omega9380/Retro-Schematics/Commodore/Amiga/Amiga 1000/Documents/A1000 Daughter Board.jpg

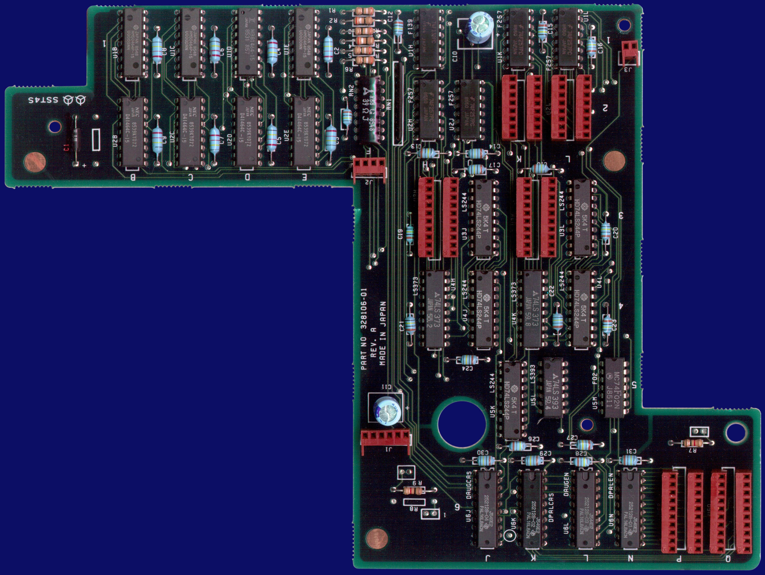
Commodore/Amiga/Amiga 1000/Documents/A1000 Daughter Board.jpg
