omega9380/Retro-Schematics/Commodore/Amiga/Amiga 1000/Documents/A1000_MB.jpg

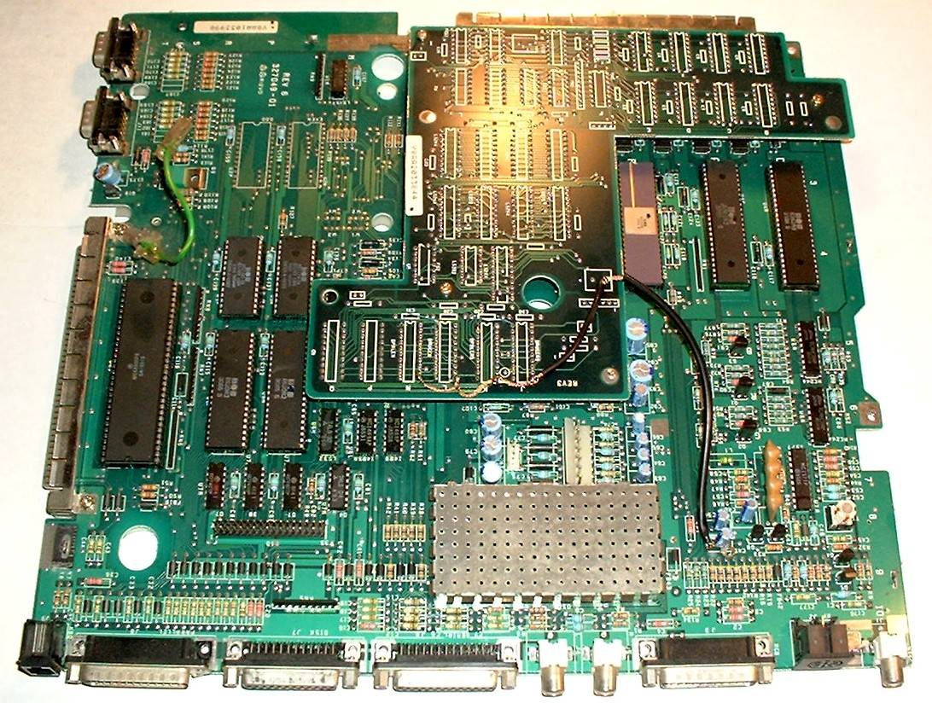
Commodore/Amiga/Amiga 1000/Documents/A1000_MB.jpg
