omega9380/Retro-Schematics/Commodore/Amiga/Amiga 1000/Documents/A1000 Zorro Expansion bus [August, 1985 - PN-328015 Commodore - Rev C].pdf

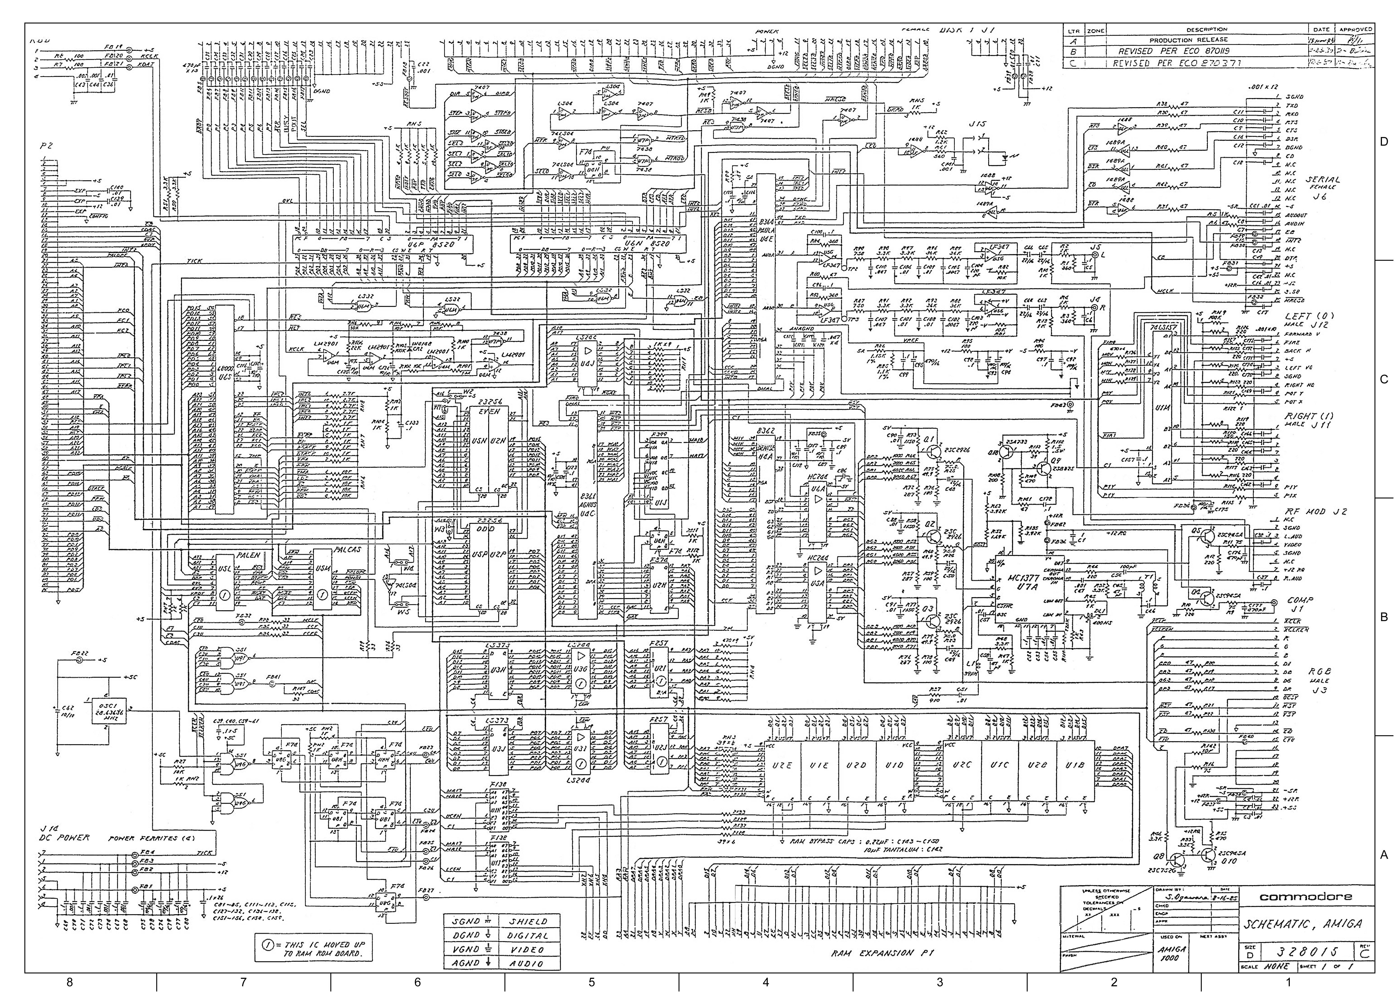
[picture p3: page 1]
