omega9380/Retro-Schematics/Commodore/Amiga/Amiga 1000/Documents/amiga_1000_schematic_1.png

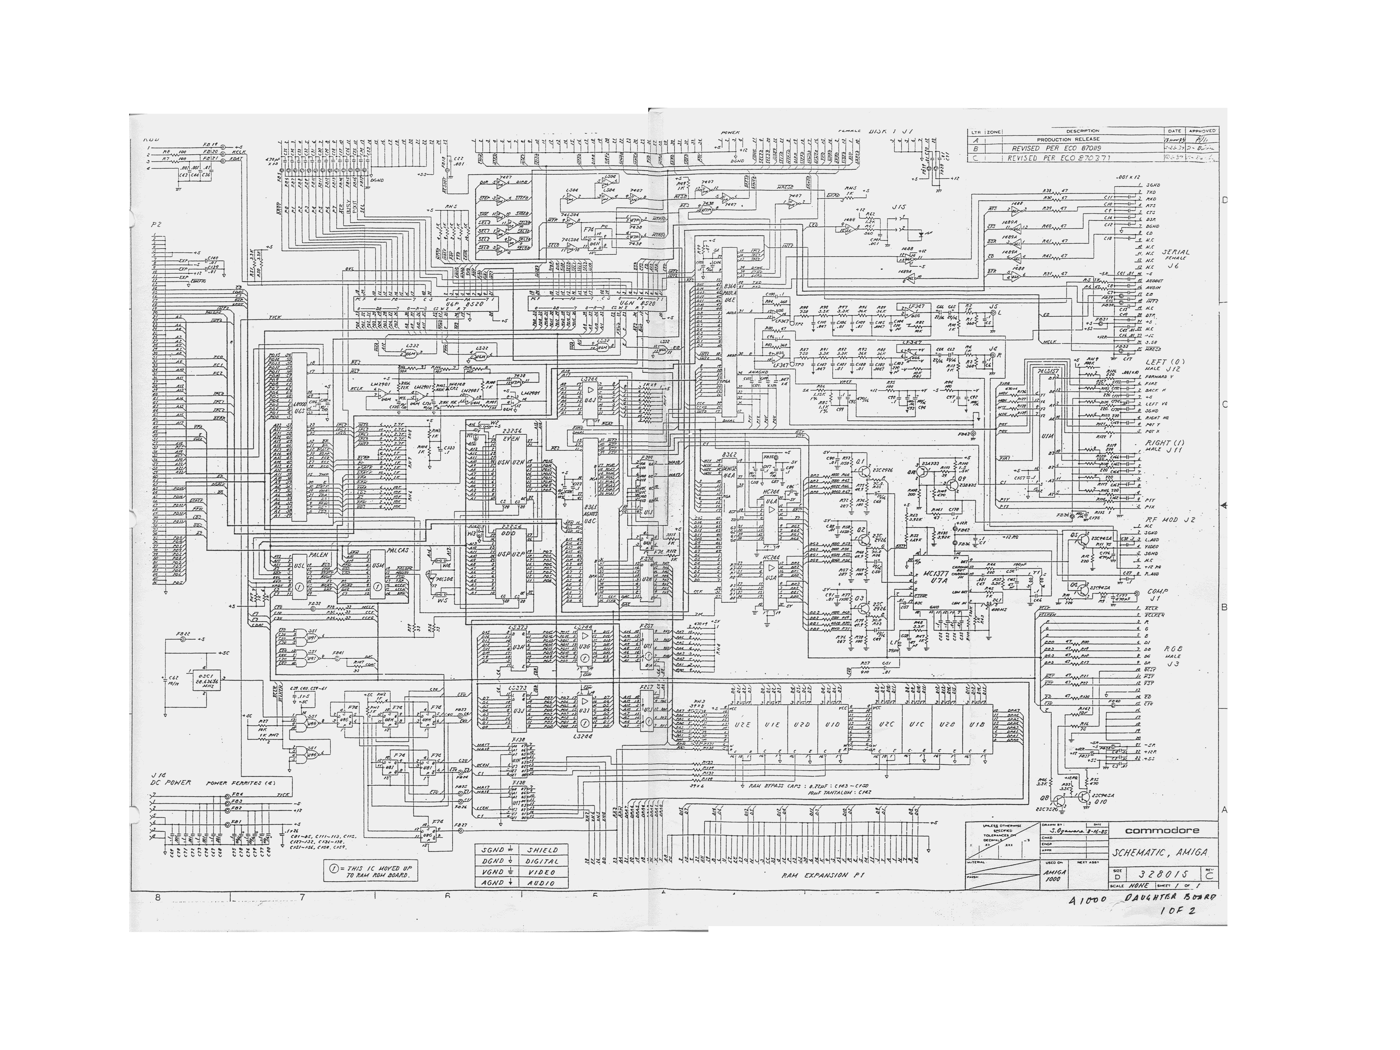
Commodore/Amiga/Amiga 1000/Documents/amiga_1000_schematic_1.png
