omega9380/Retro-Schematics/Commodore/Amiga/Amiga 1000/Documents/Circuit1a.png

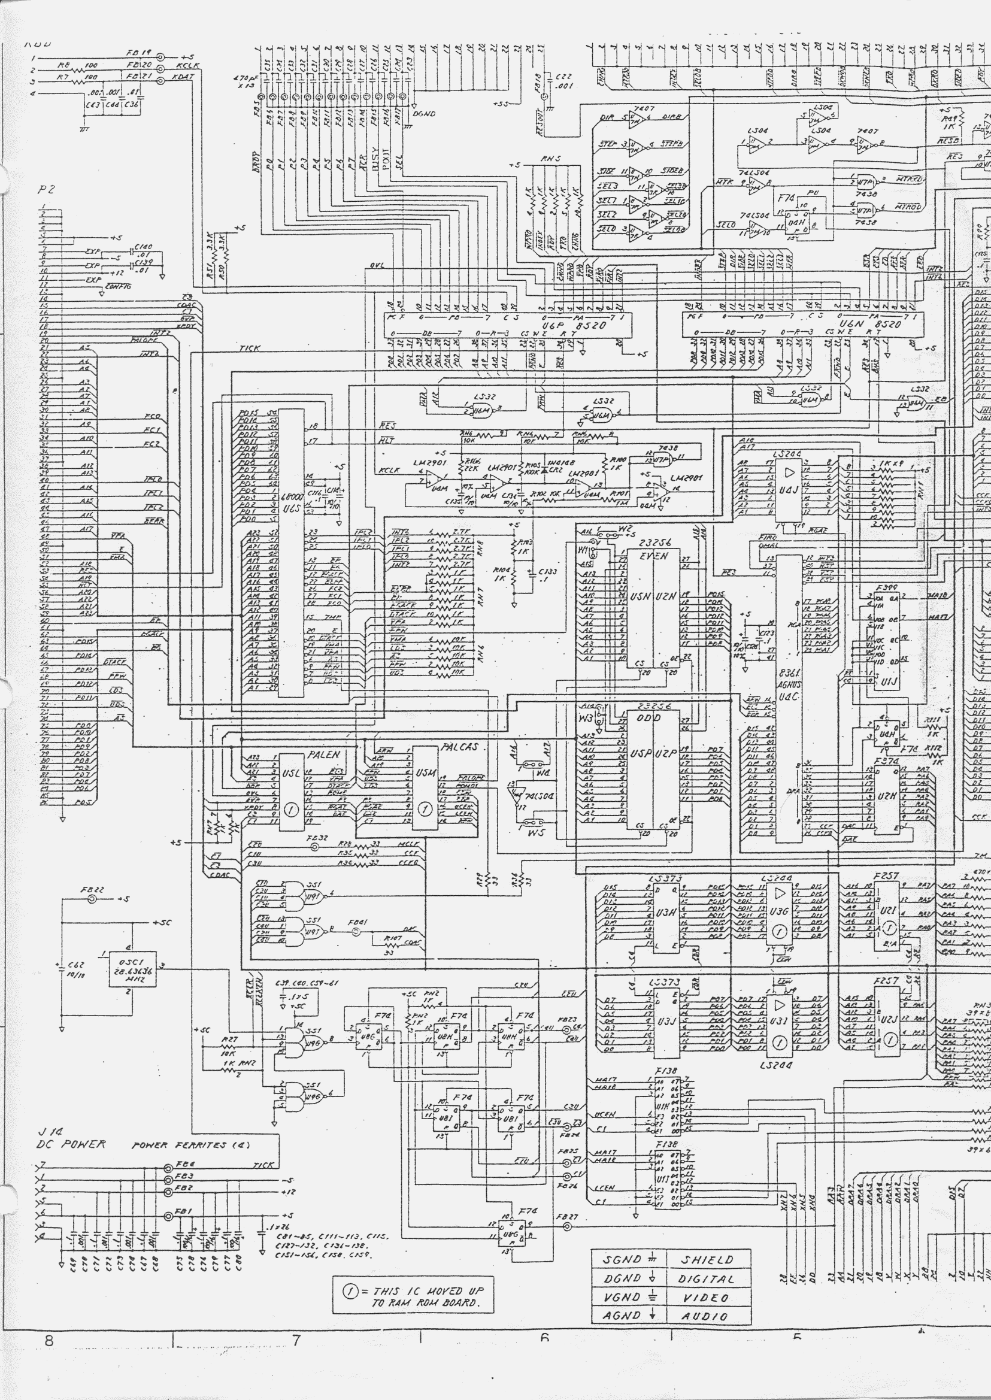
Commodore/Amiga/Amiga 1000/Documents/Circuit1a.png
