omega9380/Retro-Schematics/Commodore/Amiga/Amiga 1000/Documents/Circuit1b.png

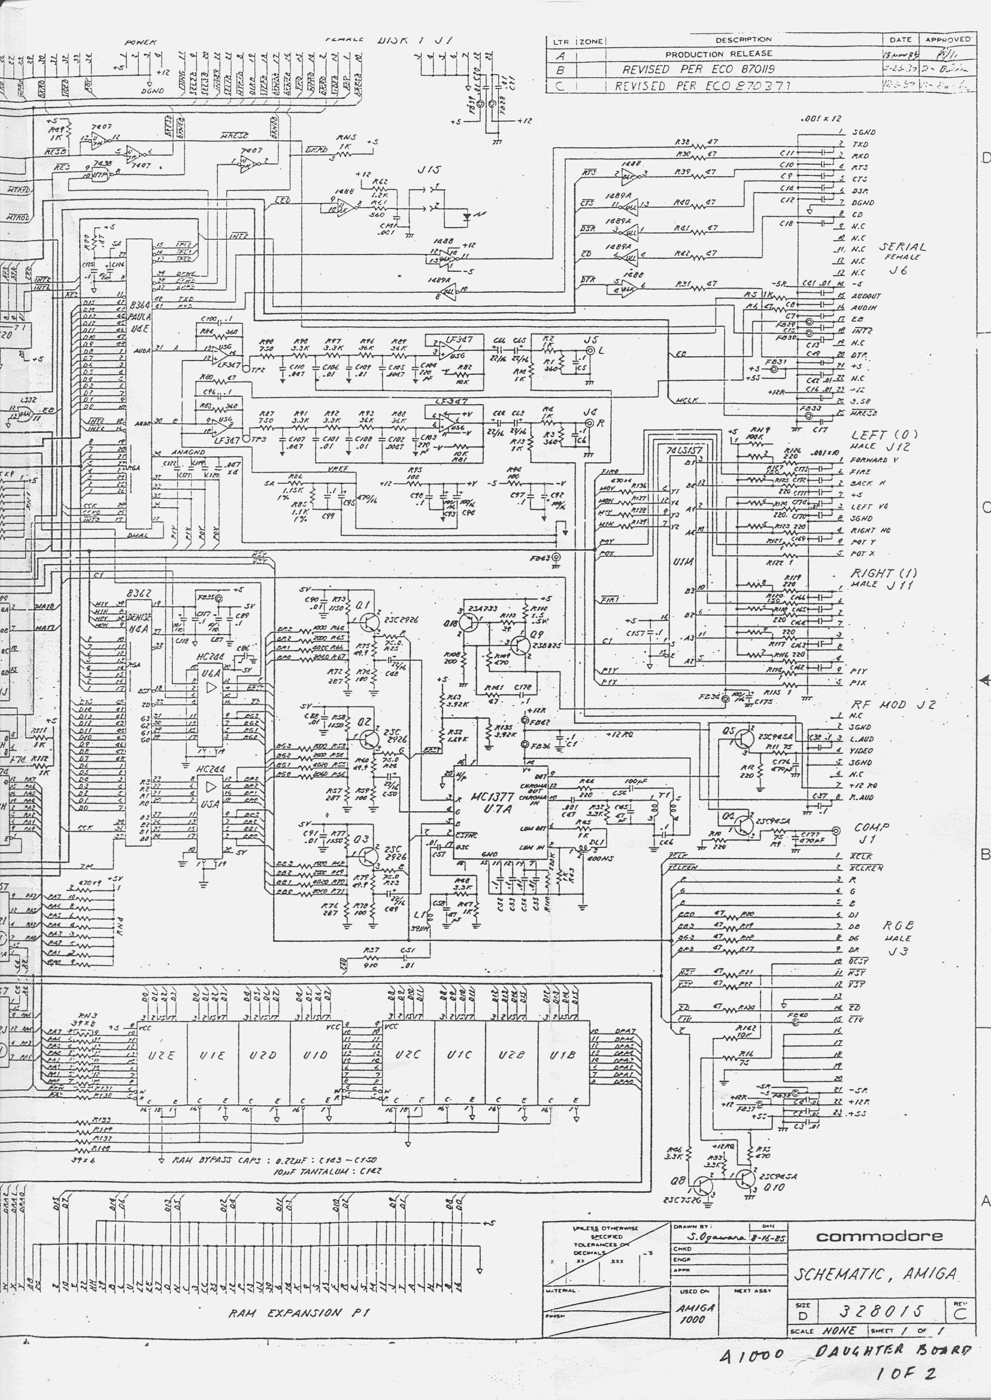
Commodore/Amiga/Amiga 1000/Documents/Circuit1b.png
