omega9380/Retro-Schematics/Commodore/Amiga/Amiga 1000/Documents/Datasheets/pinouts/8361-Agnus-dip.png

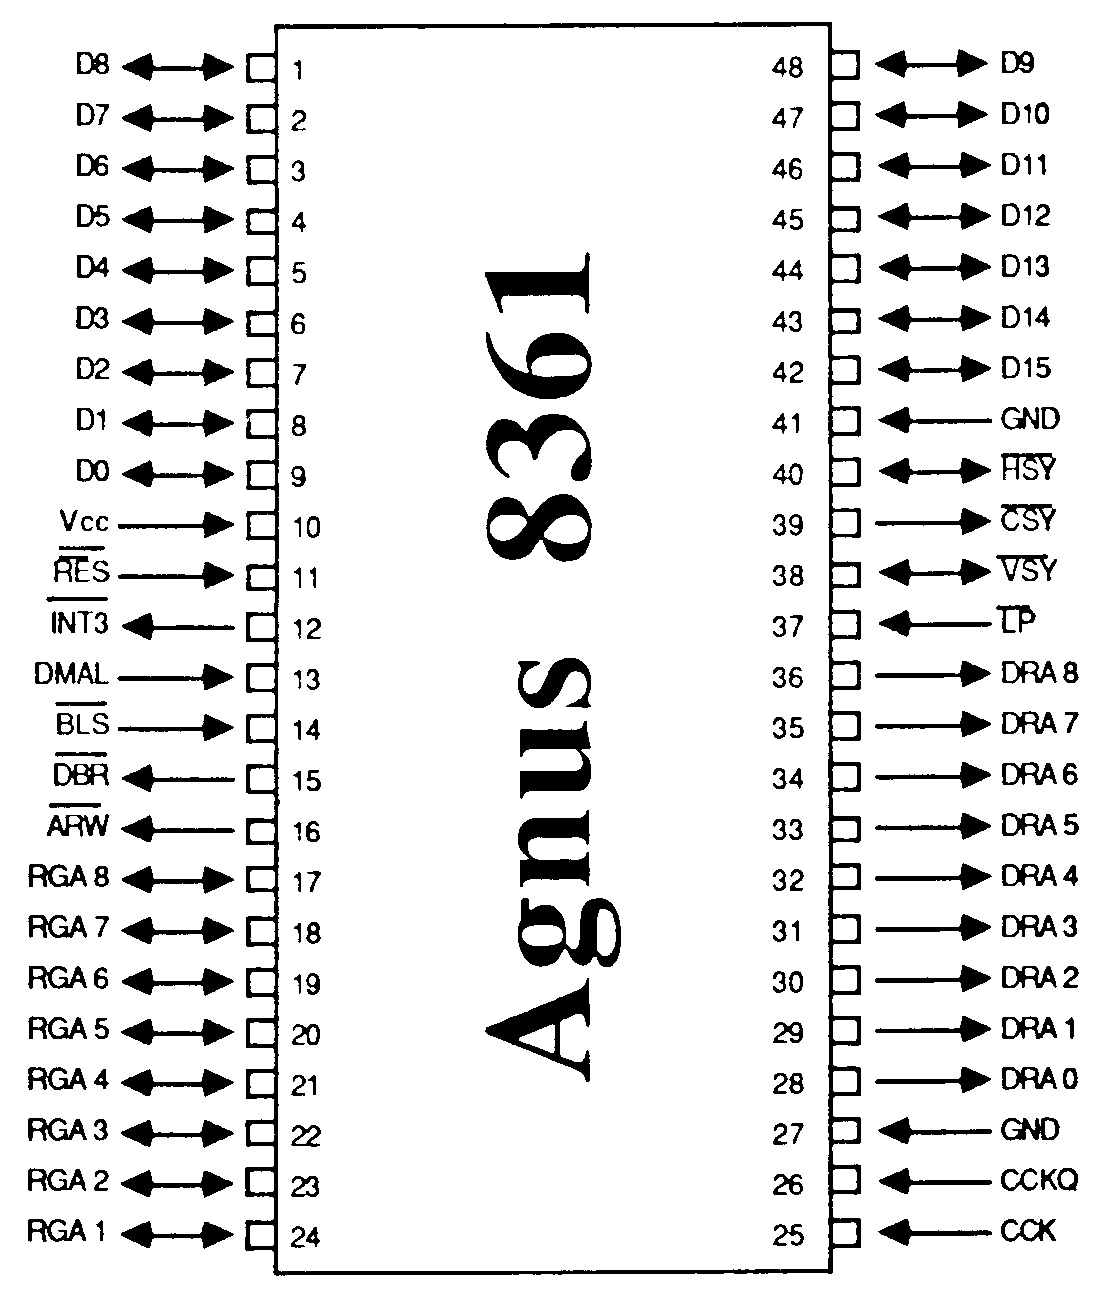
Commodore/Amiga/Amiga 1000/Documents/Datasheets/pinouts/8361-Agnus-dip.png
