omega9380/Retro-Schematics/Commodore/Amiga/Amiga 1000/Documents/Datasheets/pinouts/8370-agnus-plcc.png

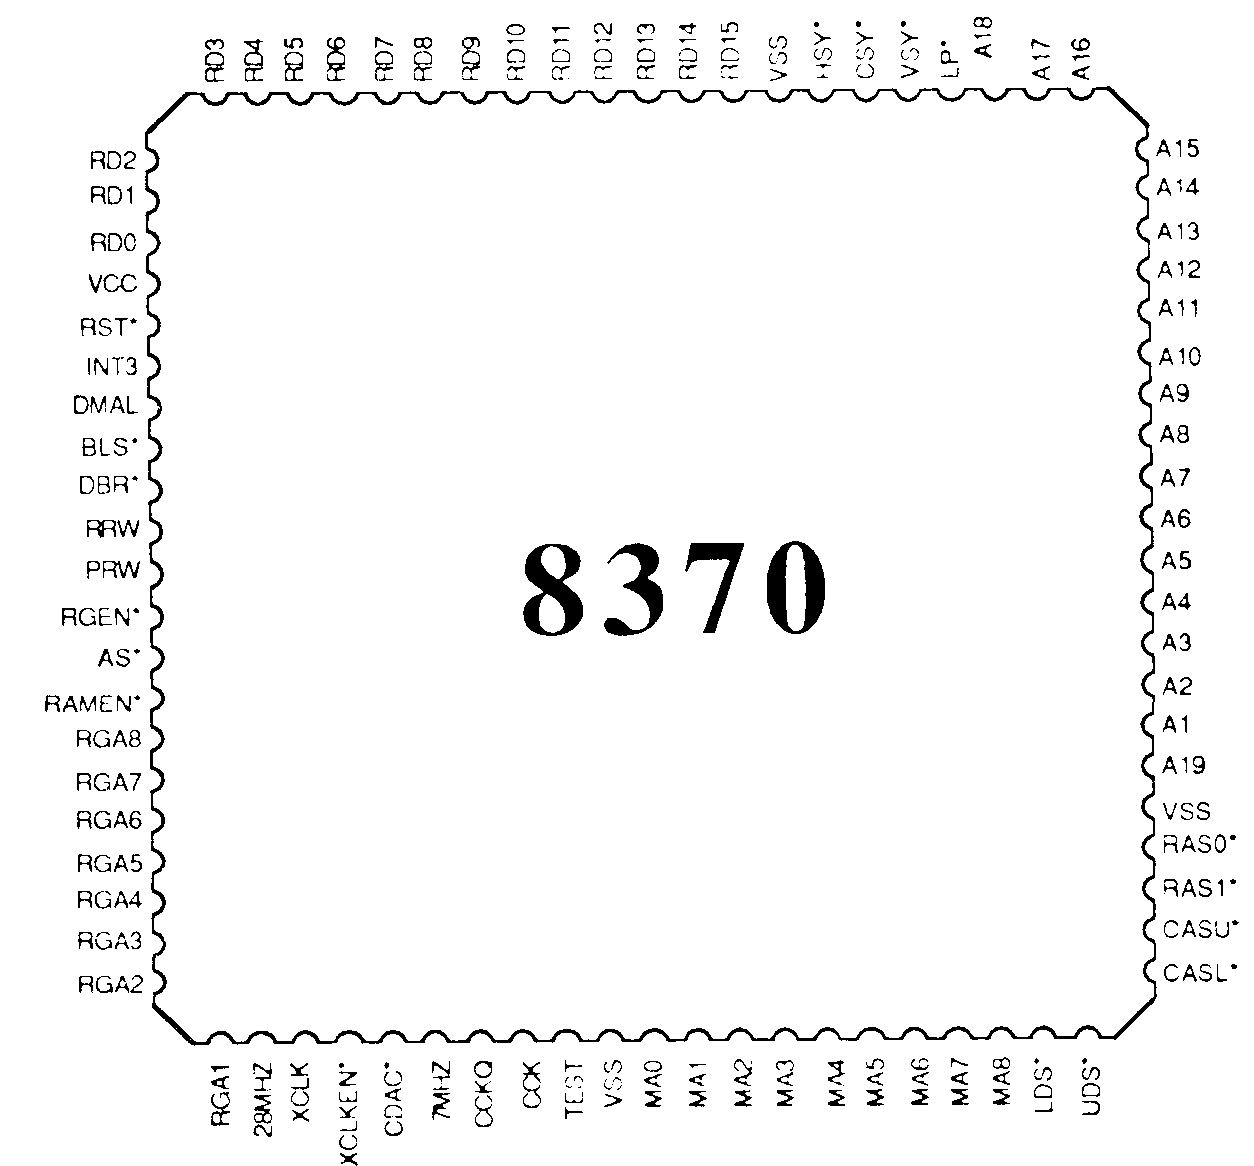
Commodore/Amiga/Amiga 1000/Documents/Datasheets/pinouts/8370-agnus-plcc.png
