omega9380/Retro-Schematics/Commodore/Amiga/Amiga 1000/Documents/Datasheets/pinouts/8520-CIA-dip.png

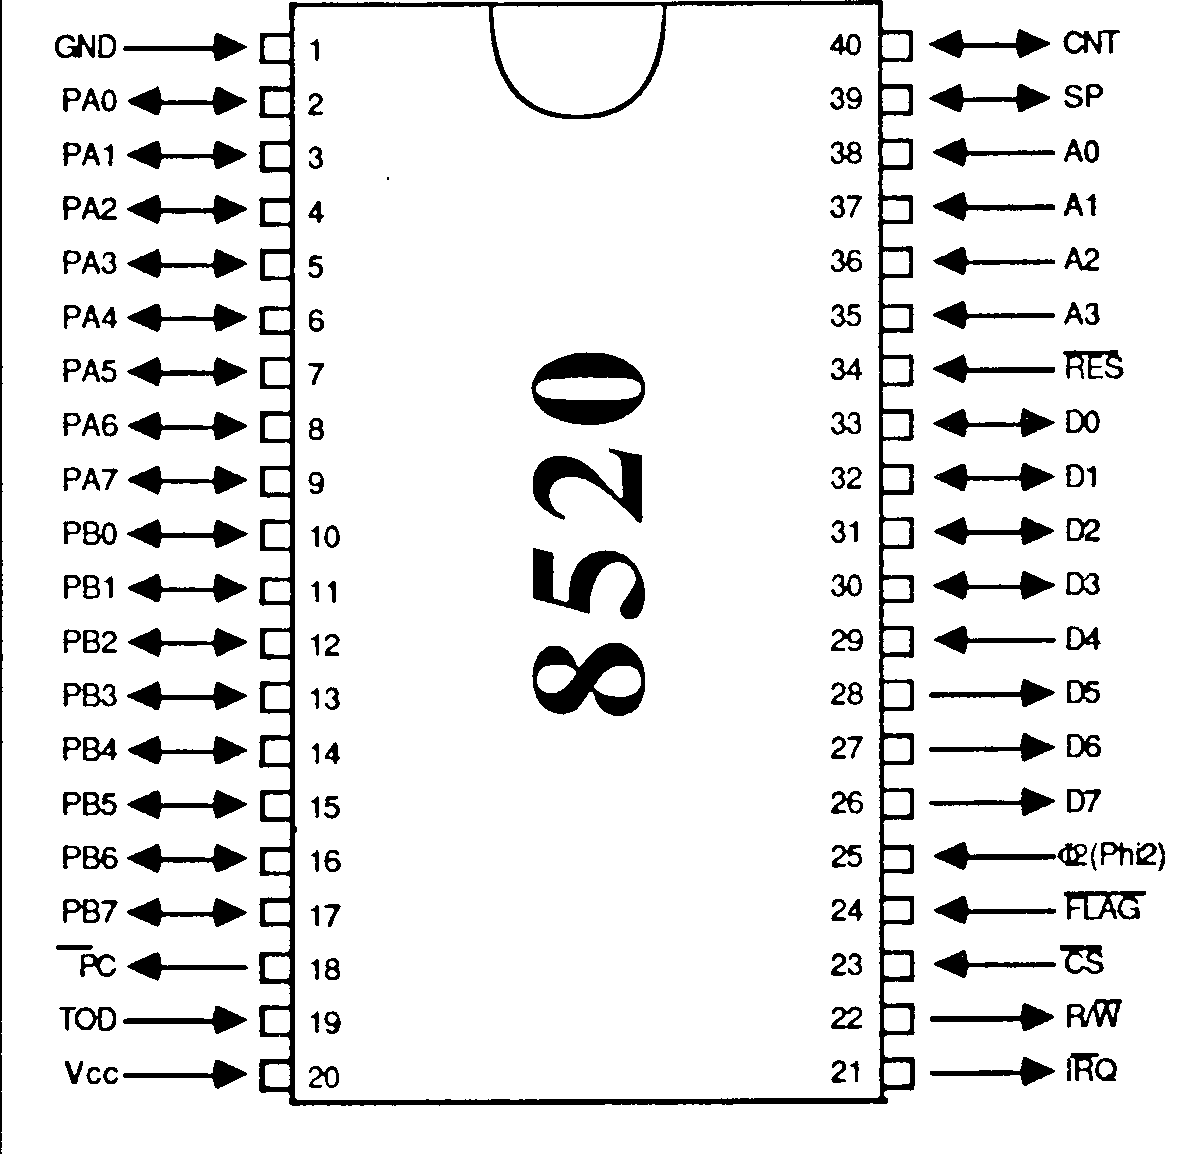
Commodore/Amiga/Amiga 1000/Documents/Datasheets/pinouts/8520-CIA-dip.png
