omega9380/Retro-Schematics/Commodore/Amiga/Amiga 1000/Documents/Datasheets/pinouts/68000-cpu-dip.png

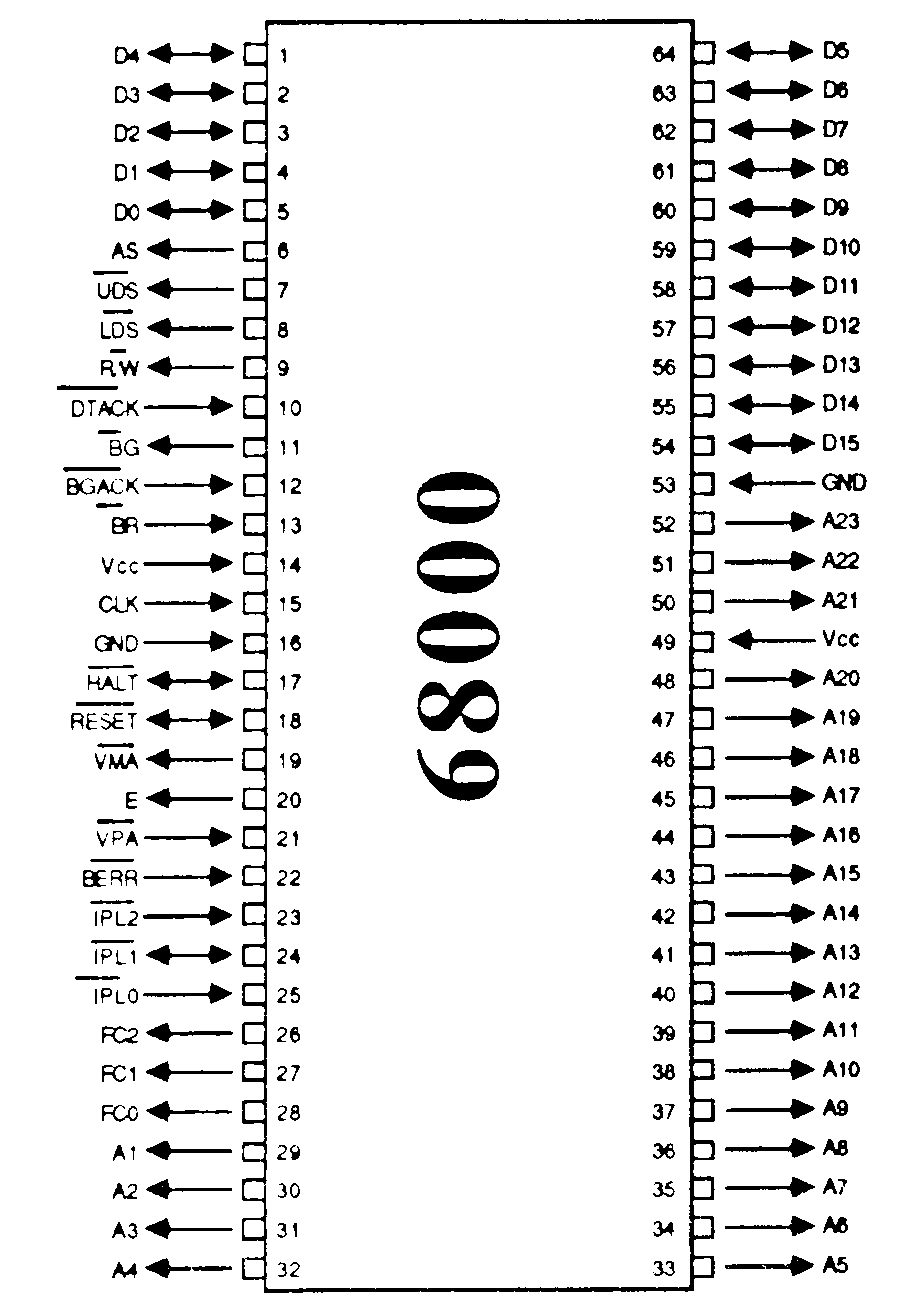
Commodore/Amiga/Amiga 1000/Documents/Datasheets/pinouts/68000-cpu-dip.png
