omega9380/Retro-Schematics/Commodore/Amiga/Amiga 1000/Documents/Datasheets/pinouts/68000.gif

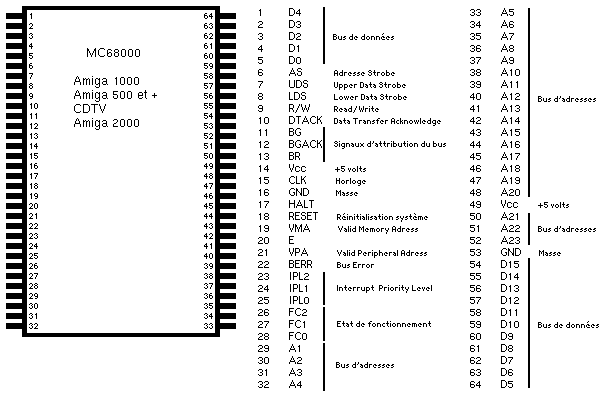
Commodore/Amiga/Amiga 1000/Documents/Datasheets/pinouts/68000.gif
