omega9380/Retro-Schematics/Commodore/Amiga/Amiga 1000/Documents/Datasheets/pinouts/aa-gayle-plcc.png

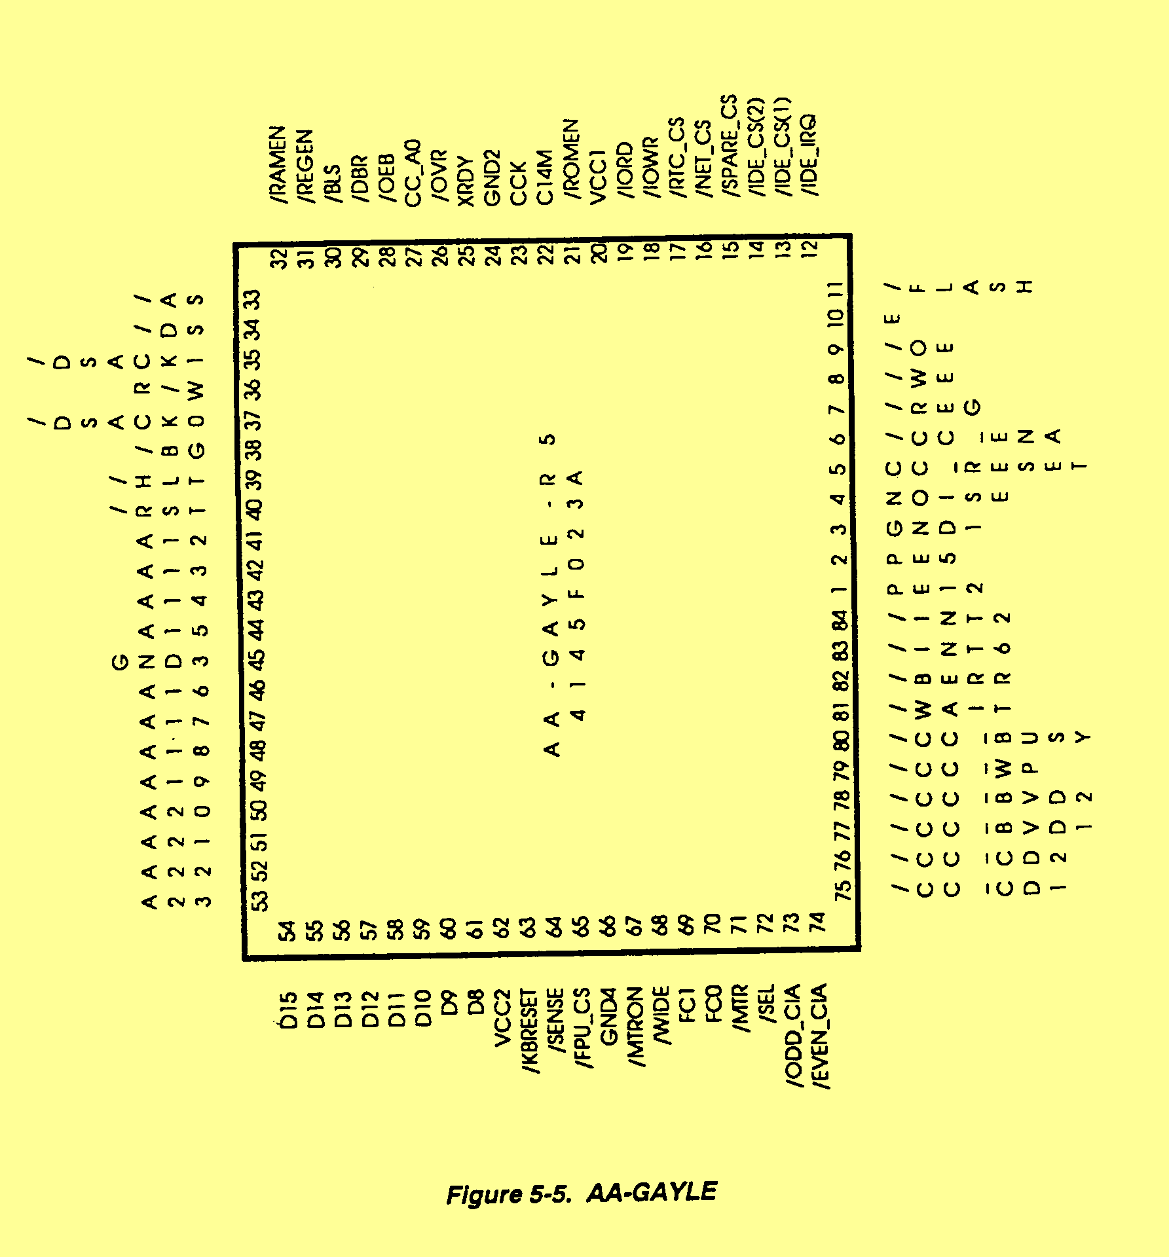
Commodore/Amiga/Amiga 1000/Documents/Datasheets/pinouts/aa-gayle-plcc.png
