omega9380/Retro-Schematics/Commodore/Amiga/Amiga 1000/Documents/Datasheets/pinouts/CIA-B.gif

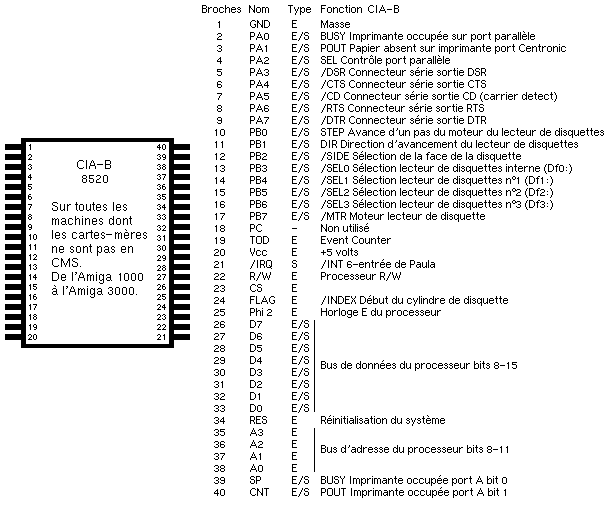
Commodore/Amiga/Amiga 1000/Documents/Datasheets/pinouts/CIA-B.gif
