omega9380/Retro-Schematics/Commodore/Amiga/Amiga 1000/Documents/Datasheets/pinouts/Denise.gif

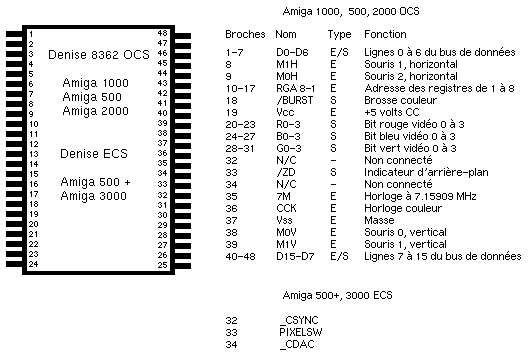
Commodore/Amiga/Amiga 1000/Documents/Datasheets/pinouts/Denise.gif
