omega9380/Retro-Schematics/Commodore/Amiga/Amiga 1000/Documents/Datasheets/pinouts/FatAgnus8372.gif

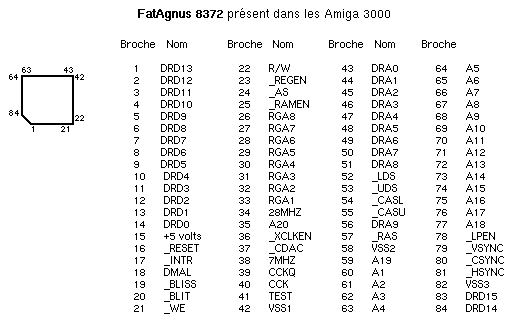
Commodore/Amiga/Amiga 1000/Documents/Datasheets/pinouts/FatAgnus8372.gif
