omega9380/Retro-Schematics/Commodore/Amiga/Amiga 1000/Documents/Datasheets/pinouts/ROM.gif

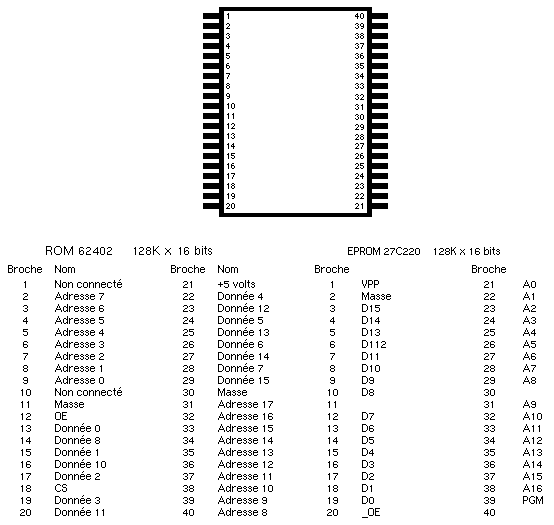
Commodore/Amiga/Amiga 1000/Documents/Datasheets/pinouts/ROM.gif
