omega9380/Retro-Schematics/Commodore/Amiga/Amiga 1000/Documents/Datasheets/pinouts/tsop-package-pic.gif

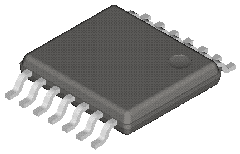
Commodore/Amiga/Amiga 1000/Documents/Datasheets/pinouts/tsop-package-pic.gif
