omega9380/Retro-Schematics/Commodore/Commodore 64/Commodore 64 - Schematic 251138 for PCB Assy 250407/Documents/250469-rev.B-left-corrected2.gif

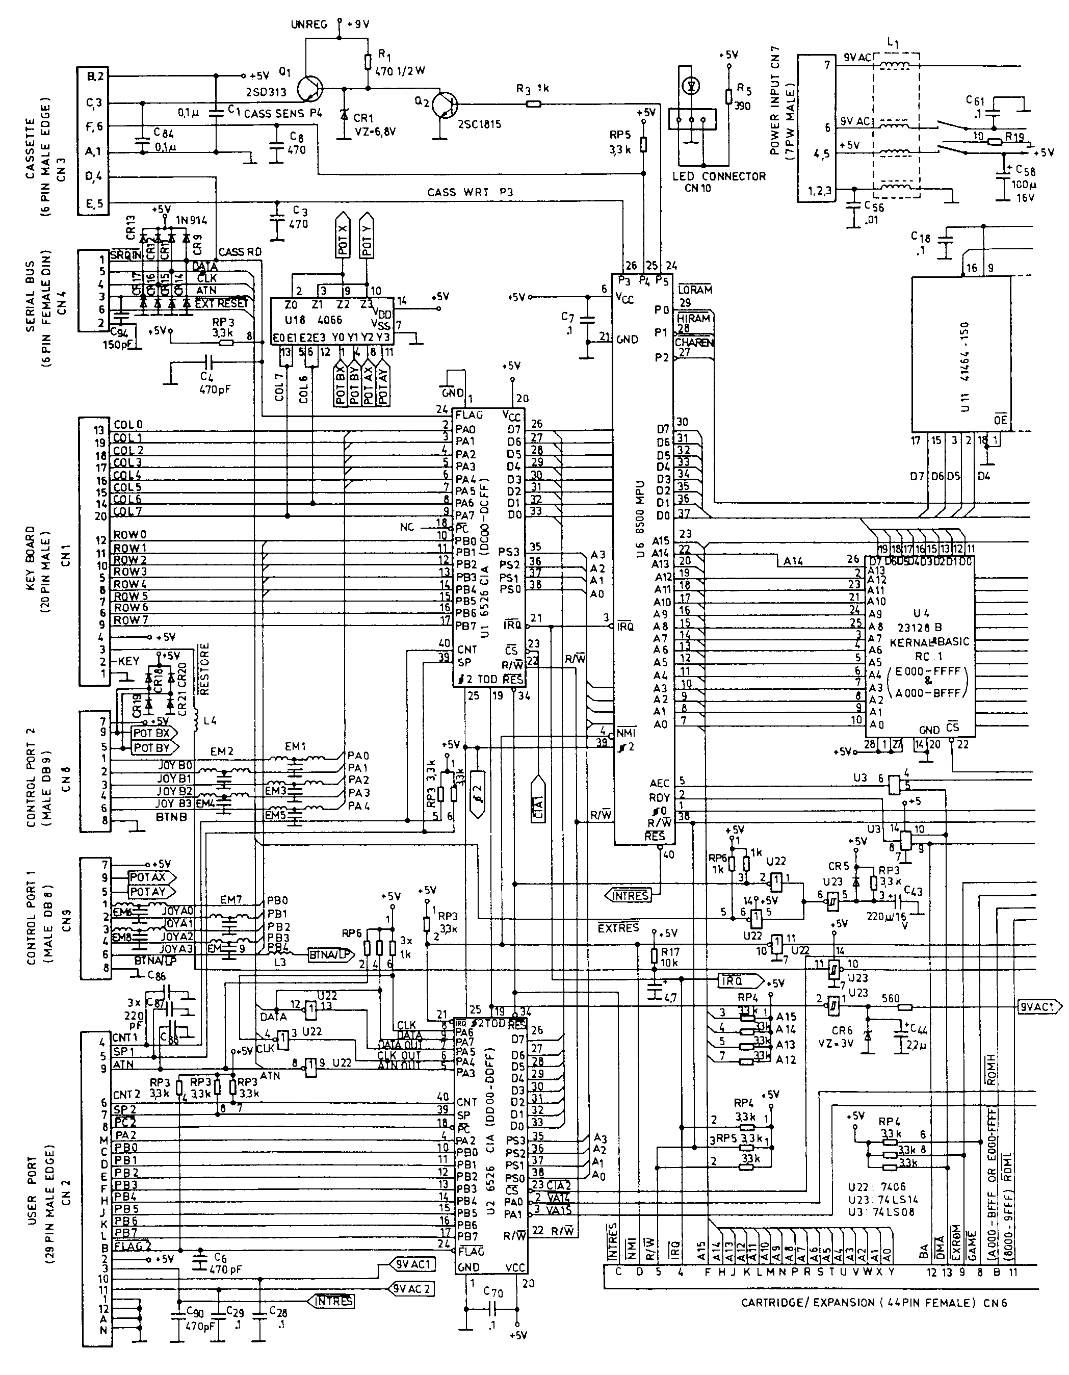
Commodore/Commodore 64/Commodore 64 - Schematic 251138 for PCB Assy 250407/Documents/250469-rev.B-left-corrected2.gif
