omega9380/Retro-Schematics/Commodore/Commodore 64/Commodore 64 - Schematic 251138 for PCB Assy 250407/Documents/251138 - 1 of 2 combined.png

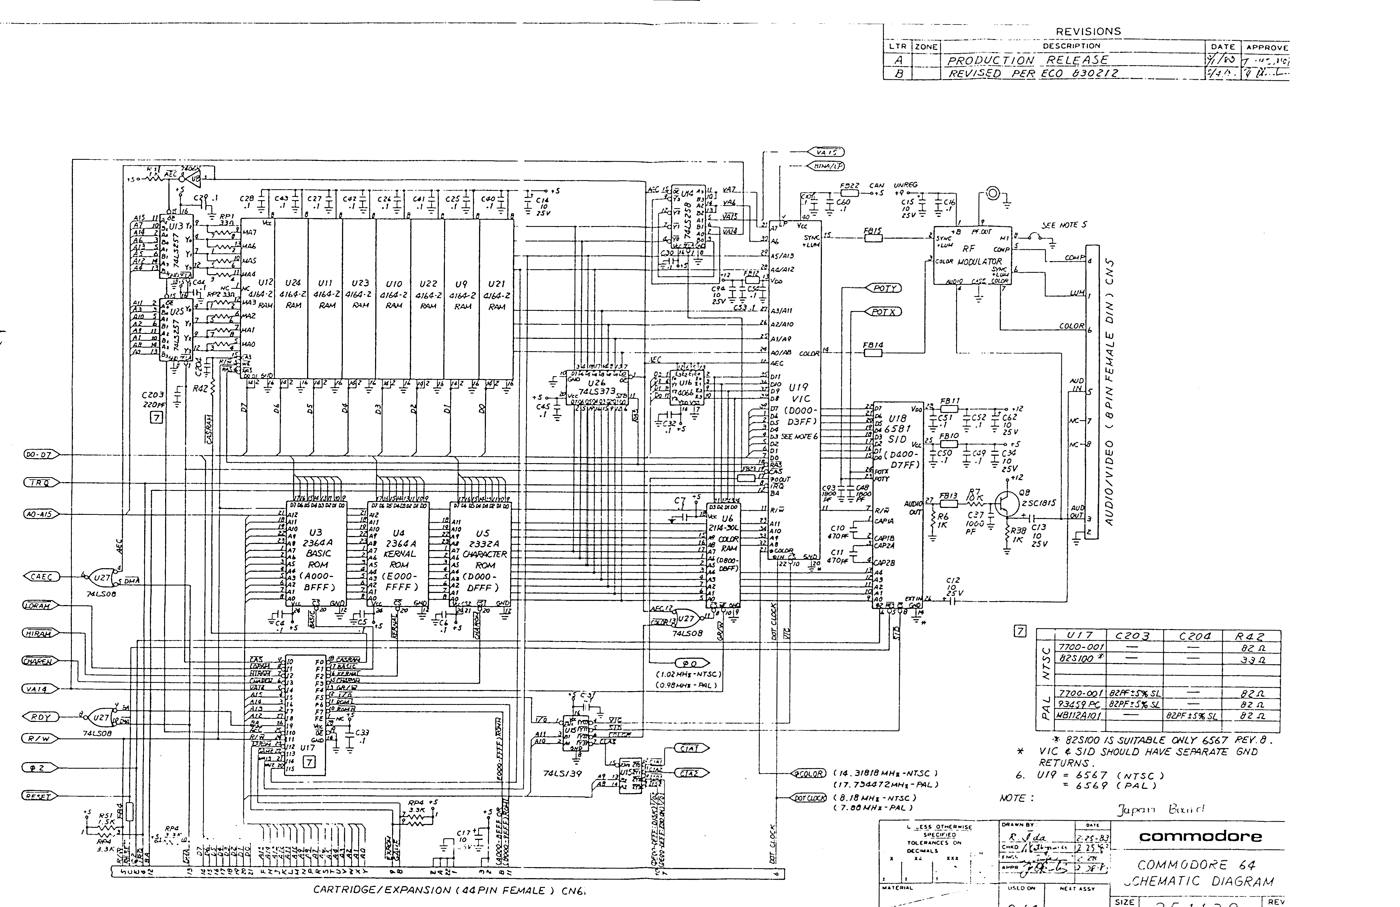
Commodore/Commodore 64/Commodore 64 - Schematic 251138 for PCB Assy 250407/Documents/251138 - 1 of 2 combined.png
