omega9380/Retro-Schematics/Commodore/Amiga/Amiga 1000/Amiga 1000.kicad_sch

## KiCad design Commodore/Amiga/Amiga 1000/Amiga 1000.kicad_sch (2022-06-29)

Schematic: Amiga 1000.kicad_sch

Parts:
C1, C5, C6, C36, C37, C38, C40, C46, C52, C53, C59, C60, C61, C67, C69, C71, C73, C75, C76, C77, C86, C89, C97, C98, C99, C116, C117, C123, C125, C157, C178: .1
C2, C3, C4, C16, C20, C21, C41, C42, C51, C55, C56, C57, C88, C90, C91, C101, C106, C108, C109, C139, C140, C174: .01
C7, C8, C9, C10, C11, C12, C13, C14, C15, C17, C18, C19, C22, C43, C44, C47, C68, C70, C72, C74, C141, C162, C163, C164, C165, C166, C169, C170, C171, C172, C173: .001
C23, C24, C25, C26, C27, C28, C29, C30, C31, C32, C33, C34, C35, C176, C177: 470pF
C45: 47pF
C48, C49, C50, C63, C64, C65, C66: 22 16V
C54: 100pF
C62, C87, C114, C118, C124, C134, C135: 10 10V
C78, C79, C80, C92, C93, C94, C175: 100 16V
C95: 470 16V
C96, C100, C133: 0.1
C102, C105: .0047
C103, C104: 220pF
C107, C110, C119, C120, C121, C122: .047
C126: 10µF
C137,C138,C158,C159,C113,C115,C129,C130,C131,C132,C151,C152,C153,C154,C155,C156,C127,C128,C136,C111,C112,C81,C82,C83,C84,C85: .1 x26
C142: 10 10V TANT
C143..C150: .22 x8
CR2: 1N4148
D1: LED
DL1: 400ns
FB1, FB2, FB3, FB4, FB5, FB6, FB7, FB8, FB9, FB10, FB11, FB12, FB13, FB14, FB15, FB16, FB17, FB18, FB19, FB20, FB21, FB22, FB23, FB24, FB25, FB26, FB27, FB28, FB29, FB30, FB31, FB33, FB34, FB35, FB36, FB37, FB38, FB39, FB40, FB41, FB42, FB43: FERRITE_BEAD
J1: COMP
J2: RF MOD
J3: RGB
J4: L
J5: R
J6: SERIAL
J7: DISK 1
J8: PARALLEL
J9: KBD
J10: DISK 0
J11: RIGHT (1)
J12: LEFT (0)
J13: D0 PWR
J14: DC POWER
J15: CONN_LED
L1: 39µH
N1: ROM_BRD_NOTE
N2: NOTE_GROUNDS
OSC1: 28.63636MHz
P1: RAM EXPANSION
Q1, Q2, Q3: 2SC2926; TO-3PB-3_Vertical
Q4, Q5, Q10: 2SC945A; TO-3PB-3_Vertical
Q8: 2SC752G; TO-3PB-3_Vertical
Q9: 2SB825; TO-92_Inline
Q18: 2SA733; TO-92_Inline
R1, R3, R83, R84: 360
R2, R4, R13, R14, R43, R45, R47, R49, R100, R103, R104, R111, R112: 1K
R5, R6, R17, R18, R19, R20, R21, R22, R30, R31, R38, R39, R40, R41, R42, R80, R134, R141: 47
R7, R8, R59, R74, R78, R94, R95: 100
R9, R11, R16: 75
R10, R12, R44, R116, R117, R118, R119, R123, R124, R125, R126: 220
R15, R109, R136, R137, R138, R139: 470
R23, R24, R25: 75.0
R27, R81, R82, R102, R142: 10K
R28, R29, R34, R36, R107: 33
R32, R33, R48, R91, R92, R97, R98: 3.3K
R35, R63: 3.92K
R37: 910
R50, R51: 3.3.K
R52: 1.69K
R53, R64, R68: 1000
R54, R65, R69: 2000
R55, R66, R70: 4020
R56, R67, R71: 8060
R57, R72, R76: 287
R58, R73, R77: 1150
R60, R75, R79: 49.9
R61: 560
R62: 1.2K
R85: 1.1K 1%
R86: 1.15K 1%
R87, R90: 750
R88, R89, R93, R96: 36K
R99: 0.47
R101: 1M
R105: 100K 10%
R106: 22K 10%
R108: 200
R110: 1.5 .5W
R113, R128, R129, R130, R131, R132, R133: 39
R114, R115, R121, R122: 1
R120, R127: 150
R140: 220K
RN1, RN2-, RN5, RN7-: 1K
RN3: 39
RN4: 470
RN6, RN6-: 10K
RN8-: 2.7K
RN9: 100K
ROM1: Amiga_1000_RAM_Bank_1; DIP-18_W7.62mm_LongPads
ROM2: Amiga_1000_RAM_Bank_2; DIP-18_W7.62mm_LongPads
T1: 166NNF-10264AG
TP1, TP2, TP3: TestPoint
U1H, U1I: 74F138
U1J: 74F399
U1M: 74LS157
U2H: 74F374
U2I, U2J: 74F257_U2I_J; DIP-16_W7.62mm_LongPads
U3G: 74LS244_U3G
U3H: 74LS373_U3H
U3I: 74LS244_U3I
U3J: 74LS373_U3J
U4A: MOS8362; DIP-48_W15.24mm_LongPads
U4C: MOS8361
U4E: MOS8364
U4H-, U8G-, U8H-, U8I-: 74F74
U4J: 74LS244
U4M-: LM2901
U5A, U6A: 74HC244
U5G-: LF347; DIP-14_W7.62mm_LongPads
U5L: PALEN - U5L
U5M: PALCAS - U5M
U5N, U5P: 23256; DIP-28_W15.24mm_LongPads
U6K, U6K-: LM1488; DIP-14_W7.62mm_LongPads
U6L-: LM1489A; DIP-14_W7.62mm_LongPads
U6M-: 74LS32
U6N, U6P: MOS8520; DIP-40_W15.24mm_LongPads
U6S: Motorola_68000; DIP-64_W15.24mm
U7A: MC1377; DIP-20_W7.62mm_LongPads
U7F-, U7M-: 74LS04
U7N-, U7R-: 7407
U7P-: 7438
U9G-, U9I-: 74S51
W1, W2, W3, W4, W5: UNKNOWN_W_SYMBOL

Connections:
7MP: R29.1, R29.2, R36.1, R36.2, U4A.35 (C7M), U6S.15 (CLK), U9I-.6
+5K: C36.1, FB19., J9.1 (+5V)
+5L: C178.2, FB34., Q9.2 (C), R109.1
+5LF: C174.1, C175.2, FB34., J11.7 (+5V), J12.7 (+5V)
+5U: C69.1, C70.1, FB1., J14.5 (+5V), J14.6 (+5V)
+5V: C3.1, C36.2, C40.2, C42.1, C59.2, C60.2, C61.2, C62.2, C75.1, C78.1, C86.1, C87.1, C88.2, C89.2, C90.2, C91.2, C114.1, C116.2, C117.2, C118.1, C123.2, C124.2, C125.1, C126.1, C137,C138,C158,C159,C113,C115,C129,C130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.1, C142.1, C143..C150.2, C157.1, CR2.1 (K), FB1., FB19., FB22., FB31., FB35., FB39., J3.23 (+5V), J6.21 (+5V), J8.23 (+5V), J13.1 (+5V), OSC1.4, P1.3 (DGND), P1.5 (+5V), P1.6 (+5V), P1.7 (EXP), P1.11 (EXP), P1.15 (CDAC), P1.29 (A1), P1.30 (A8), P1.C (+5V), P1.H (+5V), P1.HH (+5V), P1.JJ (+5V), P1.M (+5V), P1.S (+5V), Q1.2 (C), Q2.2 (C), Q3.2 (C), Q18.3 (E), R15.2, R27.1, R49.2, R50.1, R51.1, R58.2, R63.2, R73.2, R77.2, R86.1, R99.1, R99.2, R100.2, R103.2, R105.2, R106.2, R110.2, R111.2, R112.2, R142.1, RN1., RN2-., RN4., RN5., RN6., RN6-., RN7-., RN8-., RN9., ROM1.9 (VCC), U1M.15 (E), U1M.16 (VCC), U4A.19 (VCC), U4C.10 (VCC), U4E.27 (VCC), U4M-.3 (V+), U5A.20 (VCC), U6A.20 (VCC), U6N.20 (VCC), U6P.20 (VCC), U6S.14 (VCC), U6S.49 (VCC), U9G-.14, U9I-.14, W2.
+12U: C71.1, C72.1, FB2., J14.2 (+12V)
+12V: C1.2, C2.1, C16.1, C76.1, C79.1, C139.2, FB2., FB28., FB36., FB37., FB42., J2.7 (+12V), J3.22 (+12V), J6.23 (+12V), J13.4 (+12V), P1.10 (+12), Q4.2 (C), Q5.2 (C), R33.2, R62.1, R95.1, U6K-.14 (V+)
+VSW: C93.1, C94.1, C98.1, R95.2
-5U: C73.1, C74.1, FB3., J14.1 (-5V)
-5V: C4.1, C41.1, C77.1, C80.2, C140.2, FB3., FB38., J3.21 (-5V), J6.14 (-5V), P1.8 (-5V), R81.1, R82.1, R94.1, U6K-.1 (V-)
-VSW: C92.1, C97.1, R94.2
A1: P1.29 (A1), U2I.5 (I0b), U4J.8 (I3a), U5N.10 (A1), U5P.10 (A1), U6S.29 (A1)
A2: P1.27 (A2), U2J.5 (I0b), U4J.11 (I0b), U5N.9 (A2), U5P.9 (A2), U6S.30 (A2)
A3: P1.26 (A3), U2I.2 (I0a), U4J.6 (I2a), U5N.8 (A3), U5P.8 (A3), U6S.31 (A3)
A4: P1.24 (A4), U2J.2 (I0a), U4J.13 (I1b), U5N.7 (A4), U5P.7 (A4), U6S.32 (A4)
A5: P1.21 (A5), U2J.14 (I0c), U4J.4 (I1a), U5N.6 (A5), U5P.6 (A5), U6S.33 (A5)
A6: P1.23 (A6), U2I.14 (I0c), U4J.15 (I2b), U5N.5 (A6), U5P.5 (A6), U6S.34 (A6)
A7: P1.28 (A7), U2J.11 (I0d), U4J.2 (I0a), U5N.4 (A7), U5P.4 (A7), U6S.35 (A7)
A8: P1.30 (A8), U2I.11 (I0d), U4J.17 (I3b), U5N.3 (A8), U5P.3 (A8), U6N.38 (A0), U6P.38 (A0), U6S.36 (A8)
A9: P1.32 (A9), U2I.6 (I1b), U5N.25 (A9), U5P.25 (A9), U6N.37 (A1), U6P.37 (A1), U6S.37 (A9)
A10: P1.34 (A10), U2J.6 (I1b), U5N.24 (A10), U5P.24 (A10), U6N.36 (A2), U6P.36 (A2), U6S.38 (A10)
A11: P1.36 (A11), U2I.3 (I1a), U5N.21 (A11), U5P.21 (A11), U6N.35 (A3), U6P.35 (A3), U6S.39 (A11)
A12: P1.38 (A12), U2J.3 (I1a), U5N.23 (A12), U5P.23 (A12), U6M-.1, U6S.40 (A12)
A13: P1.39 (A13), U2J.13 (I1c), U5N.2 (A13), U5P.2 (A13), U6M-.9, U6S.41 (A13)
A14: P1.41 (A14), U2I.13 (I1c), U5N.26 (A14), U5P.26 (A14), U6S.42 (A14), W3.
A15: P1.43 (A15), U2J.10 (I1d), U5N.27 (A15), U5P.27 (A15), U6S.43 (A15), W1.
A16: P1.45 (A16), U2I.10 (I1d), U6S.44 (A16), W2., W4.
A17: P1.47 (A17), U1J.3 (I0a), U6S.45 (A17), W4.
A18: P1.52 (A18), U1J.6 (I0b), U6S.46 (A18)
A19: P1.54 (A19), U5M.3 (I3), U6S.47 (A19)
A20: P1.56 (A20), U5M.2 (I2), U6S.48 (A20)
A21: P1.58 (A21), U5L.3 (I3), U6S.50 (A21)
A22: P1.57 (A22), U5L.2 (I2), U6S.51 (A22)
A23: P1.59 (A23), U5L.1 (I1), U6S.52 (A23)
AGND: C93.2, C95.2, C98.2, C99.2, C103.2, C104.2, C107.2, C108.2, C109.2, C110.2, C119.1, C120.1, C121.1, C122.1, FB43., R85.1, U4E.34 (ANAGND)
AUDIN: R6.1, R80.2
B: J3.5 (B_{∩}), R23.2
BB0: R20.1, R71.1, U5A.3 (2Y0)
BB1: R70.1, U5A.5 (2Y1)
BB2: R69.1, U5A.7 (2Y2)
BB3: R19.1, R68.1, U5A.9 (2Y3)
BG0: R56.1, U6A.3 (2Y0)
BG1: R55.1, U6A.5 (2Y1)
BG2: R54.1, U6A.7 (2Y2)
BG3: R18.1, R53.1, U6A.9 (2Y3)
BR0: R67.1, U5A.16 (1Y1)
BR1: R66.1, U5A.14 (1Y2)
BR2: R65.1, U5A.18 (1Y0)
BR3: R17.1, R64.1, U5A.12 (1Y3)
BUSY: FB15., U6N.2 (PA0), U6N.39 (SP)
C1: FB26., U1H.4 (E1), U1I.4 (E1), U1M.1 (S)
C1U: R35.1, U9I-.4
C2U: U9I-.9
C3U: R34.1, U8I-.5 (Q), U9I-.3
C4: FB23., U1J.9 (CP), U2I.1 (B/A), U2J.1 (B/A), U3H.11 (L), U3J.11 (L)
C4U: FB23., U8H-.5 (Q), U9I-.1
CCK: R35.2, U4A.36 (~CAS), U4C.25 (CCK), U4E.28 (CCK)
CCKQ: R34.2, U4C.26 (CCKQ), U4E.29 (CCKQ)
CDAC: P1.15 (CDAC), R107.2
D0: P1.16 (~C1), ROM1.17 (I/O_{4}), U3I.3 (2Y4), U3J.8 (4D), U4A.7 (D0), U4C.9 (D0), U4E.10 (D0)
D1: P1.T (D1), ROM1.15 (I/O_{3}), U3I.18 (1Y1), U3J.13 (5D), U4A.6 (D1), U4C.8 (D1), U4E.9 (D1)
D2: P1.R (D2), ROM1.2 (I/O_{2}), U3I.16 (1Y2), U3J.14 (6D), U4A.5 (D2), U4C.7 (D2), U4E.7 (D2)
D3: P1.14 (~C3), ROM1.3 (I/O_{1}), U3I.5 (2Y3), U3J.7 (3D), U4A.4 (D3), U4C.6 (D3), U4E.6 (D3)
D4: P1.12 (~CONFIG), ROM1.17 (I/O_{4}), U3I.7 (2Y2), U3J.4 (2D), U4A.3 (D4), U4C.5 (D4), U4E.5 (D4)
D5: P1.N (D5), ROM1.15 (I/O_{3}), U3I.14 (1Y3), U3J.17 (7D), U4A.2 (D5), U4C.4 (D5), U4E.4 (D5)
D6: P1.L (D6), ROM1.2 (I/O_{2}), U3I.12 (1Y4), U3J.18 (8D), U4A.1 (D6), U4C.3 (D6), U4E.3 (D6)
D7: P1.10 (+12), ROM1.3 (I/O_{1}), U3I.9 (2Y1), U3J.3 (1D), U4A.48 (D7), U4C.2 (D7), U4E.2 (D7)
D8: P1.8 (-5V), ROM2.17 (I/O_{4}), U3G.3 (2Y4), U3H.3 (1D), U4A.47 (D8), U4C.1 (D8), U4E.1 (D8)
D9: P1.J (D9), ROM2.15 (I/O_{3}), U3G.12 (1Y4), U3H.18 (8D), U4A.46 (D9), U4C.48 (D9), U4E.48 (D9)
D10: P1.F (D10), ROM2.2 (I/O_{2}), U3G.14 (1Y3), U3H.17 (7D), U4A.45 (D10), U4C.47 (D10), U4E.47 (D10)
D11: P1.6 (+5V), ROM2.3 (I/O_{1}), U3G.5 (2Y3), U3H.4 (2D), U4A.44 (D11), U4C.46 (D11), U4E.46 (D11)
D12: P1.4 (DGND), ROM2.17 (I/O_{4}), U3G.7 (2Y2), U3H.7 (3D), U4A.43 (D12), U4C.45 (D12), U4E.45 (D12)
D13: P1.D (D13), ROM2.15 (I/O_{3}), U3G.16 (1Y2), U3H.14 (6D), U4A.42 (D13), U4C.44 (D13), U4E.44 (D13)
D14: P1.B (D14), ROM2.2 (I/O_{2}), U3G.18 (1Y1), U3H.13 (5D), U4A.41 (D14), U4C.43 (D14), U4E.43 (D14)
D15: P1.2 (DGND), ROM2.3 (I/O_{1}), U3G.9 (2Y1), U3H.8 (4D), U4A.40 (D15), U4C.42 (D15), U4E.42 (D15)
DAC: FB41., R107.1, U2H.11 (Cp), U4H-.3 (C)
DIR: U6N.11 (PB1), U7N-.5
DIRB: J7.19 (DIRB), J10.18 (DIRB), U7N-.6
DKWE: U4E.39 (DKWE), U7P-.10
DMAL: U4C.13 (DMAL), U4E.12 (DMAL), U4J.1 (OEa), U4J.19 (OEb), U5L.15 (IO5), U5M.9 (I9)
DRA0: P1.Y (DRA0), ROM2.8 (A0)
DRA1: P1.X (DRA1), ROM2.7 (A1)
DRA2: P1.W (DRA2), ROM2.6 (A2)
DRA3: P1.V (DRA3), ROM2.14 (A3)
DRA4: P1.18 (XRDY), ROM2.13 (A4)
DRA5: P1.19 (~INT2), ROM2.12 (A5)
DRA6: P1.20 (~PALOPE), ROM2.11 (A6)
DRA7: P1.21 (A5), ROM2.10 (A7)
DTR: R31.1, U6K-.6
E: P1.50 (E), U6M-.12, U6N.25 (ɸ2), U6P.25 (ɸ2), U6S.20 (E)
EB: FB29., U6M-.11
EXP: P1.7 (EXP), P1.9 (EXP), P1.11 (EXP)
Earth: C1.1, C45.1, C46.2, C52.2, C53.2, C55.2, C56.2, C86.2, C87.2, C88.1, C89.1, C90.1, C91.1, C117.1, C118.2, DL1.3 (COMMUN), J3.16 (GND), J3.17 (GND), J3.18 (GND), J3.19 (GND), J3.20 (GND), Q8.3 (E), R32.1, R43.1, R47.1, R57.1, R59.1, R72.1, R74.1, R76.1, R78.1, R140.1, T1.3, U4A.37 (VSS), U5A.1 (1OE), U5A.10 (GND), U5A.19 (2OE), U6A.1 (1OE), U6A.10 (GND), U6A.19 (2OE), U7A.15 (GND)
FC0: P1.31 (FC_{0}), U6S.28 (FC_{0})
FC1: P1.33 (FC_{1}), U6S.27 (FC_{1})
FC2: P1.35 (FC_{2}), U6S.26 (FC_{2})
G: J3.4 (G_{∩}), R24.2
GND: C36.1, C40.1, C59.1, C60.1, C61.1, C62.1, C67.2, C68.2, C69.2, C70.2, C71.2, C72.2, C73.2, C74.2, C75.2, C76.2, C77.2, C78.2, C79.2, C80.1, C114.2, C116.1, C123.1, C124.1, C125.2, C126.2, C133.1, C133.2, C134.2, C135.2, C137,C138,C158,C159,C113,C115,C129,C130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.2, C139.1, C140.1, C142.2, C157.2, J3.13 (GNDRTN), J6.7 (GND), J7.3 (GND), J7.4 (GND), J7.5 (GND), J7.6 (GND), J7.7 (GND), J8.14 (GND), J8.15 (GND), J8.16 (GND), J8.17 (GND), J8.18 (GND), J8.19 (GND), J8.20 (GND), J8.21 (GND), J8.22 (GND), J10.1 (DGND), J10.3 (DGND), J10.5 (DGND), J10.7 (DGND), J10.9 (DGND), J10.11 (DGND), J10.13 (DGND), J10.15 (DGND), J10.17 (DGND), J10.19 (DGND), J10.21 (DGND), J10.23 (DGND), J10.25 (DGND), J10.27 (DGND), J10.29 (DGND), J10.31 (DGND), J10.33 (DGND), J13.2 (DGND), J13.3 (DGND), J14.3 (GND), J14.4 (GND), OSC1.2, P1.1 (DGND), P1.2 (DGND), P1.3 (DGND), P1.4 (DGND), P1.5 (+5V), P1.9 (EXP), P1.12 (~CONFIG), P1.13 (DGND), P1.17 (~OVR), P1.22 (~INT6), P1.24 (A4), P1.25 (DGND), P1.27 (A2), P1.37 (DGND), P1.49 (DGND), P1.61 (DGND), P1.73 (DGND), P1.85 (DGND), P1.A (DGND), P1.BB (DGND), P1.CC (DGND), P1.E (DGND), P1.EE (DGND), P1.K (DGND), P1.P (DGND), P1.U (DGND), P1.Z (DGND), R102.1, R103.1, R104.1, R104.2, RN5.7, RN5.8, ROM1.1 (~OE), ROM1.18 (GND), ROM2.1 (~OE), ROM2.18 (GND), U1H.3 (A2), U1H.5 (E2), U1I.3 (A2), U1I.5 (E2), U4C.27 (GND), U4C.41 (GND), U4E.8 (GND), U4M-.5 (+), U4M-.7 (+), U4M-.9 (+), U4M-.12 (V-), U6M-.5, U6M-.13, U6N.1 (GND), U6P.1 (GND), U6S.16 (GND), U6S.53 (GND), U7A.20 (N/P), U9G-.4, U9G-.5, W3.
GNDPWR: C2.2, C3.2, C4.2, C5.2, C6.2, C7.2, C8.2, C9.2, C10.2, C11.2, C12.2, C13.2, C14.2, C15.2, C16.2, C17.2, C18.2, C19.2, C20.2, C21.1, C22.1, C23.2, C24.2, C25.2, C26.2, C27.2, C28.2, C29.2, C30.2, C31.2, C32.2, C33.2, C34.2, C35.2, C36.2, C37.1, C38.1, C41.2, C42.2, C43.2, C44.2, C141.1, C162.2, C163.2, C164.2, C165.2, C166.2, C169.2, C170.2, C171.2, C172.2, C173.2, C174.2, C175.1, C176.1, C177.1, FB43., J1.2 (Ext), J2.2 (SGND), J2.5 (SGND), J4.2 (Ext), J5.2 (Ext), J6.1 (GND), J9.4 (SGND), J11.8 (SGND), J12.8 (SGND), J15., Q10.3 (E), R1.1, R3.1, R10.1, R12.1, R108.1
KCLK: FB20., R50.2, U4M-.6 (-), U6P.40 (CNT)
KDAT: FB21., R51.2, U6P.39 (SP)
LCEN: U1I.6 (E3), U5M.15 (IO5)
M0H: R137.1, U4A.9 (M0H)
M0V: R136.1, U4A.38 (M0V)
M1H: R139.1, U4A.8 (M1H)
M1V: R138.1, U4A.39 (M1V)
MA17: U1H.1 (A0), U1I.1 (A0), U1J.7 (Qb)
MA18: U1H.2 (A1), U1I.2 (A1), U1J.2 (Qa)
MCLK: R28.2
unnamed: C5.1, J5.1 (In), R1.2, R2.2
unnamed: C6.1, J4.1 (In), R3.2, R4.2
unnamed: C7.1, J6.16 (AUDIN), R6.2
unnamed: C8.1, J6.15 (AUDOUT), R5.2
unnamed: C9.1, J6.4 (RTS), R39.2
unnamed: C10.1, J6.3 (RXD), R30.2
unnamed: C11.1, J6.2 (TXD), R38.2
unnamed: C12.1, J6.6 (DSR), R41.2
unnamed: C13.1, FB30., J6.18 (~INT2)
unnamed: C14.1, J6.5 (CTS), R40.2
unnamed: C15.1, FB29., J6.17 (EB)
unnamed: C17.1, FB33., J6.25 (MRESB)
unnamed: C18.1, J6.8 (CD), R42.2
unnamed: C19.1, J6.20 (DTR), R31.2
unnamed: C20.1, FB39., J7.12 (+5V)
unnamed: C21.2, FB28., J7.23 (+12V)
unnamed: C23.1, FB17., J8.13 (SEL)
unnamed: C24.1, FB16., J8.12 (POUT)
unnamed: C25.1, FB15., J8.11 (BUSY)
unnamed: C26.1, FB14., J8.10 (~ACK)
unnamed: C27.1, FB13., J8.9 (D7)
unnamed: C28.1, FB12., J8.8 (D6)
unnamed: C29.1, FB11., J8.7 (D5)
unnamed: C30.1, FB10., J8.6 (D4)
unnamed: C31.1, FB9., J8.5 (D3)
unnamed: C32.1, FB8., J8.4 (D2)
unnamed: C33.1, FB7., J8.3 (D1)
unnamed: C34.1, FB6., J8.2 (D0)
unnamed: C35.1, FB5., J8.1 (~DRDY)
unnamed: C37.2, J2.8 (R.AUD), R13.1
unnamed: C38.2, J2.3 (L.AUD), R14.1
unnamed: C43.1, FB21., R7.2
unnamed: C44.1, FB20., R8.2
unnamed: C45.2, C47.1, R32.2, T1.1
unnamed: C46.1, FB36., T1.4, U7A.14 (V+)
unnamed: C47.2, U7A.10 (CHROMA_{in})
unnamed: C48.1, U7A.3 (R)
unnamed: C48.2, R74.2, R75.1
unnamed: C49.1, U7A.5 (B)
unnamed: C49.2, R78.2, R79.1
unnamed: C50.1, U7A.4 (G)
unnamed: C50.2, R59.2, R60.1
unnamed: C51.1, R37.2
unnamed: C51.2, L1.2
unnamed: C52.1, U7A.11 (B-Y_{clamp})
unnamed: C53.1, U7A.12 (R-Y_{clamp})
unnamed: C54.1, T1.5
unnamed: C54.2, R44.2
unnamed: C55.1, U7A.7 (V_{clamp})
unnamed: C56.1, R140.2, U7A.19 (ɸ_{m})
unnamed: C57.1, R47.2, R48.2
unnamed: C57.2, U7A.17 (OSC_{in})
unnamed: C63.1, R4.1, R13.2
unnamed: C63.2, C64.2
unnamed: C65.1, R2.1, R5.1, R14.2
unnamed: C65.2, C66.2
unnamed: C92.2, C97.2
unnamed: C96.1, R80.1, R83.1, U4E.30 (AUDR), U5G-.9 (-)
unnamed: C96.2, R83.2, R87.1, TP3.1, U5G-.8
unnamed: C100.1, R84.1, U4E.31 (AUDL), U5G-.13 (-)
unnamed: C100.2, R84.2, R90.1, TP2.1, U5G-.14
unnamed: C101.1, R91.2, R92.1
unnamed: C64.1, C101.2, C102.2, R81.2, U5G-.6 (-), U5G-.7
unnamed: C102.1, R88.1, R93.2
unnamed: C103.1, R88.2, U5G-.5 (+)
unnamed: C104.1, R89.2, U5G-.3 (+)
unnamed: C105.1, R89.1, R96.2
unnamed: C66.1, C105.2, C106.2, R82.2, U5G-.1, U5G-.2 (-)
unnamed: C106.1, R97.1, R98.2
unnamed: C107.1, R87.2, R91.1
unnamed: C108.1, R92.2, R93.1
unnamed: C109.1, R96.1, R97.2
unnamed: C110.1, R90.2, R98.1
unnamed: C134.1, CR2.2 (A), R105.1, TP1.1, U4M-.2, U4M-.10 (-)
unnamed: C135.1, R106.1, U4M-.1, U4M-.4 (-)
unnamed: C141.2, J15., R61.2, R62.2
unnamed: C143..C150.1, ROM2.9 (VCC)
unnamed: C162.1, J11.4 (RIGHT_{1}), R116.2
unnamed: C163.1, J11.3 (LEFT_{1}), R117.2
unnamed: C164.1, J11.2 (BACK_{1}), R118.2
unnamed: C165.1, J11.6 (~FIRE_{1}), R120.2
unnamed: C166.1, J11.1 (FWRD_{1}), R119.2
unnamed: C169.1, J12.4 (RIGHT_{0}), R123.2
unnamed: C170.1, J12.3 (LEFT_{0}), R124.2
unnamed: C171.1, J12.2 (BACK_{0}), R125.2
unnamed: C172.1, J12.6 (~FIRE_{0}), R127.2
unnamed: C173.1, J12.1 (FWRD_{0}), R126.2
unnamed: C176.2, J1.1 (In), R9.2
unnamed: C177.2, J2.4 (VIDEO), R11.2
unnamed: C178.1, R141.2
unnamed: D1.1 (K), J15.1
unnamed: D1.2 (A), J15.2
unnamed: DL1.1, R43.2, U7A.8 (-Y_{in})
unnamed: DL1.2, R45.2
unnamed: FB26., U8I-.2 (D), U8I-.9 (Q)
unnamed: FB40., J3.15 (~C1)
unnamed: FB41., U9I-.8
unnamed: J3.6 (I), R20.2
unnamed: J3.7 (R_{#}), R19.2
unnamed: J3.8 (G_{#}), R18.2
unnamed: J3.9 (B_{#}), R17.2
unnamed: J3.10 (~CS), R16.2
unnamed: J3.11 (~HS), R21.2, R142.2
unnamed: J3.12 (~VS), R22.2
unnamed: J3.14 (~ZD), R134.2
unnamed: J9.2 (KCLK), R8.1
unnamed: J9.3 (KDAT), R7.1
unnamed: J11.5 (POT_{1}X), R115.2
unnamed: J11.9 (POT_{1}Y), R114.2
unnamed: J12.5 (POT_{0}X), R122.2
unnamed: J12.9 (POT_{0}Y), R121.2
unnamed: L1.1, R48.1
unnamed: OSC1.3, U9G-.1
unnamed: Q1.1 (B), R64.2, R65.2, R66.2, R67.2, R72.2, R73.1
unnamed: Q1.3 (E), R25.1, R75.2
unnamed: Q2.1 (B), R53.2, R54.2, R55.2, R56.2, R57.2, R58.1
unnamed: Q2.3 (E), R24.1, R60.2
unnamed: Q3.1 (B), R68.2, R69.2, R70.2, R71.2, R76.2, R77.1
unnamed: Q3.3 (E), R23.1, R79.2
unnamed: Q4.1 (B), Q5.1 (B), U7A.9 (CV_{out})
unnamed: Q4.3 (E), R9.1, R10.2
unnamed: Q5.3 (E), R11.1, R12.2
unnamed: Q9.1 (E), R110.1, R113.2
unnamed: Q8.2 (C), Q10.1 (B), R33.1
unnamed: Q10.2 (C), R15.1, R16.1
unnamed: Q18.1 (B), R109.2, R113.1
unnamed: Q9.3 (B), Q18.2 (C), R108.2, R141.1
unnamed: R35.1, U7A.1 (T_{r})
unnamed: R35.2, R52.2, R63.1
unnamed: R44.1, U7A.13 (CHROMA_{out})
unnamed: R45.1, U7A.6 (-Y_{out})
unnamed: R61.1, U6K.8
unnamed: R100.1, R101.2, U4M-.8 (-), U4M-.13, U7P-.12, U7P-.13
unnamed: R101.1, R102.2, U4M-.11 (+)
unnamed: R112.1, U4H-.1 (~R)
unnamed: R116.1, RN4.7, U1M.5 (A2)
unnamed: R117.1, RN9.9, U1M.11 (A3)
unnamed: R118.1, RN9.6, U1M.6 (B2)
unnamed: R119.1, RN9.8, U1M.10 (B3)
unnamed: R123.1, RN9.5, U1M.14 (A4)
unnamed: R124.1, RN9.4, U1M.2 (A1)
unnamed: R125.1, RN9.3, U1M.13 (B4)
unnamed: R126.1, RN9.2, U1M.3 (B1)
unnamed: R128.1, U1I.15 (O0)
unnamed: R128.2, ROM1.16 (~CAS)
unnamed: R129.1, U1H.15 (O0)
unnamed: R129.2, ROM2.16 (~CAS)
unnamed: R132.1, U1I.14 (O1)
unnamed: R132.2, ROM1.16 (~CAS)
unnamed: R133.1, U1H.14 (O1)
unnamed: R133.2, ROM2.16 (~CAS)
unnamed: R136.2, U1M.4 (Y1)
unnamed: R137.2, U1M.12 (Y4)
unnamed: R138.2, U1M.9 (Y3)
unnamed: R139.2, U1M.7 (Y2)
unnamed: RN2-.3, U8G-.1 (~R), U8G-.12 (D), U8H-.1 (~R), U8H-.13 (~R), U8I-.1 (~R), U8I-.13 (~R)
unnamed: RN2-.4, U8G-.4 (~S), U8G-.10 (~S), U8H-.4 (~S), U8H-.10 (~S), U8I-.4 (~S), U8I-.10 (~S)
unnamed: RN3.9 (R8.2), ROM1.10 (A7)
unnamed: RN3.10 (R7.2), ROM1.8 (A0)
unnamed: RN3.11 (R6.2), ROM1.11 (A6)
unnamed: RN3.12 (R5.2), ROM1.7 (A1)
unnamed: RN3.13 (R4.2), ROM1.12 (A5)
unnamed: RN3.14 (R3.2), ROM1.6 (A2)
unnamed: RN3.15 (R2.2), ROM1.13 (A4)
unnamed: RN3.16 (R1.2), ROM1.14 (A3)
unnamed: ROM1.4 (~WE), ROM2.4 (~WE)
unnamed: ROM1.5 (~RAS), ROM2.5 (~RAS)
unnamed: ROM1.6 (A2), ROM2.6 (A2)
unnamed: ROM1.7 (A1), ROM2.7 (A1)
unnamed: ROM1.8 (A0), ROM2.8 (A0)
unnamed: ROM1.9 (VCC), ROM2.9 (VCC)
unnamed: ROM1.10 (A7), ROM2.10 (A7)
unnamed: ROM1.11 (A6), ROM2.11 (A6)
unnamed: ROM1.12 (A5), ROM2.12 (A5)
unnamed: ROM1.13 (A4), ROM2.13 (A4)
unnamed: ROM1.14 (A3), ROM2.14 (A3)
unnamed: U1J.4 (I1a), U4C.36 (DRA8), U4H-.2 (D)
unnamed: U1J.5 (I1b), U4H-.5 (Q)
unnamed: U2H.3 (D3), U4C.31 (DRA3)
unnamed: U2H.4 (D2), U4C.30 (DRA2)
unnamed: U2H.7 (D1), U4C.29 (DRA1)
unnamed: U2H.8 (D0), U4C.28 (DRA0)
unnamed: U2H.13 (D7), U4C.35 (DRA7)
unnamed: U2H.14 (D6), U4C.34 (DRA6)
unnamed: U2H.17 (D5), U4C.33 (DRA5)
unnamed: U2H.18 (D4), U4C.32 (DRA4)
unnamed: U4A.18 (~BURST), U6A.2 (1A0)
unnamed: U4A.20 (R0), U5A.4 (1A1)
unnamed: U4A.21 (R1), U5A.6 (1A2)
unnamed: U4A.22 (R2), U5A.2 (1A0)
unnamed: U4A.23 (R3), U5A.8 (1A3)
unnamed: U4A.24 (B0), U5A.17 (2A0)
unnamed: U4A.25 (B1), U5A.15 (2A1)
unnamed: U4A.26 (B2), U5A.13 (2A2)
unnamed: U4A.27 (B3), U5A.11 (2A3)
unnamed: U4A.28 (G0), U6A.17 (2A0)
unnamed: U4A.29 (G1), U6A.15 (2A1)
unnamed: U4A.30 (G2), U6A.13 (2A2)
unnamed: U4A.31 (G3), U6A.11 (2A3)
unnamed: U4A.33 (~ZD), U6A.4 (1A1)
unnamed: U4H-.9 (Q), U7P-.5
unnamed: U4H-.11 (C), U7M-.10
unnamed: U4H-.12 (D), U7M-.8, U7P-.2
unnamed: U5N.1 (?), U5P.1 (?)
unnamed: U5N.20 (~CE), U5P.20 (~CE), U7F-.13, W4., W5.
unnamed: U5N.26 (A14), U5P.26 (A14), W3.
unnamed: U5N.27 (A15), U5P.27 (A15), W1., W2.
unnamed: U6M-.3, U6P.23 (~CS)
unnamed: U6M-.8, U6N.23 (~CS)
unnamed: U7F-.12, W5.
unnamed: U7M-.2, U7M-.3, U7M-.5
unnamed: U7M-.4, U7N-.9
unnamed: U8G-.2 (D), U8G-.6 (~Q)
unnamed: U8G-.3 (C), U9G-.8
unnamed: U8G-.5 (Q), U8G-.11 (C), U8H-.3 (C), U8H-.11 (C), U8I-.11 (C)
unnamed: U8H-.2 (D), U8H-.9 (Q)
unnamed: U9G-.6, U9G-.10
OVL: U5L.6 (I6), U6P.2 (PA0)
P0: FB6., U6P.10 (PB0)
P0X: C120.2, R122.1, U4E.32 (POT_{0}X)
P0Y: C119.2, R121.1, U4E.33 (POT_{0}Y)
P1: FB7., U6P.11 (PB1)
P1X: C121.2, R115.1, U4E.35 (POT_{1}X)
P1Y: C122.2, R114.1, U4E.36 (POT_{1}Y)
P2: FB8., U6P.12 (PB2)
P3: FB9., U6P.13 (PB3)
P4: FB10., U6P.14 (PB4)
P5: FB11., U6P.15 (PB5)
P6: FB12., U6P.16 (PB6)
P7: FB13., U6P.17 (PB7)
PD0: P1.75 (PD0), U3I.11 (2A1), U3J.9 (4Q), U5P.11 (D0), U6P.33 (D0), U6S.5 (D0)
PD1: P1.77 (PD1), U3I.8 (1A4), U3J.12 (5Q), U5P.12 (D1), U6P.32 (D1), U6S.4 (D1)
PD2: U3I.6 (1A3), U3J.15 (6Q), U5P.13 (D2), U6P.31 (D2), U6S.3 (D2)
PD3: P1.81 (PD3), U3I.13 (2A2), U3J.6 (3Q), U5P.15 (D3), U6P.30 (D3), U6S.2 (D3)
PD4: P1.83 (PD4), U3I.15 (2A3), U3J.5 (2Q), U5P.16 (D4), U6P.29 (D4), U6S.1 (D4)
PD5: P1.86 (PD5), U3I.4 (1A2), U3J.16 (7Q), U5P.17 (D5), U6P.28 (D5), U6S.64 (D5)
PD6: P1.84 (PD6), U3I.2 (1A1), U3J.19 (8Q), U5P.18 (D6), U6P.27 (D6), U6S.63 (D6)
PD7: P1.82 (PD7), U3I.17 (2A4), U3J.2 (1Q), U5P.19 (D7), U6P.26 (D7), U6S.62 (D7)
PD8: P1.80 (PD8), U3G.17 (2A4), U3H.2 (1Q), U5N.11 (D0), U6N.33 (D0), U6S.61 (D8)
PD9: P1.78 (PD9), U3G.2 (1A1), U3H.19 (8Q), U5N.12 (D1), U6N.32 (D1), U6S.60 (D9)
PD10: P1.76 (PD10), U3G.4 (1A2), U3H.16 (7Q), U5N.13 (D2), U6N.31 (D2), U6S.59 (D10)
PD11: P1.71 (PD11), U3G.15 (2A3), U3H.5 (2Q), U5N.15 (D3), U6N.30 (D3), U6S.58 (D11)
PD12: P1.69 (PD12), U3G.13 (2A2), U3H.6 (3Q), U5N.16 (D4), U6N.29 (D4), U6S.57 (D12)
PD13: P1.67 (PD13), U3G.6 (1A3), U3H.15 (6Q), U5N.17 (D5), U6N.28 (D5), U6S.56 (D13)
PD14: P1.65 (PD14), U3G.8 (1A4), U3H.12 (5Q), U5N.18 (D6), U6N.27 (D6), U6S.55 (D14)
PD15: P1.63 (PD15), U3G.11 (2A1), U3H.9 (4Q), U5N.19 (D7), U6N.26 (D7), U6S.54 (D15)
POUT: FB16., U6N.3 (PA1), U6N.40 (CNT)
PU: R111.1, U1J.11 (I0c), U1J.12 (I1c), U1J.13 (I1d), U1J.14 (I0d), U4H-.4 (~S), U4H-.10 (~S)
R: J3.3 (R_{∩}), R25.2
RA0: RN3.7 (R7.1), U2H.9 (Q0), U2I.7 (Zb)
RA1: RN3.5 (R5.1), U2H.6 (Q1), U2J.7 (Zb)
RA2: RN3.3 (R3.1), U2H.5 (Q2), U2I.4 (Za)
RA3: RN3.1 (R1.1), U2H.2 (Q3), U2J.4 (Za)
RA4: RN3.2 (R2.1), U2H.19 (Q4), U2J.12 (Zc)
RA5: RN3.4 (R4.1), U2H.16 (Q5), U2I.12 (Zc)
RA6: RN3.6 (R6.1), U2H.15 (Q6), U2J.9 (Zd)
RA7: RN3.8 (R8.1), RN4.10, U2H.12 (Q7), U2I.9 (Zd)
RGA1: RN1.10, U4A.10 (RGA8), U4C.24 (RGA1), U4E.26 (RGA1), U4J.12 (O3a)
RGA2: RN1.9, U4A.11 (RGA7), U4C.23 (RGA2), U4E.25 (RGA2), U4J.9 (O0b)
RGA3: RN1.8, U4A.12 (RGA6), U4C.22 (RGA3), U4E.24 (RGA3), U4J.14 (O2a)
RGA4: RN1.7, U4A.13 (RGA5), U4C.21 (RGA4), U4E.23 (RGA4), U4J.7 (O1b)
RGA5: RN1.6, U4A.14 (RGA4), U4C.20 (RGA5), U4E.22 (RGA5), U4J.16 (O1a)
RGA6: RN1.5, U4A.15 (RGA3), U4C.19 (RGA6), U4E.21 (RGA6), U4J.5 (O2b)
RGA7: RN1.4, U4A.16 (RGA2), U4C.18 (RGA7), U4E.20 (RGA7), U4J.18 (O0a)
RGA8: RN1.3, U4A.17 (RGA1), U4C.17 (RGA8), U4E.19 (RGA8), U4J.3 (O3b)
RXD: R30.1, U4E.41 (RXD), U6L-.8, U6L-.10
SEL: FB17., U6N.4 (PA2)
TICK: FB4., U6P.19 (TOD)
TICKU: C67.1, C68.1, FB4., J14.7 (TICK_{U})
TXD: R38.1, U4E.40 (TXD), U6K-.11, U6K-.12, U6K-.13
UCEN: U1H.6 (E3), U5M.16 (IO4)
VREF: C94.2, C95.1, C99.1, R85.2, R86.2, U5G-.10 (+), U5G-.12 (+)
XN4: P1.DD (XN4), U1H.12 (O3)
XN5: P1.26 (A3), U1H.13 (O2)
XN6: P1.FF (XN6), U1I.12 (O3)
XN7: P1.28 (A7), U1I.13 (O2)
XRDY: P1.18 (XRDY), U5L.8 (I8)
~ACK: FB14., U6P.24 (~FLAG)
~ARW: U4C.16 (~ARW), U5M.1 (I1)
~AS: P1.74 (~AS), RN6-.5, U5L.4 (I4), U6S.6 (~AS)
~BBST: R52.1, U6A.18 (1Y0)
~BERR: P1.46 (~BERR), RN7-.3, RN7-.4, RN7-.5, U6S.22 (~BERR)
~BGACK: P1.62 (~BGACK), RN7-.9, U6S.12 (~BGACK)
~BG: P1.64 (~BG), U6S.11 (~BG)
~BHS: R134.1, U6A.16 (1Y1), U6N.19 (TOD)
~BLS: U4C.14 (~BLS), U5L.18 (IO2)
~BR: P1.60 (~BR), RN7-.8, U6S.13 (~BR)
~C1U: FB25., FB40., U8I-.8 (~Q), U9I-.2
~C1: FB25., P1.16 (~C1), U5L.11 (I10), U5M.13 (IO7)
~C2U: R28.1, U8H-.8 (~Q), U9I-.13
~C3U: FB24., U8G-.13 (~R), U8I-.6 (~Q), U9I-.5
~C3: FB24., P1.14 (~C3), U5L.9 (I9)
~C4U: R37.1, U8H-.6 (~Q), U8H-.12 (D), U8I-.12 (D), U9I-.10
~CDR: U3H.1 (~E), U3J.1 (~E), U5M.17 (I03)
~CDW: U3G.1 (1~G), U3G.19 (2~G), U3I.1 (1~G), U3I.19 (2~G), U5M.18 (IO2)
~CD: R42.1, U6L-.4, U6L-.6, U6N.7 (PA5)
~CHNG: J7.11 (~CHNG), J10.2 (~CHNG), RN5.10, U6P.4 (PA2)
~CSY: U4C.39 (~CSY), U6A.8 (1A3)
~CTS: R40.1, U6L-.11, U6L-.13, U6N.6 (PA4)
~C: Q8.1 (B), U6A.12 (1Y3), U7A.2 (~SYNC)
~DAE: U2H.1 (OE), U5L.14 (IO6), U5M.11 (I10)
~DBR: U4C.15 (~DBR)
~DKRD: J10.30 (~DKRD), RN5.3, U4E.37 (~DKRD)
~DKWDB: J10.22 (~DKWDB), U7N-.2
~DKWD: J7.17 (~DKWD), U4E.38 (~DKWD), U7N-.1
~DKWEB: J10.24 (~DKWEB), U7P-.8
~DKWE: J7.16 (~DKWE)
~DRDY: FB5., U6P.18 (~PC)
~DRESB: J7.10 (~DRESB), U7R-.6
~DSR: R41.1, U6L-.1, U6L-.3, U6N.5 (PA3)
~{DTACK: RN7-.10, U6S.10 (~DTACK)
~DTACK: P1.66 (~DTACK)
~DTR: U6K-.4, U6K-.5, U6N.9 (PA7)
~FIR0: R127.1, U4C.37 (~LP), U6P.8 (PA6)
~FIR1: R120.1, U6P.9 (PA7)
~HLT: P1.55 (~HLT), RN6-.8, U6S.17 (~HALT), U7P-.11
~HSY: R21.1, U4C.40 (~HSY), U6A.6 (1A2)
~INDEX: J7.22 (~INDEX), J10.8 (~INDEX), RN5.9, U6N.24 (~FLAG)
~INT2: FB30., P1.19 (~INT2), RN8-.7, U4E.16 (~INT2)
~INT3: U4C.12 (~INT3), U4E.17 (~INT3)
~INT6: P1.22 (~INT6), U4E.18 (~INT6)
~IPL0: P1.40 (~IPL_{0}), U4E.13 (~IPL0), U6S.25 (~IPL_{0})
~IPL1: P1.42 (~IPL_{1}), U4E.14 (~IPL1), U6S.24 (~IPL_{1})
~IPL2: P1.44 (~IPL_{2}), U4E.15 (~IPL2), U6S.23 (~IPL_{2})
~LDS: P1.70 (~LDS), RN6-.3, U5M.6 (I6), U6S.8 (~LDS)
~LED: U6K.9, U6K.10, U6P.3 (PA1)
~MCLK: J6.24 (~C2)
~MRESB: FB33., U7N-.12
~MTR0D: J10.4 (~MTR0D), J10.16 (~MTR0D), U7P-.6
~MTRXD: J7.8 (~MTRXD), U7P-.3
~MTR: U6N.17 (PB7), U7M-.9
~OBR: U5L.5 (I5)
~OVR: P1.17 (~OVR), U5L.7 (I7)
~PALOPE: P1.20 (~PALOPE), U5M.19 (IO1)
~PRWD: U6M-.6, U6N.22 (R/~W), U6P.22 (R/~W)
~PRW: P1.68 (~PRW), RN6.2, U5M.4 (I4), U6M-.4, U6S.9 (R/~W), W1.
~QTACK: U5L.17 (I03)
~RAS: FB27., P1.23 (A6), R130.1, R130.2, ROM1.5 (~RAS), U8G-.9 (Q)
~RDY: J7.1 (~RDY), J10.34 (~RDY), RN5.2, U6P.7 (PA5)
~RESB: R49.1, U4H-.13 (~R), U7N-.8, U7N-.13, U7P-.1, U7P-.4, U7R-.5
~RESET: C22.2, FB18., J8.25 (~RESET), U7M-.6
~RES: P1.53 (~RES), RN6-.7, U4C.11 (~RES), U4E.11 (~RES), U4M-.14, U6N.34 (~RES), U6P.34 (~RES), U6S.18 (~RESET), U7M-.1, U7P-.9
~RE: U1J.1 (S), U2I.15 (OE), U2J.15 (OE), U5L.16 (IO4), U5M.8 (I8)
~ROM01: U5M.12 (IO8), U5N.22 (~OE), U5P.22 (~OE)
~ROME: U5L.13 (IO7), U5M.7 (I7)
~RRW: P1.AA (~RRW), R131.1, R131.2, ROM1.4 (~WE), U5M.14 (IO6)
~RTS: R39.1, U6K-.2, U6K-.3, U6N.8 (PA6)
~SEL0B: J10.10 (~SEL0B), U7R-.4
~SEL0: U6N.13 (PB3), U7M-.11, U7R-.3
~SEL1B: J7.21 (~SEL1B), U7R-.2
~SEL1: U6N.14 (PB4), U7R-.1
~SEL2B: J7.9 (~SEL2B), U7R-.8
~SEL2: U6N.15 (PB5), U7R-.9
~SEL3B: J7.20 (~SEL3B), U7R-.10
~SEL3: U6N.16 (PB6), U7R-.11
~SIDEB: J7.13 (~SIDEB), J10.32 (~SIDEB), U7N-.10
~SIDE: U6N.12 (PB2), U7N-.11
~STEBB: J10.20 (~STEPB)
~STEPB: J7.18 (~STEPB), U7N-.4
~STEP: U6N.10 (PB0), U7N-.3
~TKO: J7.15 (~TKO), J10.26 (~TKO), RN5.5, U6P.6 (PA4)
~UDS: P1.72 (~UDS), RN6-.4, U5M.5 (I5), U6S.7 (~UDS)
~{VMA: RN6-.6, U6S.19 (~VMA)
~VMA: P1.51 (~VMA), U6M-.2, U6M-.10
~VPA: P1.48 (~VPA), U5L.12 (IO8), U6S.21 (~VPA)
~VSY: R22.1, U4C.38 (~VSY)
~WPRO: J7.14 (~WPRO), J10.28 (~WPRO), RN5.4, U6P.5 (PA3)
~XCLKEN: J3.2 (~XCLKEN), U9G-.2, U9G-.3, U9G-.13
~XCLK: J3.1 (~XCLK), R27.2, U9G-.9

Notes on the sheet:
RN4 470
EVEN
ODD
7407 x 7
RN1 1K
RN6
RN2
0.47 x4
C137,C138,C158,C159,C113,C115,C129, C130,C131,C132,C151,C152,C153,C154, C155,C156,C127,C128,C136,C111,C112, C81,C82,C83,C84,C85
470pF x13
U2P
RN8
POWER FERRITES (4)
RN7
RN5 1K
3.58MHz
U2N
