omega9380/Retro-Schematics/Apple/Apple II/Apple II - Clock Generator (all revisions).kicad_sch

## KiCad design Apple/Apple II/Apple II - Clock Generator (all revisions).kicad_sch (2022-12-21)

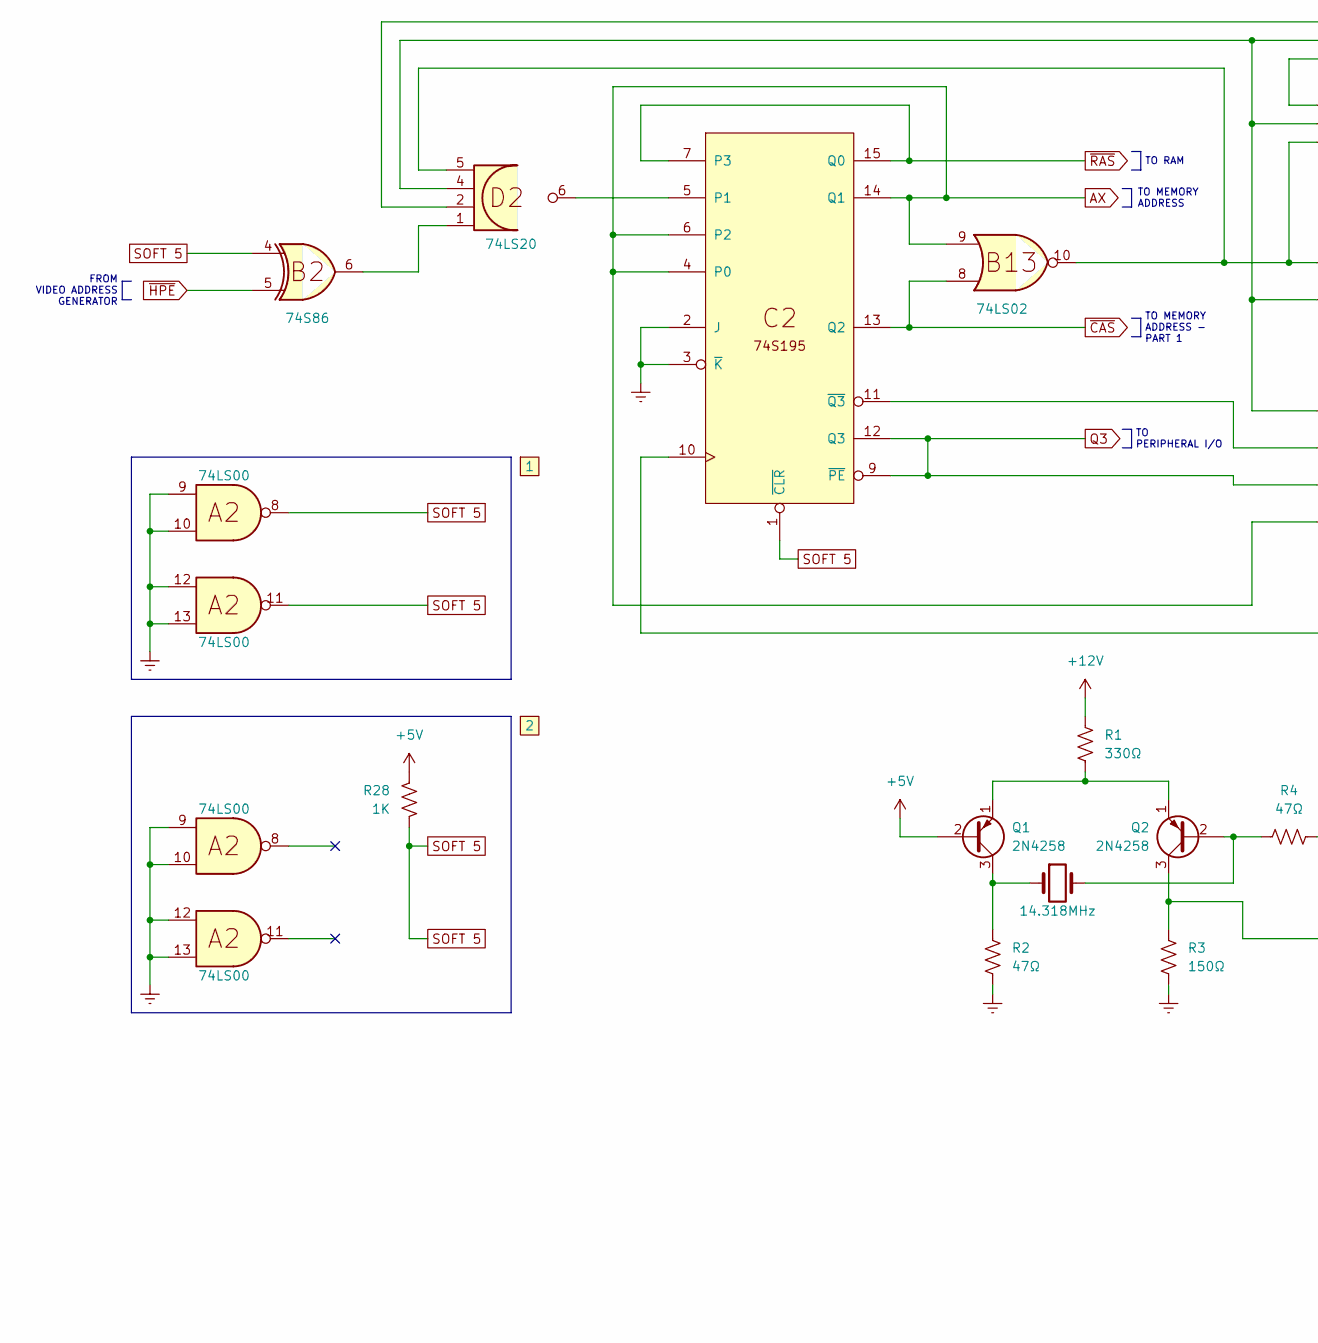
[picture p55: schematic Apple II - Clock Generator (all revisions).kicad_sch, part in row 1, column 1]

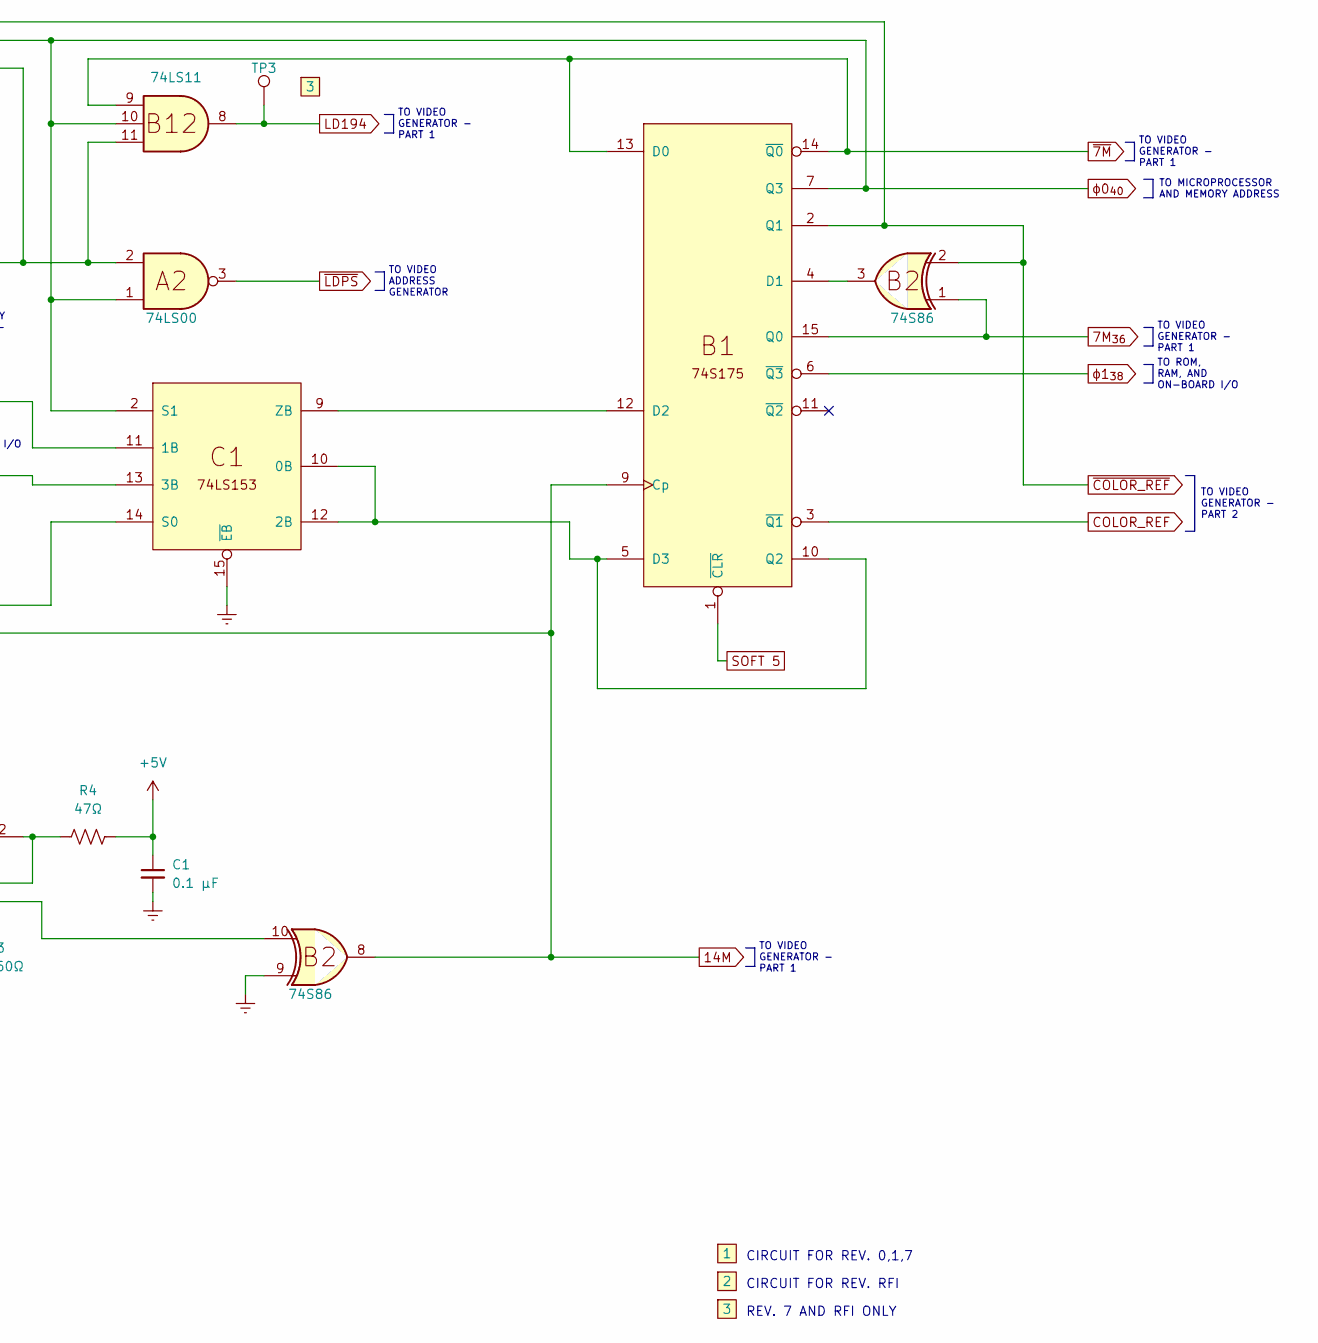
[picture p56: schematic Apple II - Clock Generator (all revisions).kicad_sch, part in row 1, column 2]

Parts:
A2: 74LS00
B1: B1_74S175
B2: 74S86
B12: 74LS11
B13: 74LS02
C1: C1_74LS153
C2: C2_74S195
D2: 74LS20
N1: 1
N2: 2
N3: 3
Q1, Q2: 2N4258; TO-92_Inline
R1: 330Ω
R2, R4: 47Ω
R3: 150Ω
R28: 1K
TP3: TestPoint
Y1: 14.318MHz

Connections:
7M_{36}: B1.15 (Q0), B2.1
14M: B1.9 (Cp), B2.8, C2.10
AX: B13.9, C1.14 (S0), C2.4 (P0), C2.6 (P2), C2.14 (Q1)
COLOR_REF: B1.3 (~Q1)
LD194: B12.8, TP3.1
unnamed: A2.2, B12.11, B13.10, D2.5
unnamed: A2.9, A2.10, A2.12, A2.13
unnamed: B1.4 (D1), B2.3
unnamed: B1.5 (D3), B1.10 (Q2), C1.10 (0B), C1.12 (2B)
unnamed: B1.12 (D2), C1.9 (ZB)
unnamed: B2.6, D2.1
unnamed: B2.10, Q2.3 (C), R3.1
unnamed: C1.1, R4.2
unnamed: C1.11 (1B), C2.11 (~Q3)
unnamed: C2.2 (J), C2.3 (~K)
unnamed: C2.5 (P1), D2.6
unnamed: Q1.1 (E), Q2.1 (E), R1.1
unnamed: Q1.3 (C), R2.1, Y1.1
unnamed: Q2.2 (B), R4.1, Y1.2
Q3: C1.13 (3B), C2.9 (~PE), C2.12 (Q3)
SOFT 5: A2.8, A2.11, B1.1 (~CLR), B2.4, C2.1 (~CLR), R28.1
~7M: B1.13 (D0), B1.14 (~Q0), B12.9
~CAS: B13.8, C2.13 (Q2)
~COLOR_REF: B1.2 (Q1), B2.2, D2.2
~HPE: B2.5
~LDPS: A2.3
~RAS: C2.7 (P3), C2.15 (Q0)
ɸ0_{40}: A2.1, B1.7 (Q3), B12.10, C1.2, D2.4
ɸ1_{38}: B1.6 (~Q3)

Notes on the sheet:
TO VIDEO GENERATOR - PART 1
TO RAM
TO MICROPROCESSOR AND MEMORY ADDRESS
FROM VIDEO ADDRESS GENERATOR
TO MEMORY ADDRESS - PART 1
TO VIDEO ADDRESS GENERATOR
TO PERIPHERAL I/O
TO ROM, RAM, AND ON-BOARD I/O
TO VIDEO GENERATOR - PART 2
REV. 7 AND RFI ONLY
CIRCUIT FOR REV. RFI
TO MEMORY ADDRESS
CIRCUIT FOR REV. 0,1,7
