omega9380/Retro-Schematics/Apple/Apple II/Apple II - Memory Address Pt 1 of 2 (Rev 0,1).kicad_sch

## KiCad design Apple/Apple II/Apple II - Memory Address Pt 1 of 2 (Rev 0,1).kicad_sch (2022-12-21)

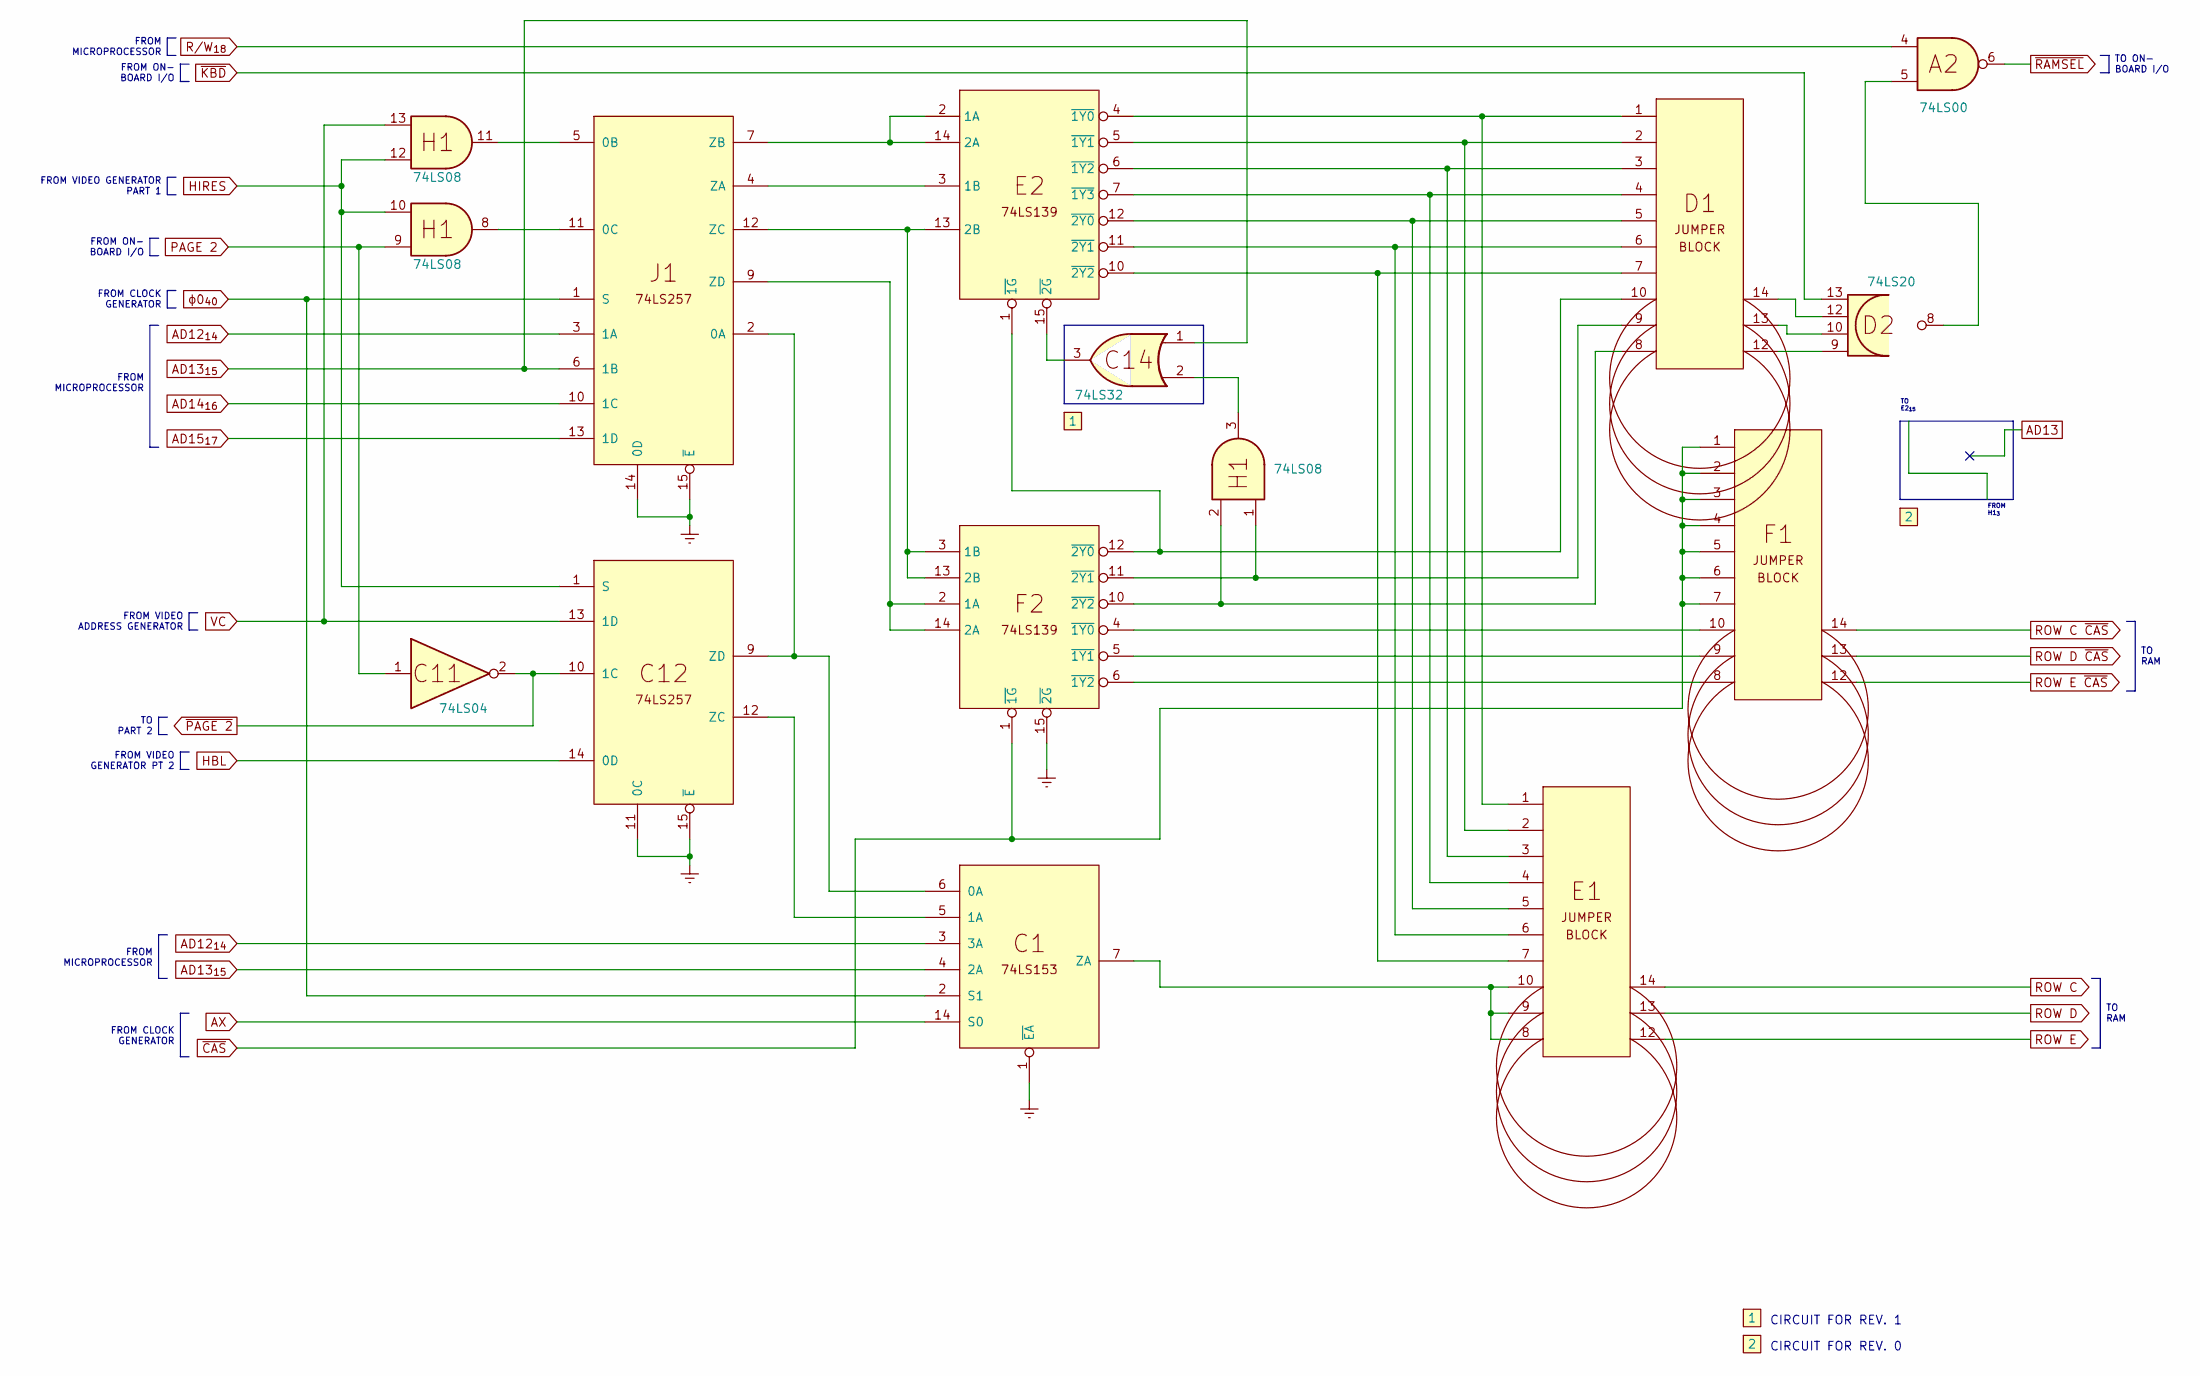
[picture p57: schematic Apple II - Memory Address Pt 1 of 2 (Rev 0,1).kicad_sch]

Parts:
A2: 74LS00
C11: 74LS04
C14: 74LS32
D2: 74LS20
H1: 74LS08
N1: 1
N2: 2

Connections:
AD13_{15}: C14.1
HIRES: H1.10, H1.12
unnamed: A2.5, D2.8
unnamed: C14.2, H1.3
PAGE 2: C11.1, H1.9
R/W_{18}: A2.4
VC: H1.13
~KBD: D2.13
~PAGE 2: C11.2
~RAMSEL: A2.6

Notes on the sheet:
FROM ON- BOARD I/O
TO RAM
FROM VIDEO GENERATOR PART 1
FROM MICROPROCESSOR
TO PART 2
FROM VIDEO GENERATOR PT 2
CIRCUIT FOR REV. 1
TO E2_{15}
FROM CLOCK GENERATOR
FROM H1_{3}
CIRCUIT FOR REV. 0
FROM VIDEO ADDRESS GENERATOR
TO ON- BOARD I/O
