omega9380/Retro-Schematics/Apple/Apple II/Apple II - Memory Address Pt 1 of 2 (Rev 7,RFI).kicad_sch

## KiCad design Apple/Apple II/Apple II - Memory Address Pt 1 of 2 (Rev 7,RFI).kicad_sch (2022-12-21)

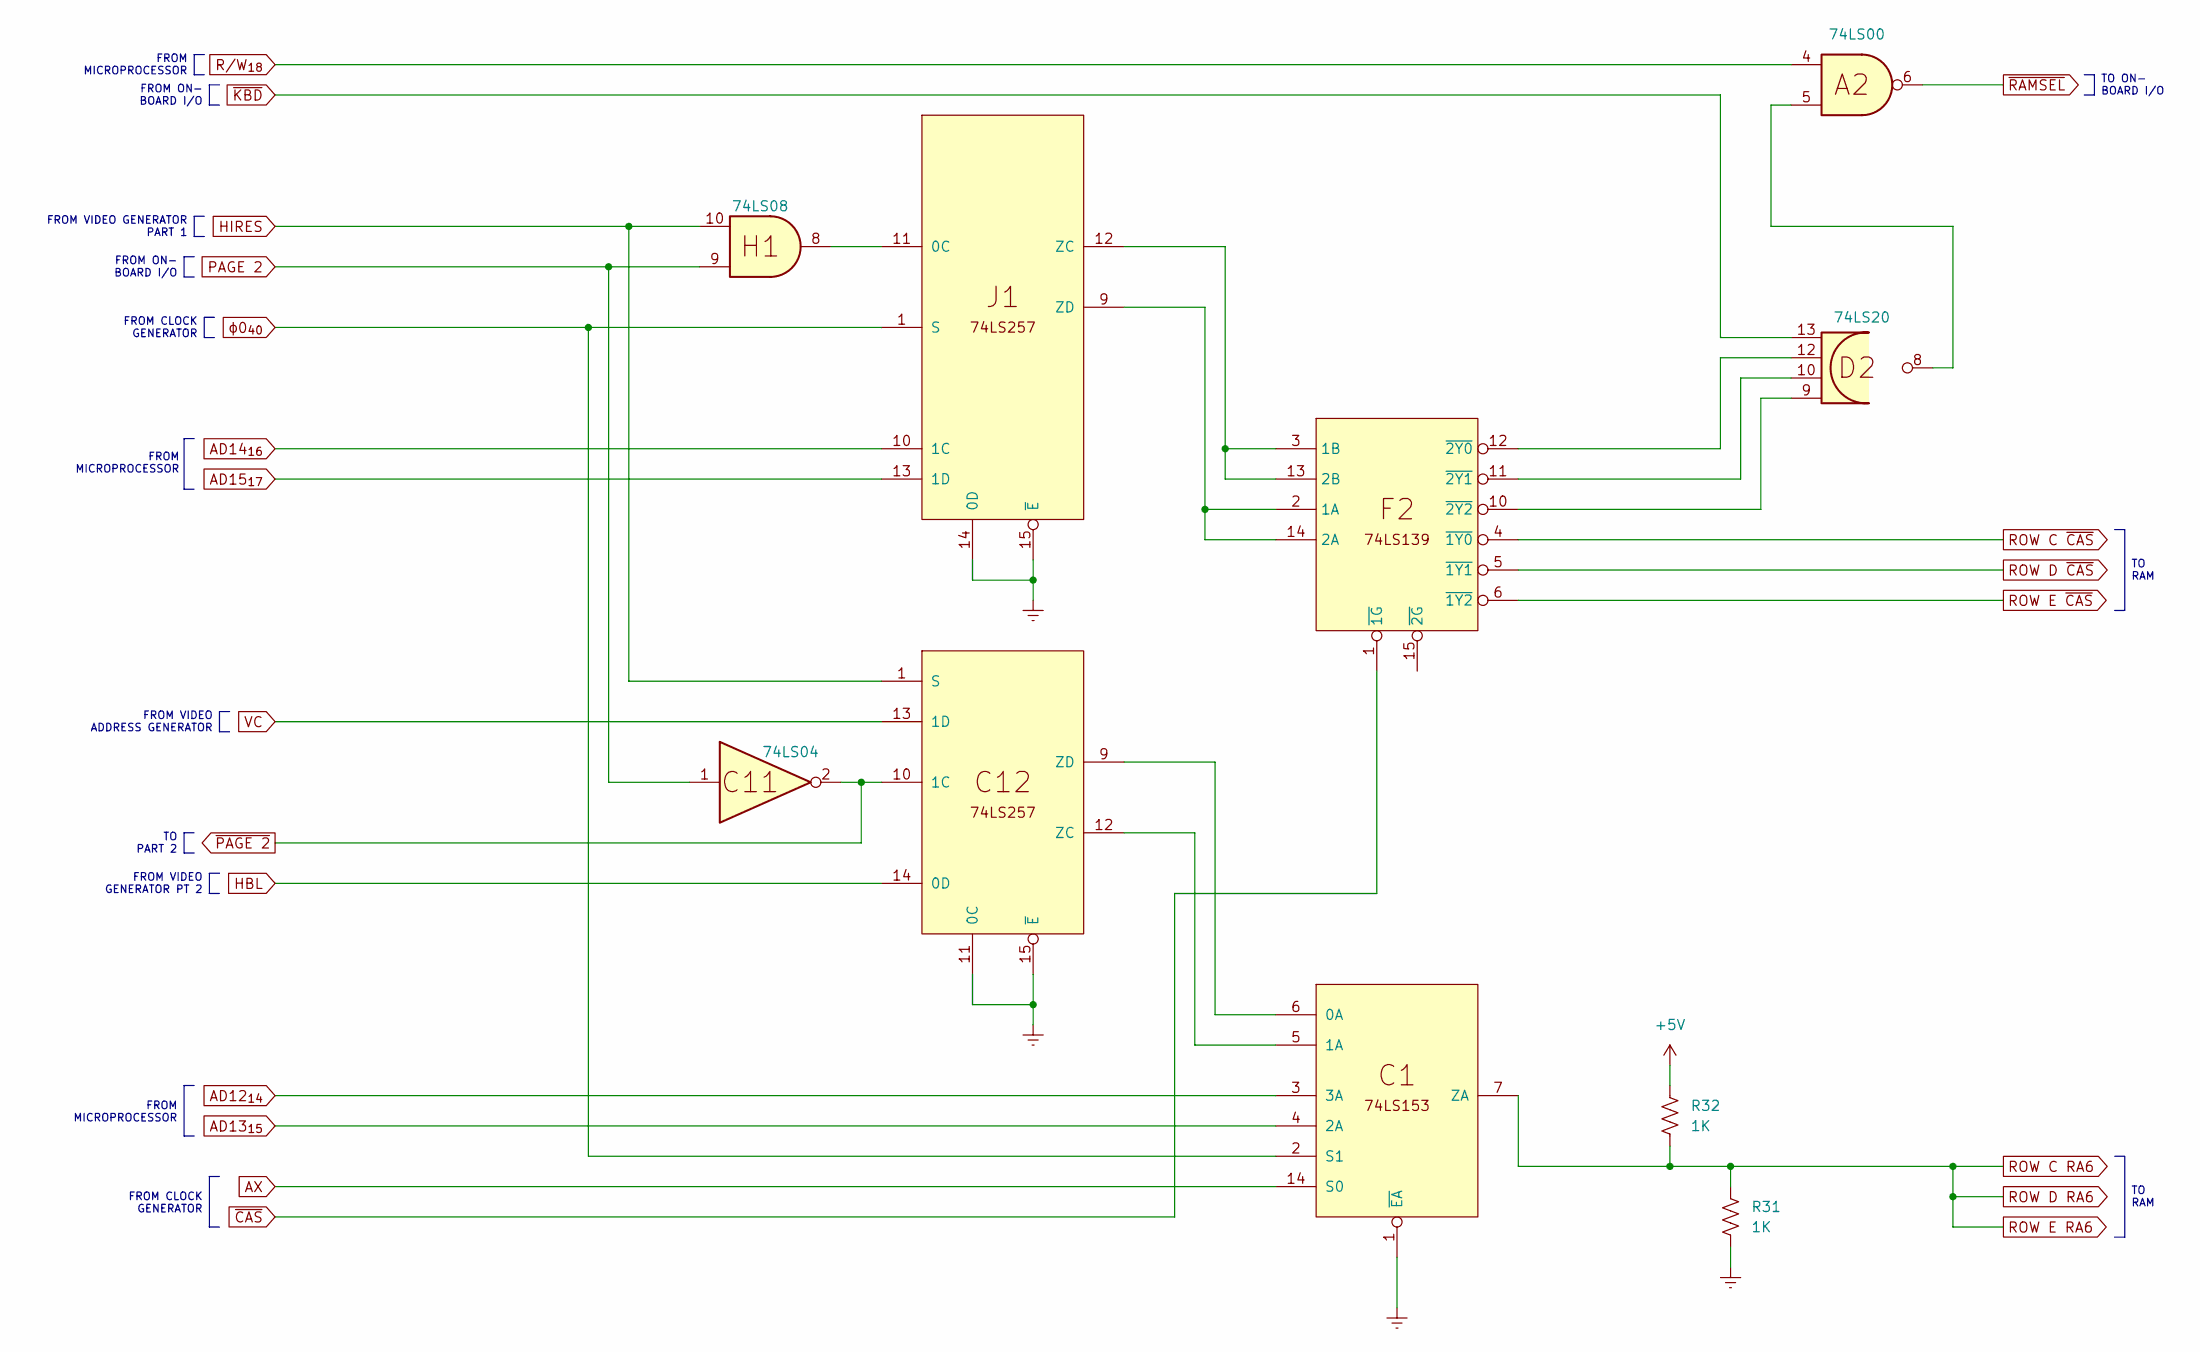
[picture p58: schematic Apple II - Memory Address Pt 1 of 2 (Rev 7,RFI).kicad_sch]

Parts:
A2: 74LS00
C11: 74LS04
D2: 74LS20
H1: 74LS08
R31, R32: 1K

Connections:
HIRES: H1.10
unnamed: A2.5, D2.8
PAGE 2: C11.1, H1.9
ROW C RA6: R31.1, R32.2
R/W_{18}: A2.4
~KBD: D2.13
~PAGE 2: C11.2
~RAMSEL: A2.6

Notes on the sheet:
FROM MICROPROCESSOR
FROM VIDEO ADDRESS GENERATOR
TO ON- BOARD I/O
FROM ON- BOARD I/O
TO RAM
FROM CLOCK GENERATOR
FROM VIDEO GENERATOR PART 1
TO PART 2
FROM VIDEO GENERATOR PT 2
