omega9380/Retro-Schematics/Apple/Apple II/Apple II - Memory Address Pt 2 of 2 (All Revisions).kicad_sch

## KiCad design Apple/Apple II/Apple II - Memory Address Pt 2 of 2 (All Revisions).kicad_sch (2022-12-21)

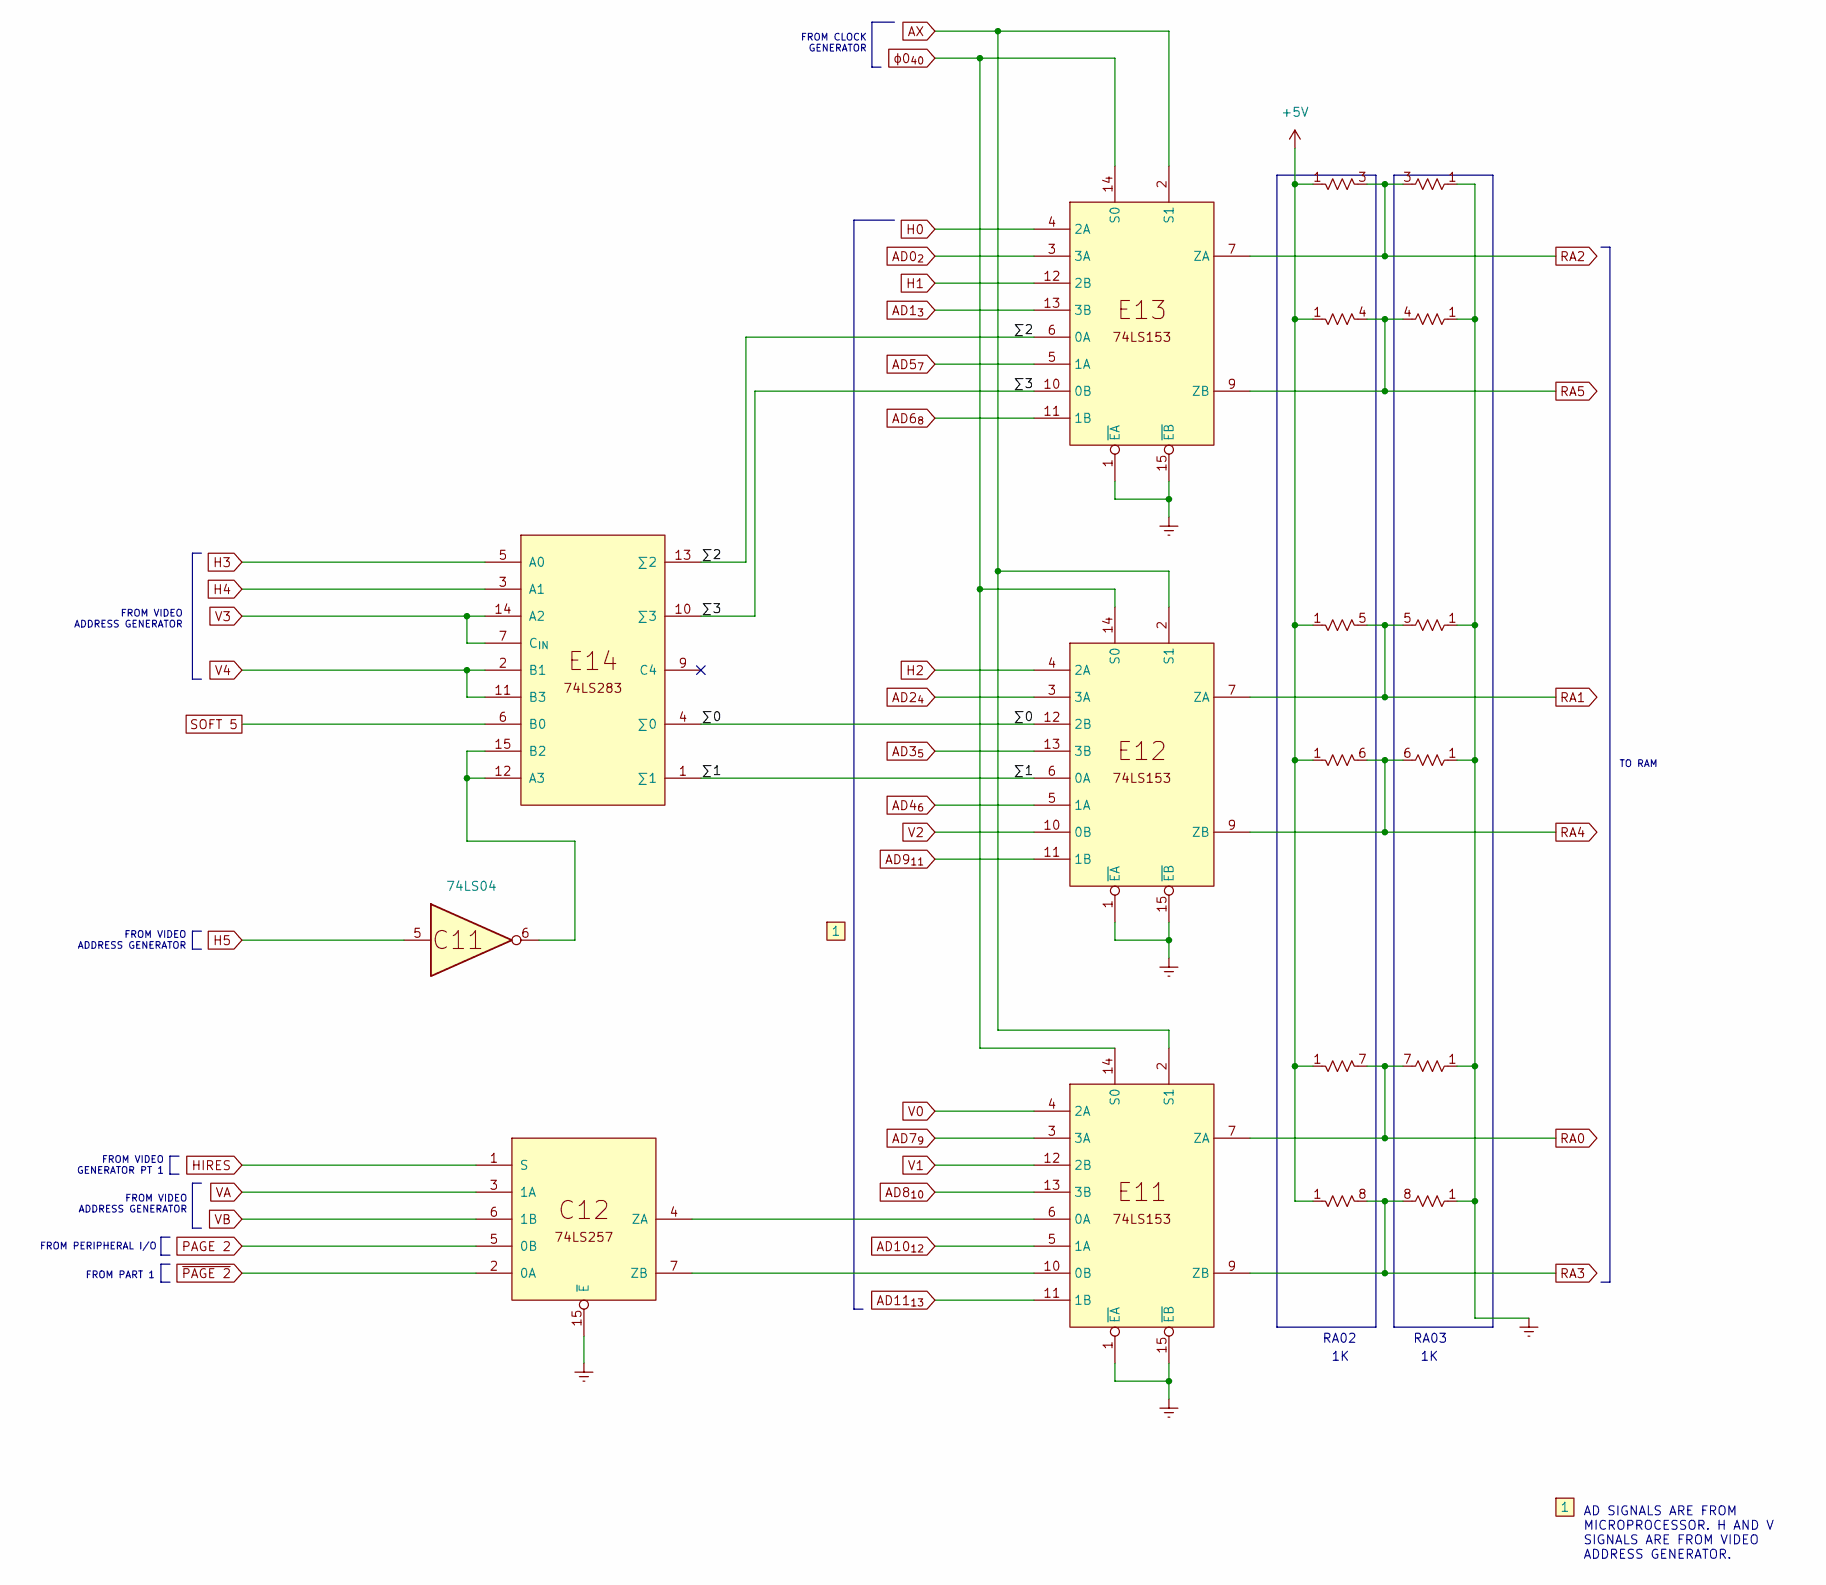
[picture p59: schematic Apple II - Memory Address Pt 2 of 2 (All Revisions).kicad_sch]

Parts:
C11: 74LS04
E12: E12_74LS153
E13: E13_74LS153
N1: 1
RA02, RA03: 1K; R_Array_SIP9

Connections:
AD0_{2}: E13.3 (3A)
AD1_{3}: E13.13 (3B)
AD2_{4}: E12.3 (3A)
AD3_{5}: E12.13 (3B)
AD4_{6}: E12.5 (1A)
AD5_{7}: E13.5 (1A)
AD6_{8}: E13.11 (1B)
AD9_{11}: E12.11 (1B)
AX: E12.2 (S1), E13.2 (S1)
H0: E13.4 (2A)
H1: E13.12 (2B)
H2: E12.4 (2A)
H5: C11.5
unnamed: E12.1 (~EA), E12.15 (~EB)
unnamed: E13.1 (~EA), E13.15 (~EB)
RA0: RA02.7 (R6.2), RA03.7 (R6.2)
RA1: E12.7 (ZA), RA02.5 (R4.2), RA03.5 (R4.2)
RA2: E13.7 (ZA), RA02.3 (R2.2), RA03.3 (R2.2)
RA3: RA02.8 (R7.2), RA03.8 (R7.2)
RA4: E12.9 (ZB), RA02.6 (R5.2), RA03.6 (R5.2)
RA5: E13.9 (ZB), RA02.4 (R3.2), RA03.4 (R3.2)
V2: E12.10 (0B)
ɸ0_{40}: E12.14 (S0), E13.14 (S0)
∑0: E12.12 (2B)
∑1: E12.6 (0A)
∑2: E13.6 (0A)
∑3: E13.10 (0B)

Notes on the sheet:
FROM VIDEO ADDRESS GENERATOR
FROM PERIPHERAL I/O
FROM CLOCK GENERATOR
TO RAM
RA02
RA03
FROM PART 1
AD SIGNALS ARE FROM MICROPROCESSOR. H AND V SIGNALS ARE FROM VIDEO ADDRESS GENERATOR.
FROM VIDEO GENERATOR PT 1
