omega9380/Retro-Schematics/Apple/Apple II/Apple II - Microprocessor (Rev 0,1,7).kicad_sch

## KiCad design Apple/Apple II/Apple II - Microprocessor (Rev 0,1,7).kicad_sch (2022-12-21)

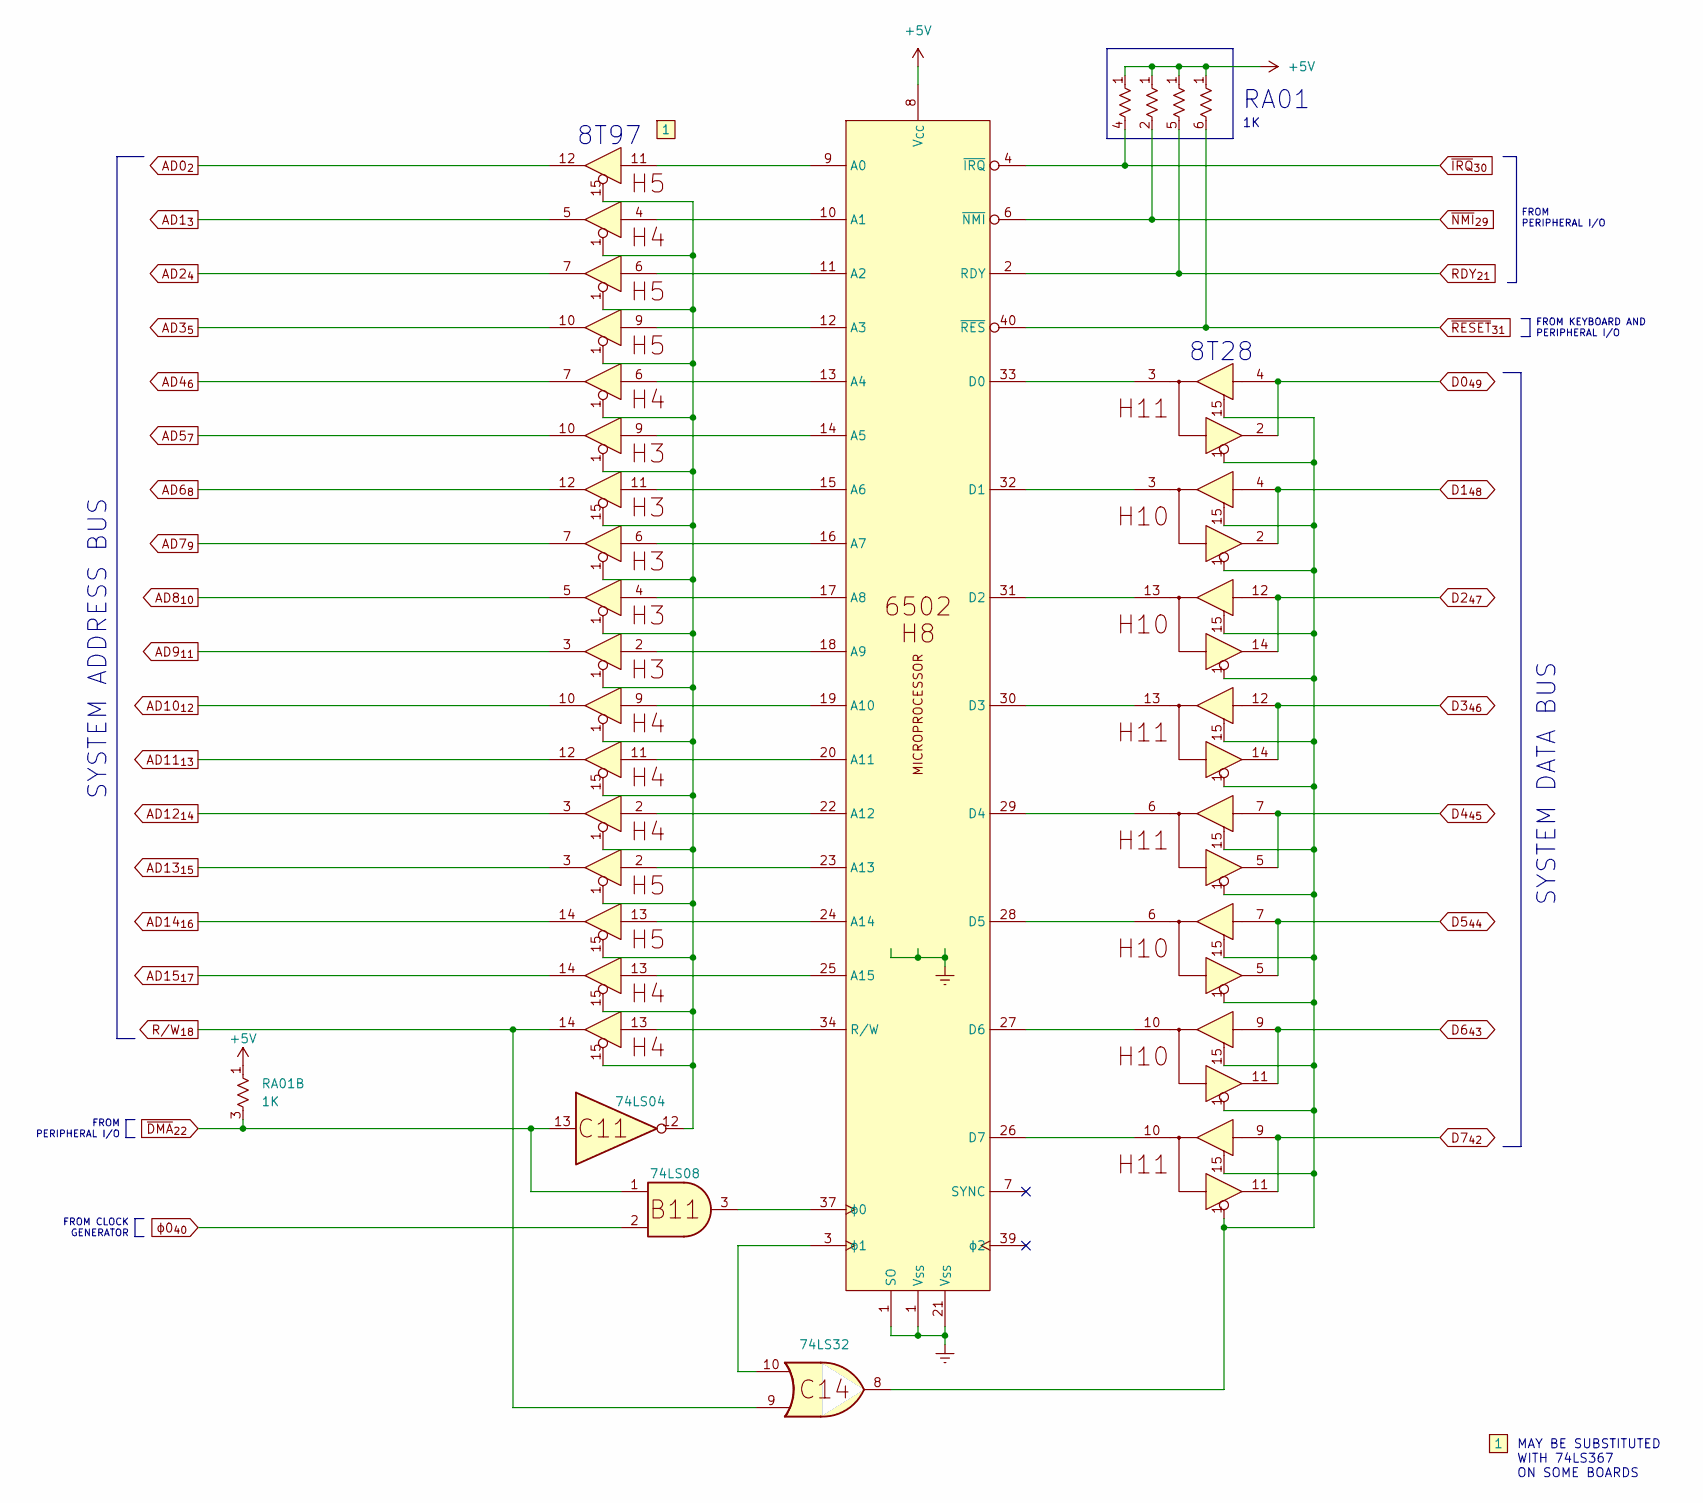
[picture p60: schematic Apple II - Microprocessor (Rev 0,1,7).kicad_sch]

Parts:
B11: 74LS08
C11: 74LS04
C14: 74LS32
N1: 1
RA01: 1K; R_Array_SIP9

Connections:
RDY_{21}: RA01.5 (R4.2)
R/W_{18}: C14.9
~DMA_{22}: B11.1, C11.13, RA01.3 (R2.2)
~IRQ_{30}: RA01.4 (R3.2)
~NMI_{29}: RA01.2 (R1.2)
~RESET_{31}: RA01.6 (R5.2)
ɸ0_{40}: B11.2

Notes on the sheet:
FROM PERIPHERAL I/O
RA01
8T97
SYSTEM DATA BUS
FROM KEYBOARD AND PERIPHERAL I/O
SYSTEM ADDRESS BUS
MAY BE SUBSTITUTED WITH 74LS367 ON SOME BOARDS
FROM CLOCK GENERATOR
8T28
