omega9380/Retro-Schematics/Apple/Apple II/Apple II - On-board IO Pt 1 of 2 (All Revisions).kicad_sch

## KiCad design Apple/Apple II/Apple II - On-board IO Pt 1 of 2 (All Revisions).kicad_sch (2022-12-21)

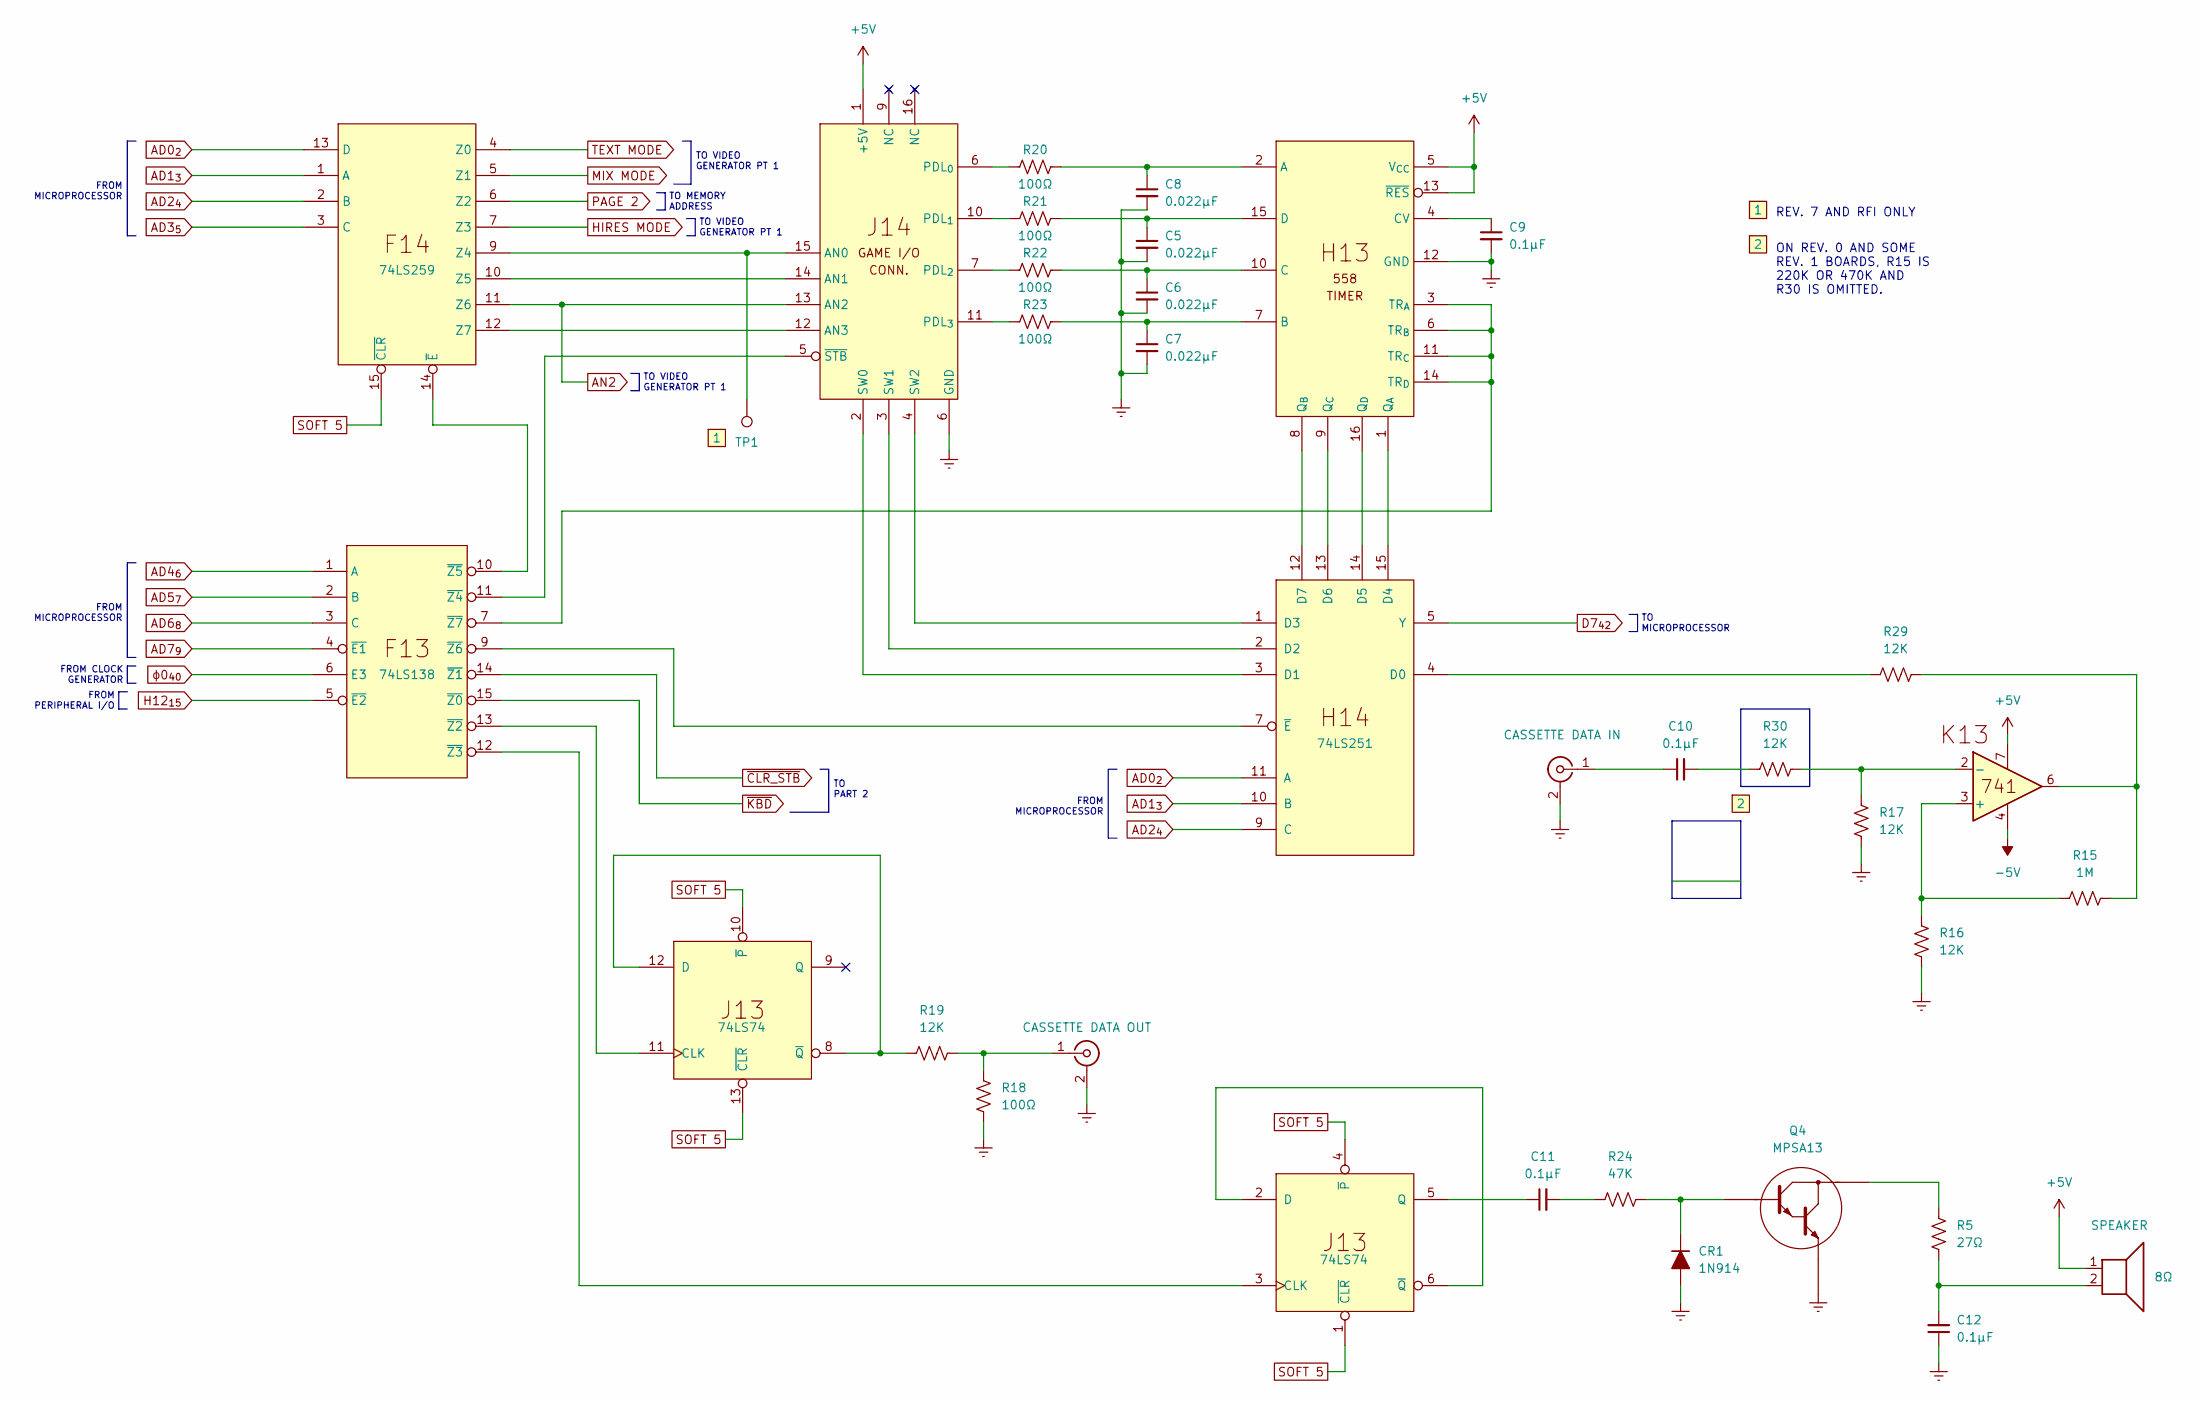
[picture p61: schematic Apple II - On-board IO Pt 1 of 2 (All Revisions).kicad_sch]

Parts:
C5, C6, C7, C8: 0.022µF
C9, C10, C11, C12: 0.1µF
CR1: 1N914
F13: 74LS138
F14: 74LS259
H14: 74LS251
J13: 74LS74
J45: CASSETTE DATA OUT
J98: CASSETTE DATA IN
N1: 1
N2: 2
Q4: MPSA13
R5: 27Ω
R15: 1M
R16, R17, R19, R29, R30: 12K
R18, R20, R21, R22, R23: 100Ω
R24: 47K
SPEAKER: 8Ω
TP1: TestPoint

Connections:
AD0_{2}: F14.13 (D), H14.11 (A)
AD1_{3}: F14.1 (A), H14.10 (B)
AD2_{4}: F14.2 (B), H14.9 (C)
AD3_{5}: F14.3 (C)
AD4_{6}: F13.1 (A)
AD5_{7}: F13.2 (B)
AD6_{8}: F13.3 (C)
AD7_{9}: F13.4 (~E1)
AN2: F14.11 (Z6)
D7_{42}: H14.5 (Y)
H12_{15}: F13.5 (~E2)
HIRES MODE: F14.7 (Z3)
MIX MODE: F14.5 (Z1)
unnamed: C5.1, R21.2
unnamed: C5.2, C6.2, C7.2, C8.2
unnamed: C6.1, R22.2
unnamed: C7.1, R23.2
unnamed: C8.1, R20.2
unnamed: C10.1, J98.1 (In)
unnamed: C10.2, R30.2
unnamed: C11.1, J13.5 (Q)
unnamed: C11.2, R24.1
unnamed: C12.2, R5.2, SPEAKER.2
unnamed: CR1.1 (K), Q4., R24.2
unnamed: F13.9 (~Z6), H14.7 (~E)
unnamed: F13.10 (~Z5), F14.14 (~E)
unnamed: F13.12 (~Z3), J13.3 (CLK)
unnamed: F13.13 (~Z2), J13.11 (CLK)
unnamed: F14.9 (Z4), TP1.1
unnamed: H14.4 (D0), R29.1
unnamed: J13.2 (D), J13.6 (~Q)
unnamed: J13.8 (~Q), J13.12 (D), R19.1
unnamed: J45.1 (In), R18.2, R19.2
unnamed: Q4., R5.1
unnamed: R15.1, R16.2
unnamed: R15.2, R29.2
unnamed: R17.1, R30.1
PAGE 2: F14.6 (Z2)
SOFT 5: F14.15 (~CLR), J13.1 (~CLR), J13.4 (~P), J13.10 (~P), J13.13 (~CLR)
TEXT MODE: F14.4 (Z0)
~CLR_STB: F13.14 (~Z1)
~KBD: F13.15 (~Z0)
ɸ0_{40}: F13.6 (E3)

Notes on the sheet:
TO PART 2
TO VIDEO GENERATOR PT 1
REV. 7 AND RFI ONLY
FROM MICROPROCESSOR
TO MICROPROCESSOR
FROM PERIPHERAL I/O
TO MEMORY ADDRESS
ON REV. 0 AND SOME REV. 1 BOARDS, R15 IS 220K OR 470K AND R30 IS OMITTED.
FROM CLOCK GENERATOR
