omega9380/Retro-Schematics/Apple/Apple II/Apple II - On-board IO Pt 2 of 2 (All Revisions).kicad_sch

## KiCad design Apple/Apple II/Apple II - On-board IO Pt 2 of 2 (All Revisions).kicad_sch (2022-12-21)

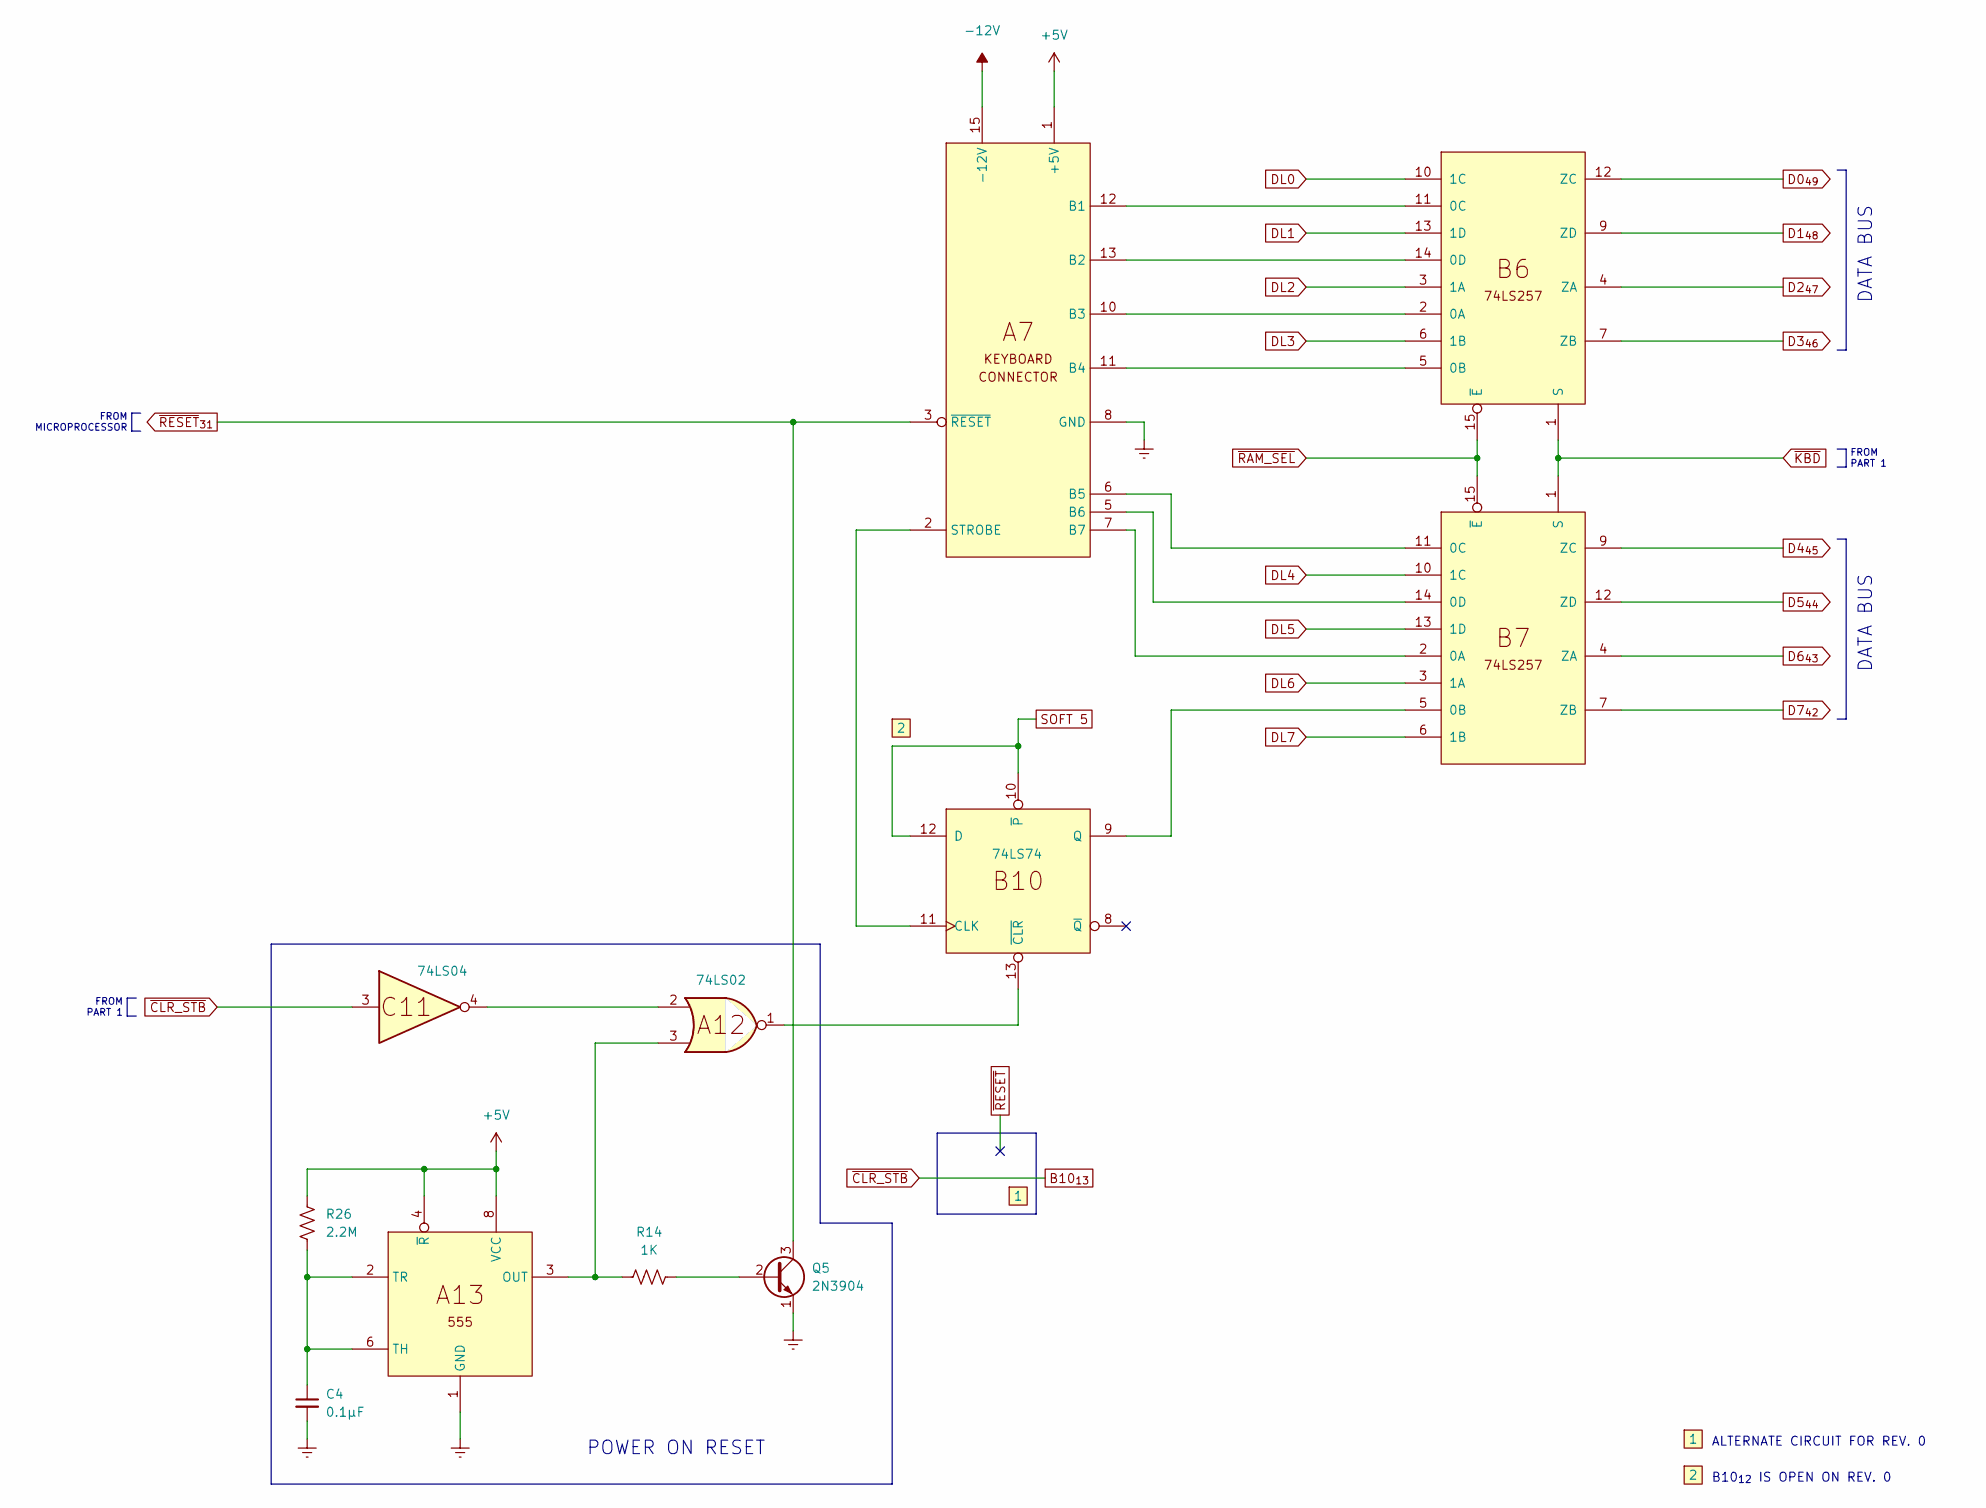
[picture p62: schematic Apple II - On-board IO Pt 2 of 2 (All Revisions).kicad_sch]

Parts:
A12: 74LS02
B10: 74LS74
C4: 0.1µF
C11: 74LS04
N1: 1
N2: 2
Q5: 2N3904; TO-92_Inline
R14: 1K
R26: 2.2M

Connections:
B10_{13}: C11.3
unnamed: A12.1, B10.13 (~CLR)
unnamed: A12.2, C11.4
unnamed: A12.3, R14.1
unnamed: C4.1, R26.1
unnamed: Q5.2 (B), R14.2
SOFT 5: B10.10 (~P), B10.12 (D)
~RESET_{31}: Q5.3 (C)

Notes on the sheet:
FROM MICROPROCESSOR
DATA BUS
B10_{12} IS OPEN ON REV. 0
ALTERNATE CIRCUIT FOR REV. 0
POWER ON RESET
FROM PART 1
