omega9380/Retro-Schematics/Apple/Apple II/Apple II - Peripheral IO (All Revisions).kicad_sch

## KiCad design Apple/Apple II/Apple II - Peripheral IO (All Revisions).kicad_sch (2022-07-14)

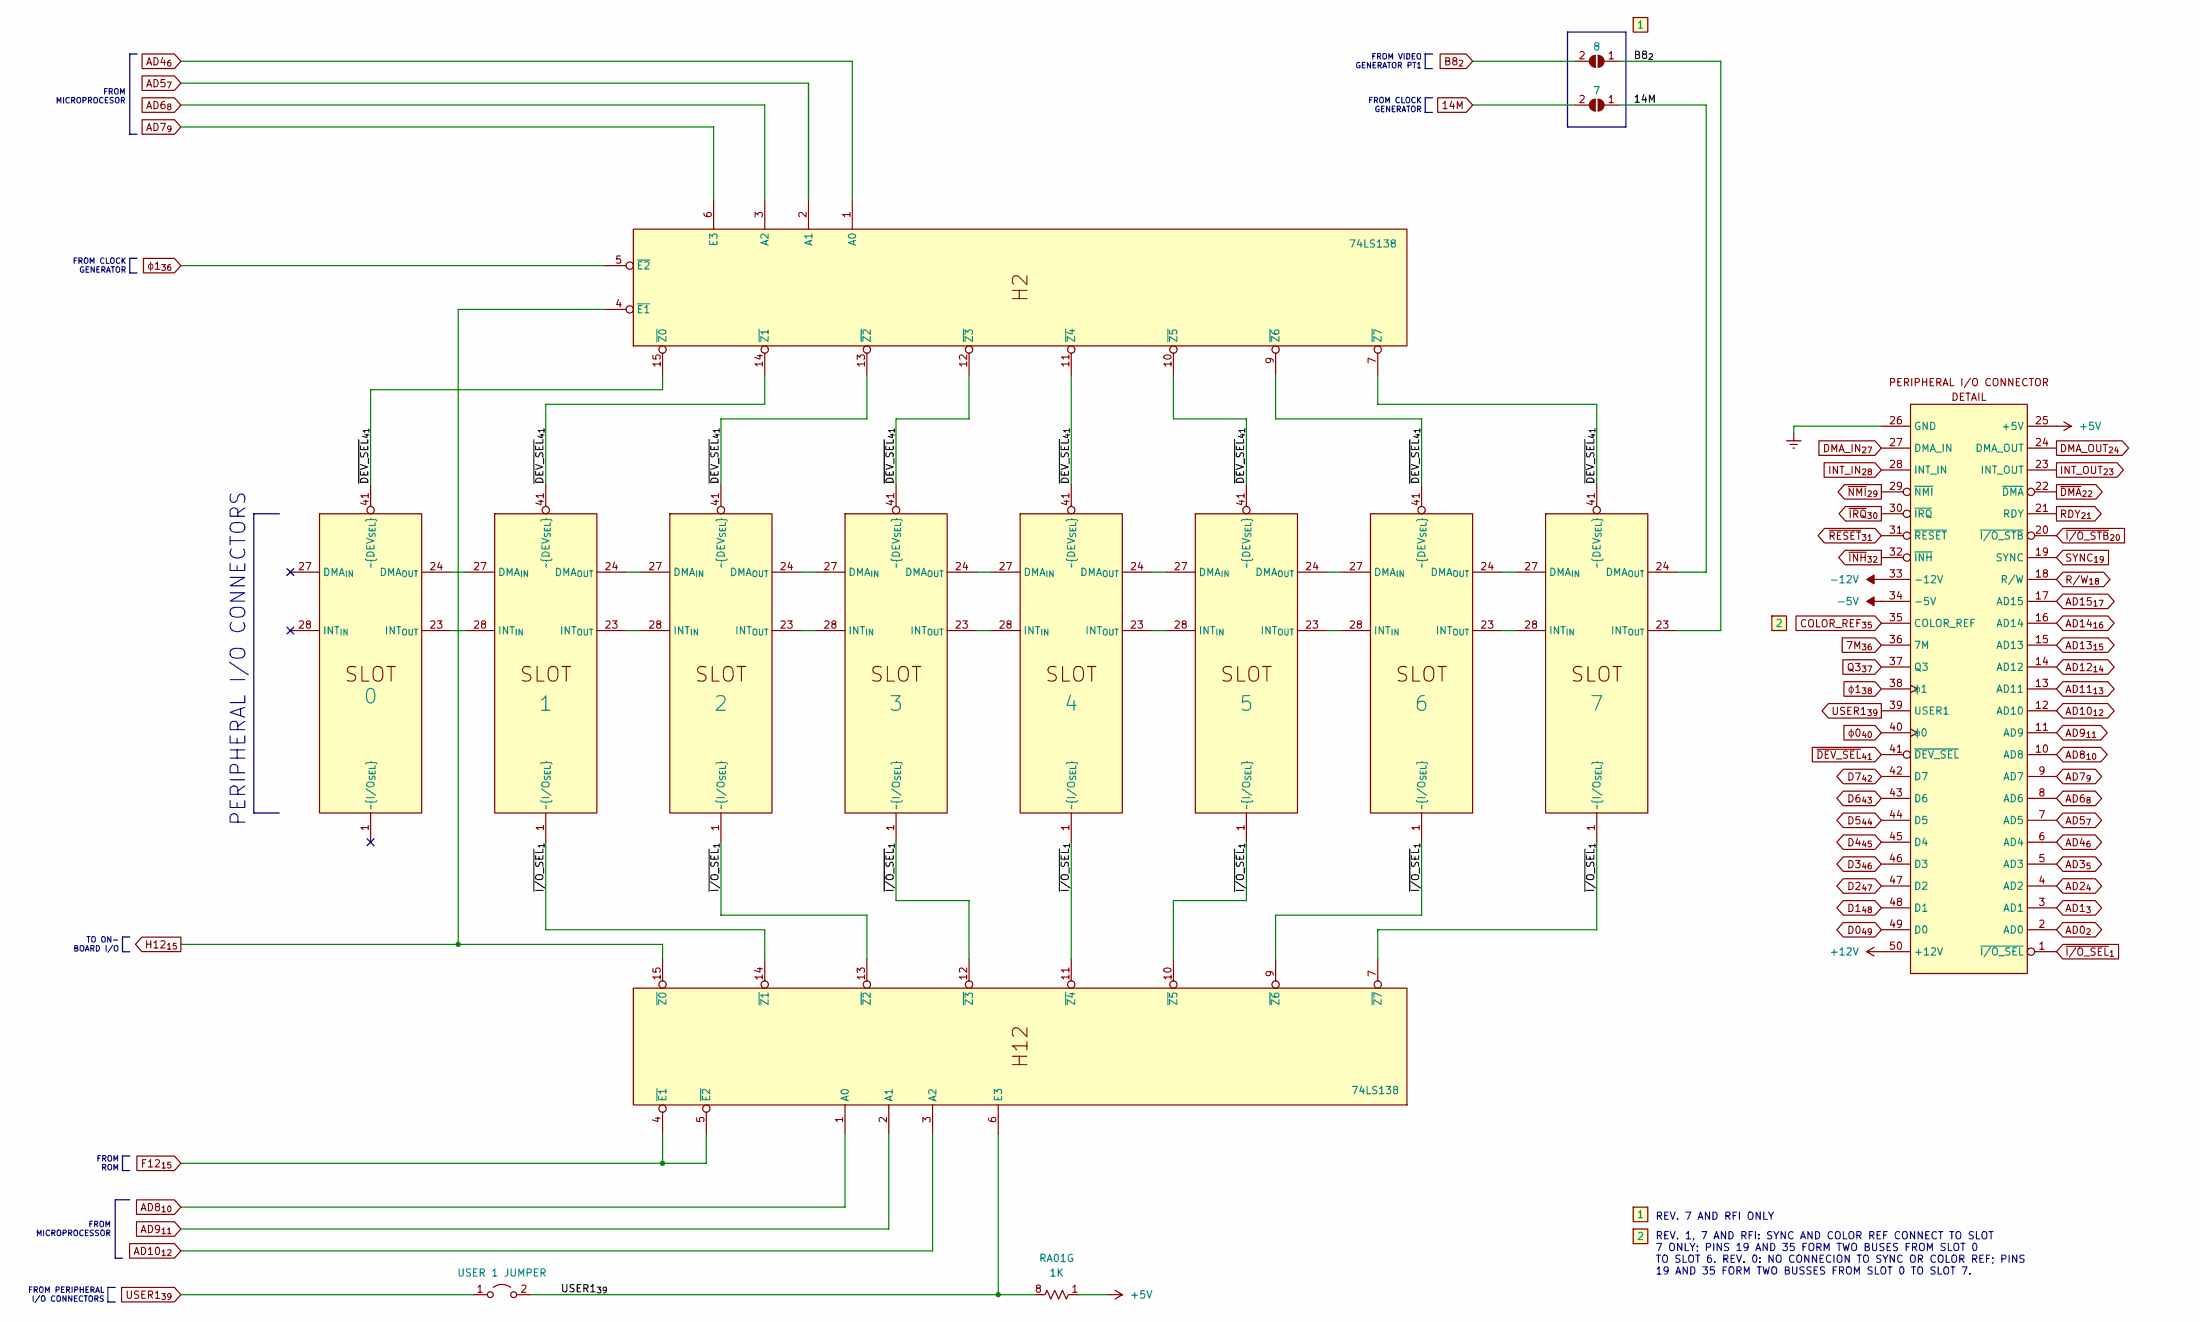
[picture p63: schematic Apple II - Peripheral IO (All Revisions).kicad_sch]

Parts:
H2, H12: 74LS138
JP7: 7
JP8: 8
JP10: USER 1 JUMPER
N1: 1
N2: 2
RA01: 1K; R_Array_SIP9
S0: 0
S1: 1
S2: 2
S3: 3
S4: 4
S5: 5
S6: 6
S7: 7

Connections:
14M: JP7.1 (A), JP7.2 (B), S7.24 (DMA_{OUT})
AD4_{6}: H2.1 (A0)
AD5_{7}: H2.2 (A1)
AD6_{8}: H2.3 (A2)
AD7_{9}: H2.6 (E3)
AD8_{10}: H12.1 (A0)
AD9_{11}: H12.2 (A1)
AD10_{12}: H12.3 (A2)
B8_{2}: JP8.1 (A), JP8.2 (B), S7.23 (INT_{OUT})
F12_{15}: H12.4 (~E1), H12.5 (~E2)
H12_{15}: H2.4 (~E1), H12.15 (~Z0)
unnamed: S0.23 (INT_{OUT}), S1.28 (INT_{IN})
unnamed: S0.24 (DMA_{OUT}), S1.27 (DMA_{IN})
unnamed: S1.23 (INT_{OUT}), S2.28 (INT_{IN})
unnamed: S1.24 (DMA_{OUT}), S2.27 (DMA_{IN})
unnamed: S2.23 (INT_{OUT}), S3.28 (INT_{IN})
unnamed: S2.24 (DMA_{OUT}), S3.27 (DMA_{IN})
unnamed: S3.23 (INT_{OUT}), S4.28 (INT_{IN})
unnamed: S3.24 (DMA_{OUT}), S4.27 (DMA_{IN})
unnamed: S4.23 (INT_{OUT}), S5.28 (INT_{IN})
unnamed: S4.24 (DMA_{OUT}), S5.27 (DMA_{IN})
unnamed: S5.23 (INT_{OUT}), S6.28 (INT_{IN})
unnamed: S5.24 (DMA_{OUT}), S6.27 (DMA_{IN})
unnamed: S6.23 (INT_{OUT}), S7.28 (INT_{IN})
unnamed: S6.24 (DMA_{OUT}), S7.27 (DMA_{IN})
USER1_{39}: H12.6 (E3), JP10.1 (A), JP10.2 (B), RA01.8 (R7.2)
~DEV_SEL_{41}: H2.7 (~Z7), H2.9 (~Z6), H2.10 (~Z5), H2.11 (~Z4), H2.12 (~Z3), H2.13 (~Z2), H2.14 (~Z1), H2.15 (~Z0), S0.41 (~DEV_{SEL}), S1.41 (~DEV_{SEL}), S2.41 (~DEV_{SEL}), S3.41 (~DEV_{SEL}), S4.41 (~DEV_{SEL}), S5.41 (~DEV_{SEL}), S6.41 (~DEV_{SEL}), S7.41 (~DEV_{SEL})
~I/O_SEL_{1}: H12.7 (~Z7), H12.9 (~Z6), H12.10 (~Z5), H12.11 (~Z4), H12.12 (~Z3), H12.13 (~Z2), H12.14 (~Z1), S1.1 (~I/O_{SEL}), S2.1 (~I/O_{SEL}), S3.1 (~I/O_{SEL}), S4.1 (~I/O_{SEL}), S5.1 (~I/O_{SEL}), S6.1 (~I/O_{SEL}), S7.1 (~I/O_{SEL})
ɸ1_{36}: H2.5 (~E2)

Notes on the sheet:
FROM MICROPROCESSOR
FROM CLOCK GENERATOR
FROM ROM
REV. 1, 7 AND RFI: SYNC AND COLOR REF CONNECT TO SLOT 7 ONLY; PINS 19 AND 35 FORM TWO BUSES FROM SLOT 0 TO SLOT 6. REV. 0: NO CONNECION TO SYNC OR COLOR REF; PINS 19 AND 35 FORM TWO BUSSES FROM SLOT 0 TO SLOT 7.
FROM PERIPHERAL I/O CONNECTORS
TO ON- BOARD I/O
REV. 7 AND RFI ONLY
FROM MICROPROCESOR
FROM VIDEO GENERATOR PT1
PERIPHERAL I/O CONNECTORS
