omega9380/Retro-Schematics/Apple/Apple II/Apple II - Power Supply.kicad_sch

## KiCad design Apple/Apple II/Apple II - Power Supply.kicad_sch (2022-12-21)

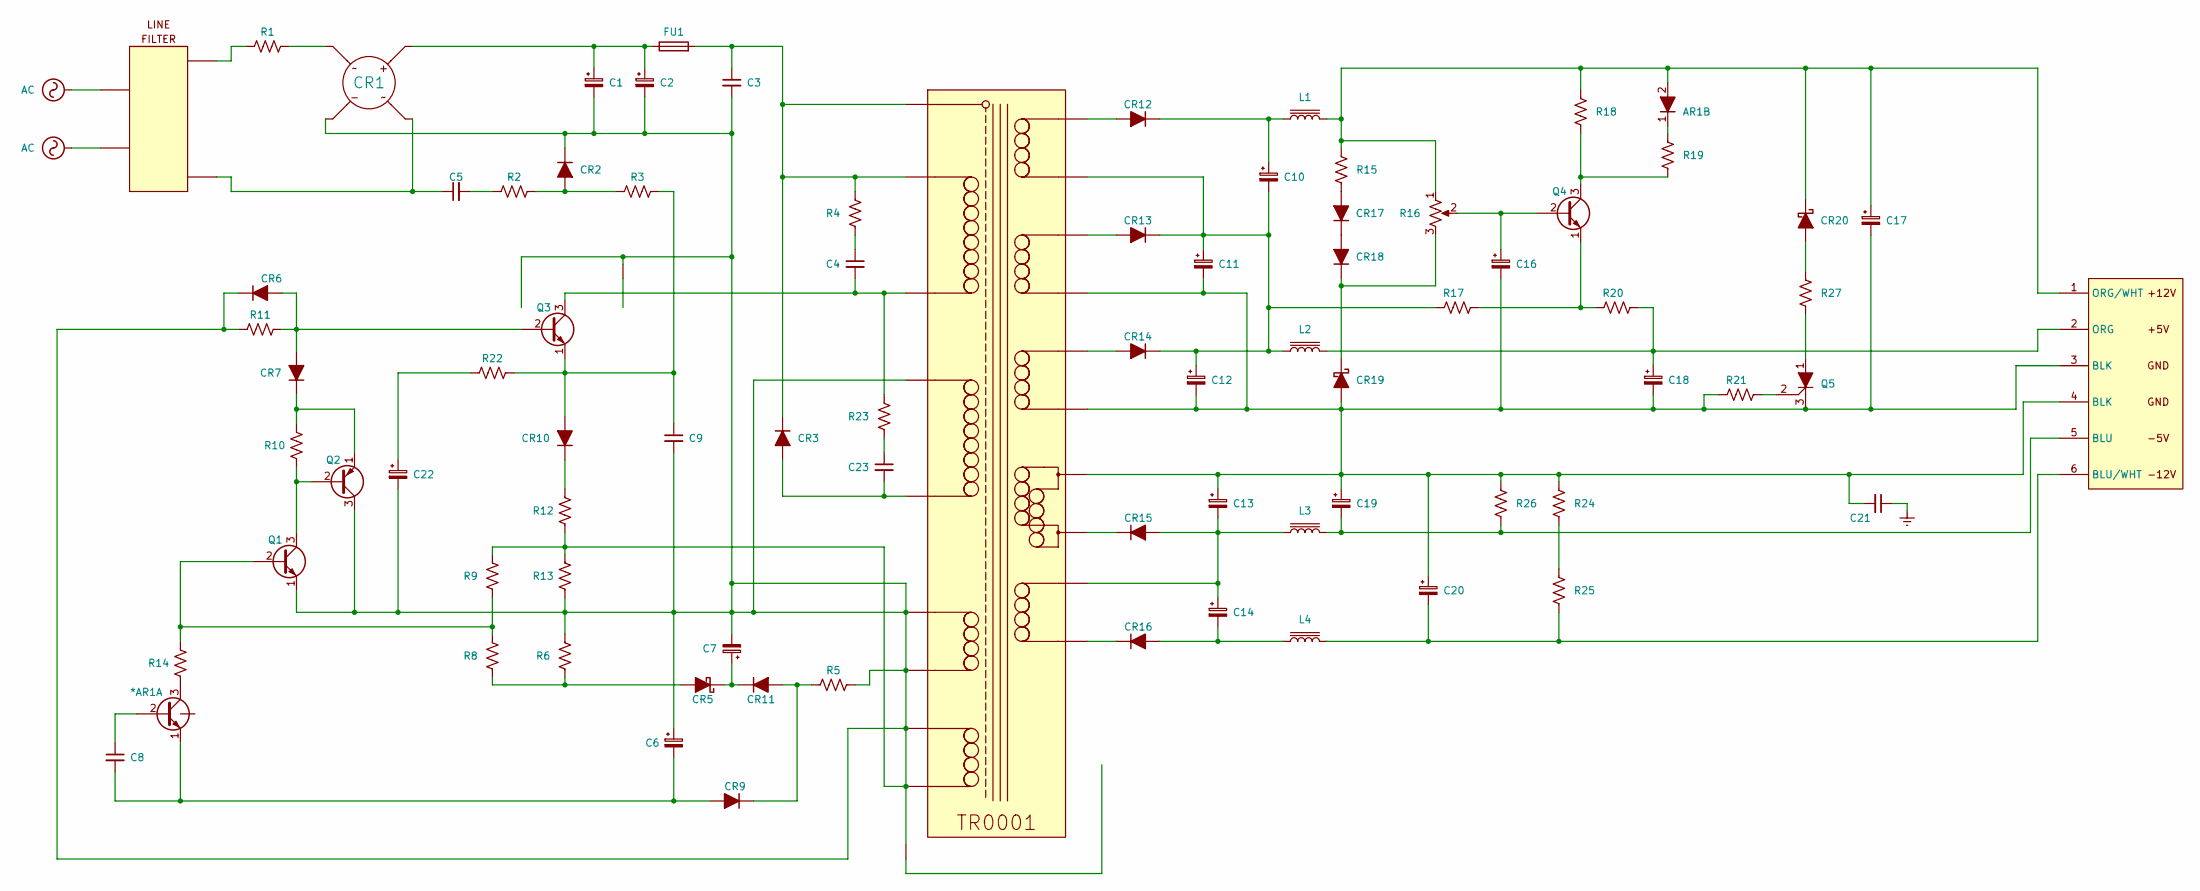
[picture p64: schematic Apple II - Power Supply.kicad_sch]

Parts:
*AR1: AR1_Amplifier
AR1: AR1_Amplifier
C1, C2, C6, C7, C10, C11, C12, C13, C14, C16, C17, C18, C19, C20, C22: C_Polarized_Small
C3, C4, C5, C8, C9, C21, C23: C_Small
CR1: CR1_BRIDGE_RECTIFIER
CR2, CR3, CR6, CR7, CR9, CR10, CR11, CR12, CR13, CR14, CR15, CR16, CR17, CR18: D_Filled
CR5, CR19, CR20: D_Schottky
FU1: Fuse
L1, L2, L3, L4: L_Iron
Q1, Q3, Q4: 2N2219; TO-39-3
Q2: 2N3906; TO-92_Inline
Q5: Q5
R1, R2, R3, R4, R5, R6, R8, R9, R10, R11, R12, R13, R14, R15, R17, R18, R19, R20, R21, R22, R23, R24, R25, R26, R27: R_US
R16: R_Potentiometer_US

Connections:
unnamed: *AR1.1, C6.2, C8.2, CR9.2 (A)
unnamed: *AR1.2, C8.1
unnamed: *AR1.3, R14.1
unnamed: AR1.1, R19.1
unnamed: AR1.2, C17.1, CR20.1 (K), L1.2, R15.1, R16.1, R18.1
unnamed: C1.1, C2.1, CR1., FU1.1
unnamed: C1.2, C2.2, C3.2, C6.1, C7.2, C9.2, C22.2, CR1., CR2.1 (K), CR6.1 (K), Q1.1 (E), Q2.3 (C), R5.1, R6.2, R9.2, R11.1, R12.1, R13.1, R13.2
unnamed: C3.1, CR3.1 (K), FU1.2, R4.2
unnamed: C4.1, R4.1
unnamed: C4.2, Q3.3 (C), R23.2
unnamed: C5.1, CR1.
unnamed: C5.2, R2.1
unnamed: C7.1, CR5.1 (K), CR11.1 (K)
unnamed: C9.1, CR10.2 (A), Q3.1 (E), R3.2, R22.1
unnamed: C10.1, CR12.1 (K), L1.1
unnamed: C10.2, C11.1, C12.1, CR13.1 (K), CR14.1 (K), L2.1, R17.1
unnamed: C11.2, C12.2, C13.1, C16.2, C17.2, C18.2, C19.1, C20.1, C21.2, CR19.2 (A), Q5.3, R21.1, R24.1, R26.1
unnamed: C13.2, C14.1, CR15.2 (A), L3.1
unnamed: C14.2, CR16.2 (A), L4.1
unnamed: C16.1, Q4.2 (B), R16.2
unnamed: C18.1, L2.2, R20.2
unnamed: C19.2, L3.2, R26.2
unnamed: C20.2, L4.2, R25.2
unnamed: C22.1, R22.2
unnamed: C23.1, R23.1
unnamed: C23.2, CR3.2 (A)
unnamed: CR1., R1.2
unnamed: CR2.2 (A), R2.2, R3.1
unnamed: CR5.2 (A), R6.1, R8.1
unnamed: CR6.2 (A), CR7.2 (A), Q3.2 (B), R11.2
unnamed: CR7.1 (K), Q2.1 (E), R10.2
unnamed: CR10.1 (K), R12.2
unnamed: CR9.1 (K), CR11.2 (A), R5.2
unnamed: CR17.1 (K), CR18.2 (A)
unnamed: CR17.2 (A), R15.2
unnamed: CR18.1 (K), CR19.1 (K), R16.3
unnamed: CR20.2 (A), R27.1
unnamed: Q1.2 (B), R8.2, R9.1, R14.2
unnamed: Q1.3 (C), Q2.2 (B), R10.1
unnamed: Q4.1 (E), R17.2, R20.1
unnamed: Q4.3 (C), R18.2, R19.2
unnamed: Q5.1, R27.2
unnamed: Q5.2, R21.2
unnamed: R24.2, R25.1
