omega9380/Retro-Schematics/Apple/Apple II/Apple II - ROM (All Revisions).kicad_sch

## KiCad design Apple/Apple II/Apple II - ROM (All Revisions).kicad_sch (2022-12-21)

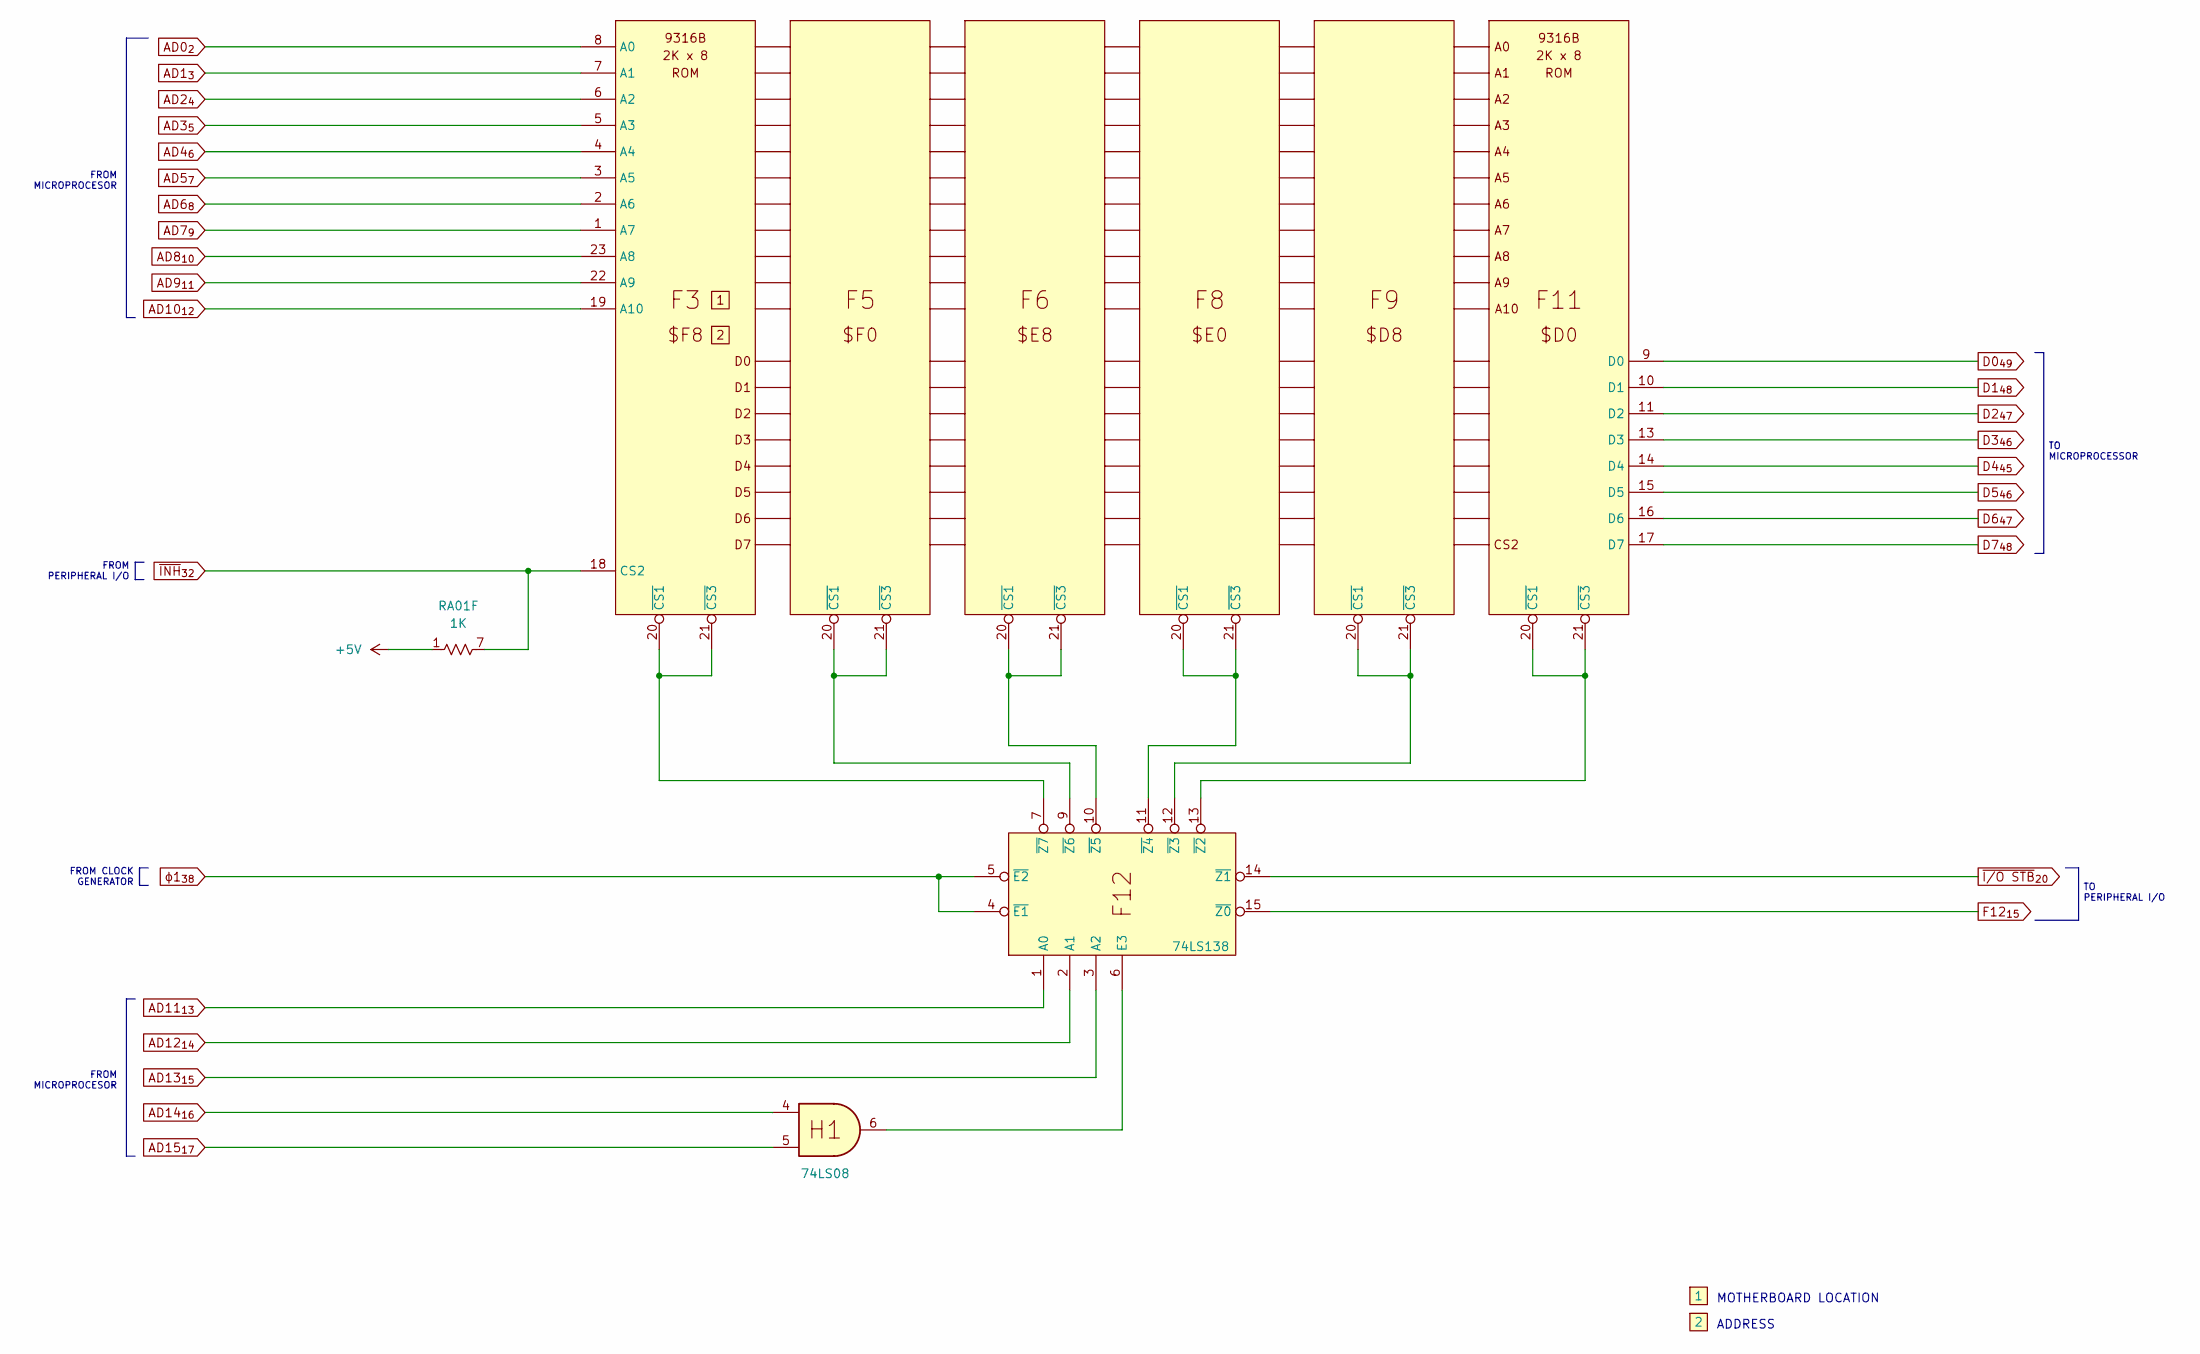
[picture p65: schematic Apple II - ROM (All Revisions).kicad_sch]

Parts:
F12: 74LS138
H1: 74LS08
N1: 1
N2: 2
RA01: 1K; R_Array_SIP9

Connections:
AD11_{13}: F12.1 (A0)
AD12_{14}: F12.2 (A1)
AD13_{15}: F12.3 (A2)
AD14_{16}: H1.4
AD15_{17}: H1.5
F12_{15}: F12.15 (~Z0)
unnamed: F12.6 (E3), H1.6
~INH_{32}: RA01.7 (R6.2)
~I/O STB_{20}: F12.14 (~Z1)
ɸ1_{38}: F12.4 (~E1), F12.5 (~E2)

Notes on the sheet:
FROM PERIPHERAL I/O
TO PERIPHERAL I/O
ADDRESS
TO MICROPROCESSOR
FROM MICROPROCESOR
MOTHERBOARD LOCATION
FROM CLOCK GENERATOR
