omega9380/Retro-Schematics/Apple/Apple II/Apple II - Single Piece Keyboard.kicad_sch

## KiCad design Apple/Apple II/Apple II - Single Piece Keyboard.kicad_sch (2022-12-21)

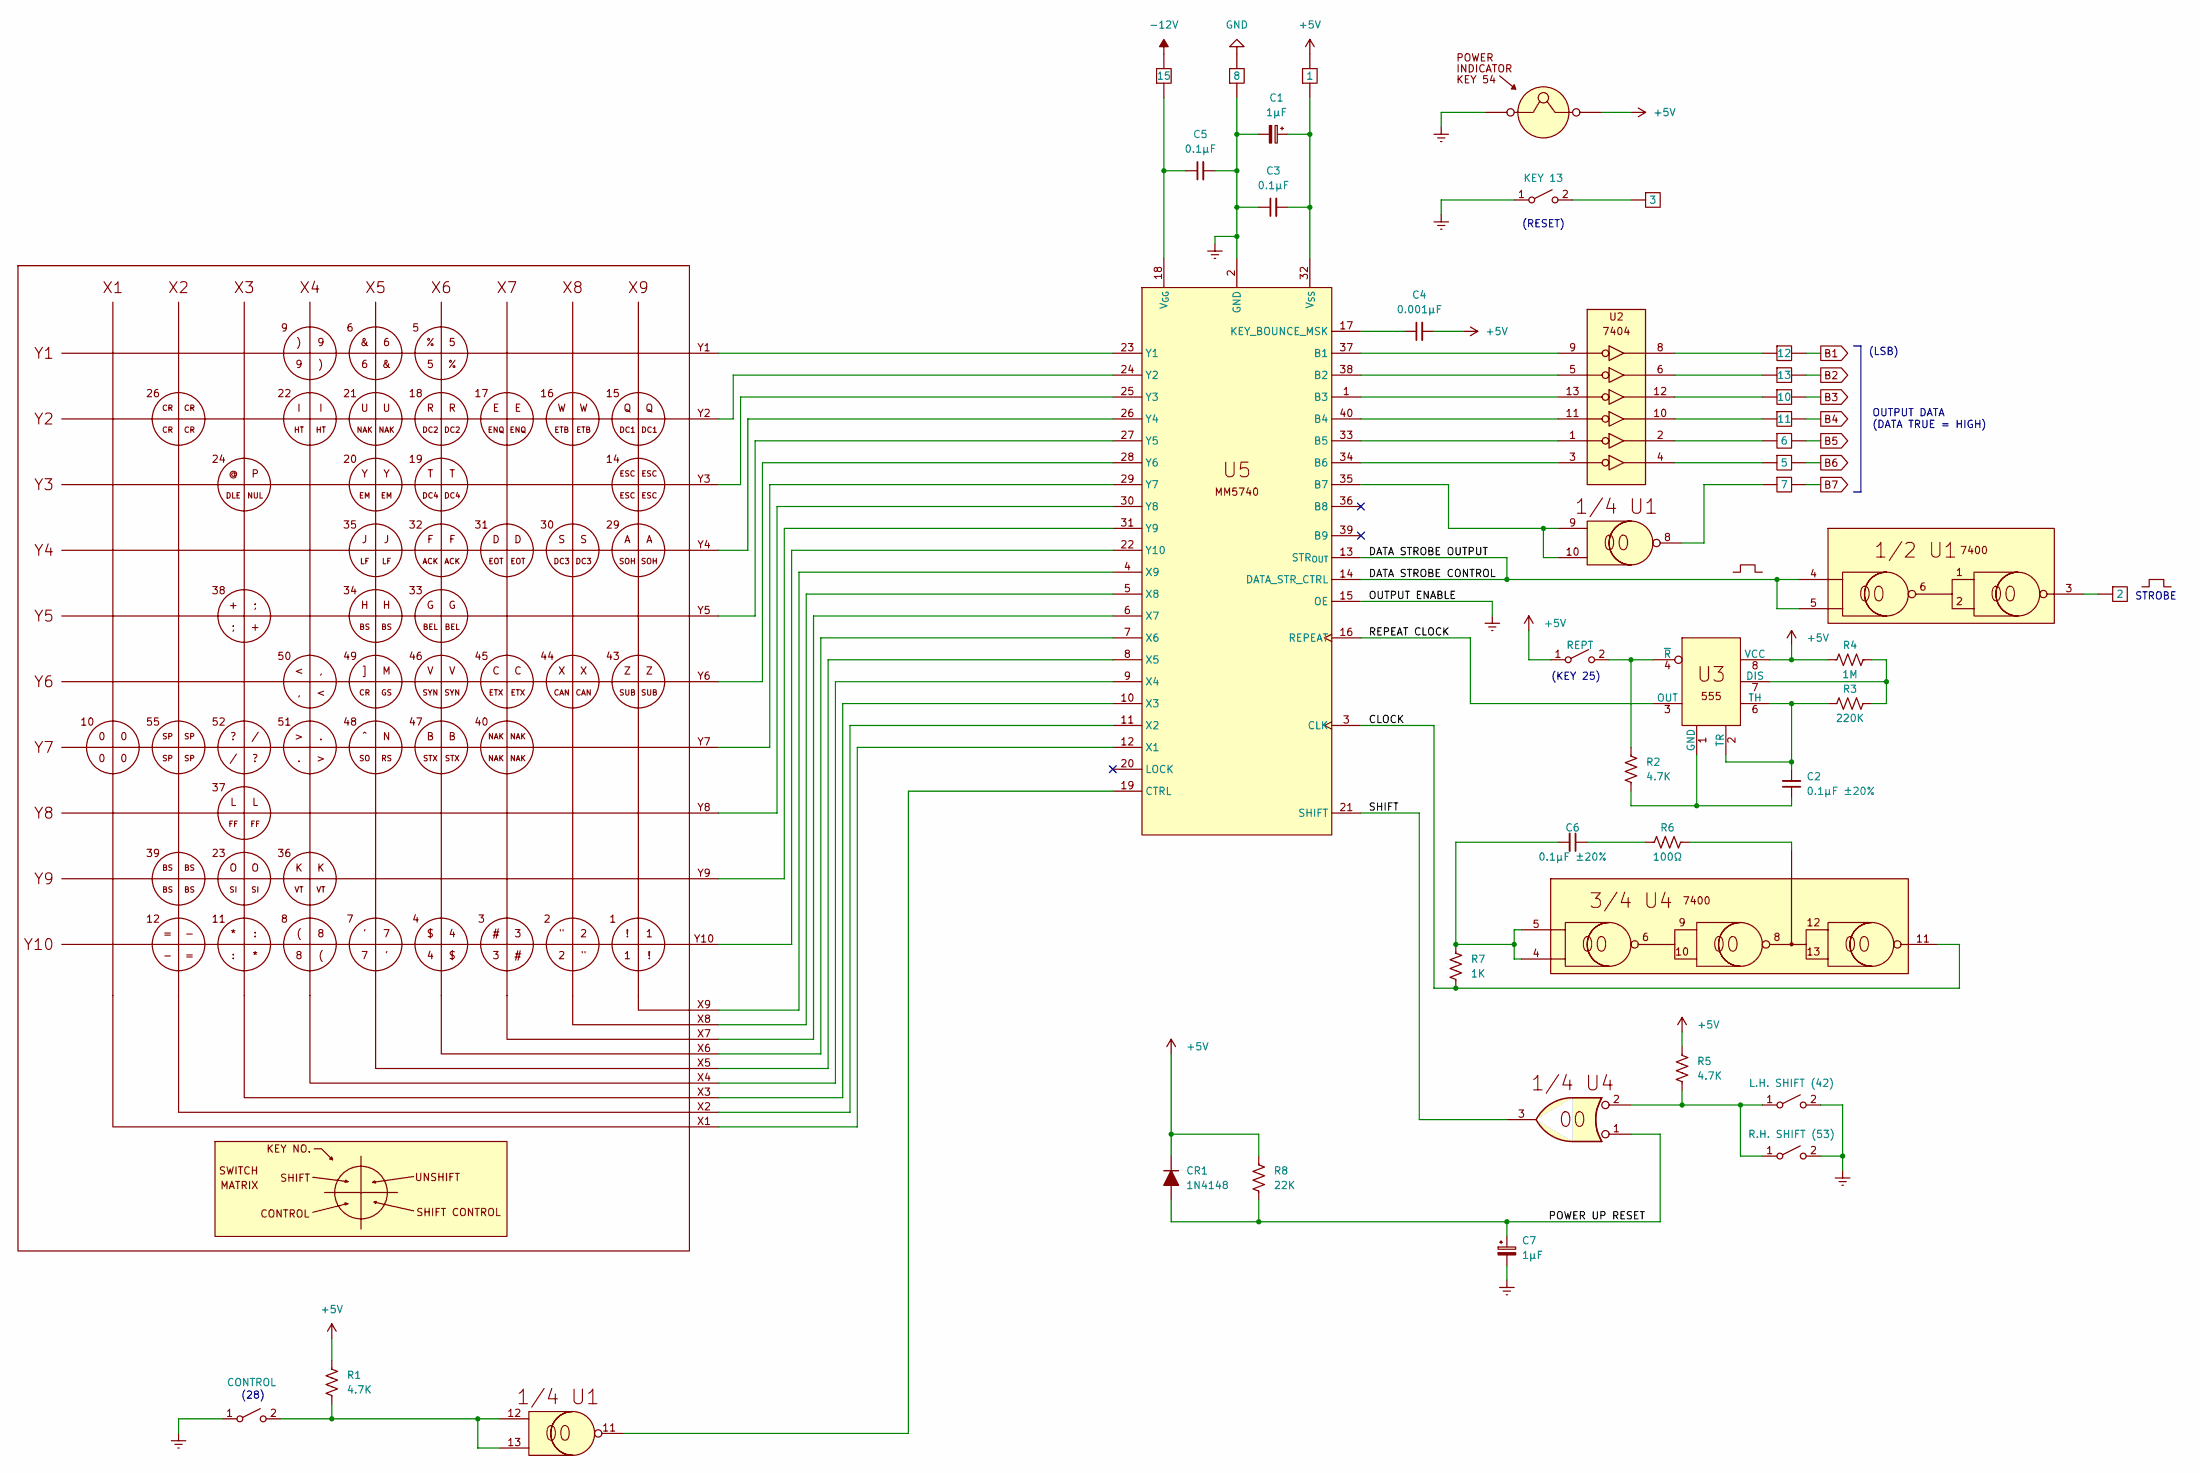
[picture p66: schematic Apple II - Single Piece Keyboard.kicad_sch]

Parts:
C1, C7: 1µF
C2, C6: 0.1µF ±20%
C3, C5: 0.1µF
C4: 0.001µF
CR1: 1N4148
KBDN1: 1
KBDN2: 2
KBDN3: 3
KBDN5: 5
KBDN6: 6
KBDN7: 7
KBDN8: 8
KBDN10: 10
KBDN11: 11
KBDN12: 12
KBDN13: 13
KBDN15: 15
R1, R2, R5: 4.7K
R3: 220K
R4: 1M
R6: 100Ω
R7: 1K
R8: 22K
SW13: KEY 13
SW25: REPT
SW28: CONTROL
SW42: L.H. SHIFT (42)
SW53: R.H. SHIFT (53)

Connections:
B1: KBDN12.
B2: KBDN13.
B3: KBDN10.
B4: KBDN11.
B5: KBDN6.
B6: KBDN5.
B7: KBDN7.
CLOCK: R7.1
unnamed: C1.1, C3.2, KBDN1.
unnamed: C1.2, C3.1, C5.2, KBDN8.
unnamed: C2.1, R2.1
unnamed: C2.2, R3.1
unnamed: C5.1, KBDN15.
unnamed: C6.1, R6.1
unnamed: C6.2, R7.2
unnamed: CR1.1 (K), R8.2
unnamed: KBDN3., SW13.2 (B)
unnamed: R1.2, SW28.2 (B)
unnamed: R2.2, SW25.2 (B)
unnamed: R3.2, R4.2
unnamed: R5.1, SW42.1 (A), SW53.1 (A)
unnamed: SW42.2 (B), SW53.2 (B)
POWER UP RESET: C7.1, CR1.2 (A), R8.1

Notes on the sheet:
(KEY 25)
STROBE
(28)
OUTPUT DATA (DATA TRUE = HIGH)
(RESET)
(LSB)
