omega9380/Retro-Schematics/Apple/Apple II/Apple II - Two-piece Keyboard.kicad_sch

## KiCad design Apple/Apple II/Apple II - Two-piece Keyboard.kicad_sch (2022-12-21)

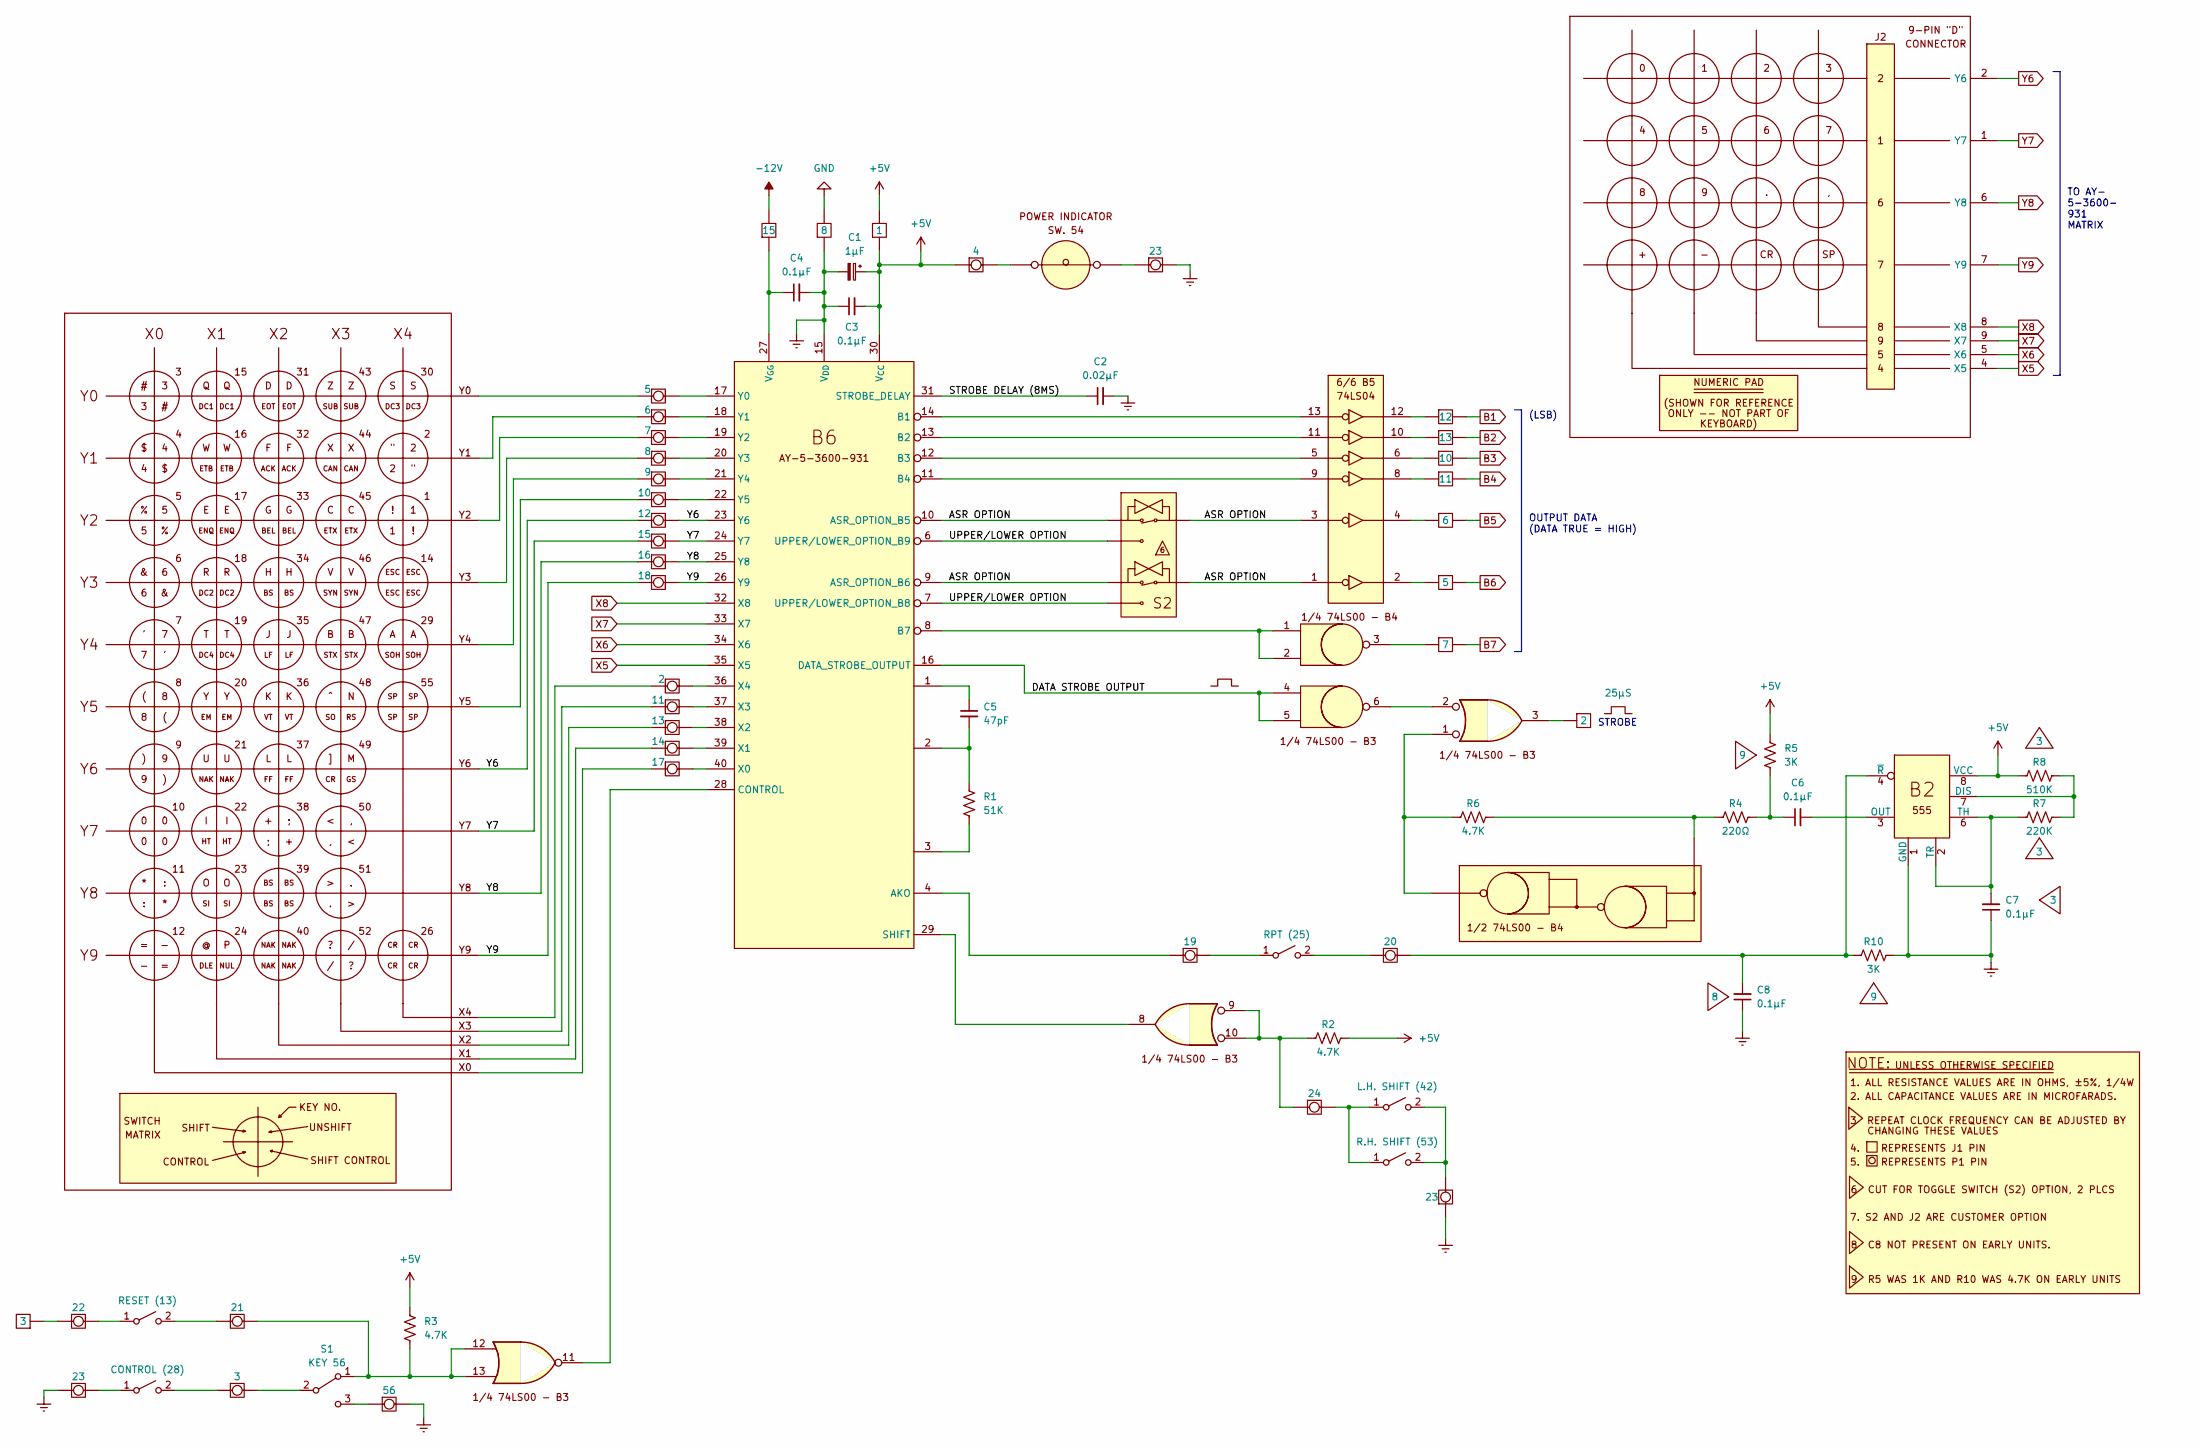
[picture p67: schematic Apple II - Two-piece Keyboard.kicad_sch]

Parts:
C1: 1µF
C2: 0.02µF
C3, C4, C6, C7, C8: 0.1µF
C5: 47pF
KBDN2: 2
KBDN3: 3
KBDN4: 4
KBDN5: 5
KBDN6: 6
KBDN7: 7
KBDN8: 8
KBDN9: 9
KBDN10: 10
KBDN11: 11
KBDN12: 12
KBDN13: 13
KBDN14: 14
KBDN15: 15
KBDN16: 16
KBDN17: 17
KBDN18: 18
KBDN21: 21
KBDN22: 22
KBDN23: 23
KBDN24: 24
KBDN56: 56
R1: 51K
R2, R3, R6: 4.7K
R4: 220Ω
R5, R10: 3K
R7: 220K
R8: 510K
S1: KEY 56
SW13: RESET (13)
SW25: RPT (25)
SW28: CONTROL (28)
SW42: L.H. SHIFT (42)
SW53: R.H. SHIFT (53)

Connections:
B1: KBDN12.
B2: KBDN13.
B3: KBDN10.
B4: KBDN11.
B5: KBDN6.
B6: KBDN5.
B7: KBDN7.
unnamed: C1.1, C3.2, KBDN4.
unnamed: C1.2, C3.1, C4.2, KBDN8.
unnamed: C4.1, KBDN15.
unnamed: C5.2, R1.1
unnamed: C6.1, R4.2, R5.2
unnamed: C7.1, R10.2
unnamed: C7.2, R7.1
unnamed: C8.2, R10.1
unnamed: KBDN3., S1.2 (B), SW28.2 (B)
unnamed: KBDN21., R3.2, S1.1 (A), SW13.2 (B)
unnamed: KBDN3., KBDN22., SW13.1 (A)
unnamed: KBDN23., SW28.1 (A), SW42.2 (B), SW53.2 (B)
unnamed: KBDN24., R2.1, SW42.1 (A), SW53.1 (A)
unnamed: KBDN56., S1.3 (C)
unnamed: R4.1, R6.2
unnamed: R7.2, R8.2
STROBE DELAY (8MS): C2.1
Y6: KBDN12.
Y7: KBDN15.
Y8: KBDN16.
Y9: KBDN18.

Notes on the sheet:
OUTPUT DATA (DATA TRUE = HIGH)
TO AY- 5-3600- 931 MATRIX
STROBE
(LSB)
