omega9380/Retro-Schematics/Apple/Apple II/Apple II - Video Address Generator (all revisions).kicad_sch

## KiCad design Apple/Apple II/Apple II - Video Address Generator (all revisions).kicad_sch (2022-07-12)

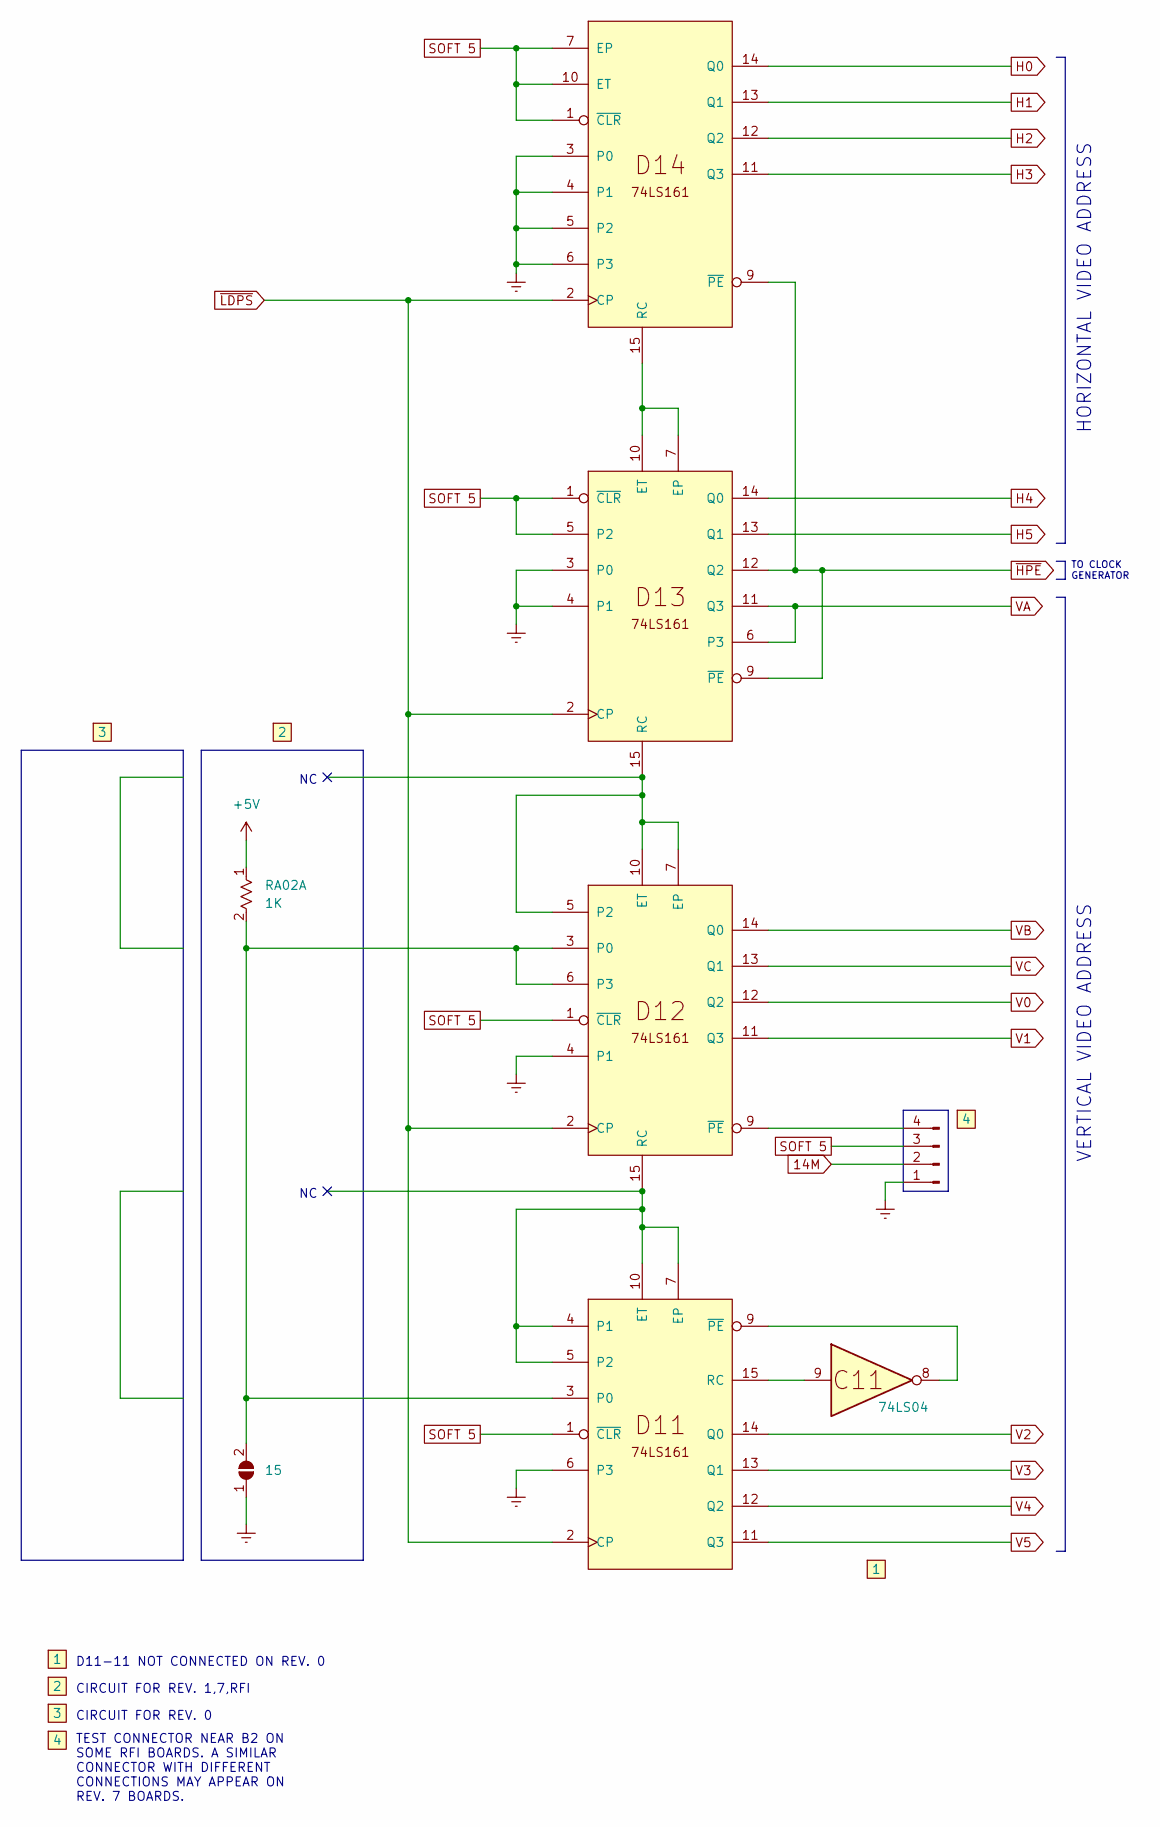
[picture p68: schematic Apple II - Video Address Generator (all revisions).kicad_sch]

Parts:
JP15: 15
N1: 1
N2: 2
N3: 3
N4: 4
RA02: 1K; R_Array_SIP9

Connections:
unnamed: JP15.2 (B), RA02.2 (R1.2)

Notes on the sheet:
TEST CONNECTOR NEAR B2 ON SOME RFI BOARDS. A SIMILAR CONNECTOR WITH DIFFERENT CONNECTIONS MAY APPEAR ON REV. 7 BOARDS.
D11-11 NOT CONNECTED ON REV. 0
VERTICAL VIDEO ADDRESS
HORIZONTAL VIDEO ADDRESS
CIRCUIT FOR REV. 1,7,RFI
TO CLOCK GENERATOR
CIRCUIT FOR REV. 0
