omega9380/Retro-Schematics/Apple/Apple II/Apple II - Video Generator Pt 1 of 2 (Rev 1).kicad_sch

## KiCad design Apple/Apple II/Apple II - Video Generator Pt 1 of 2 (Rev 1).kicad_sch (2022-12-21)

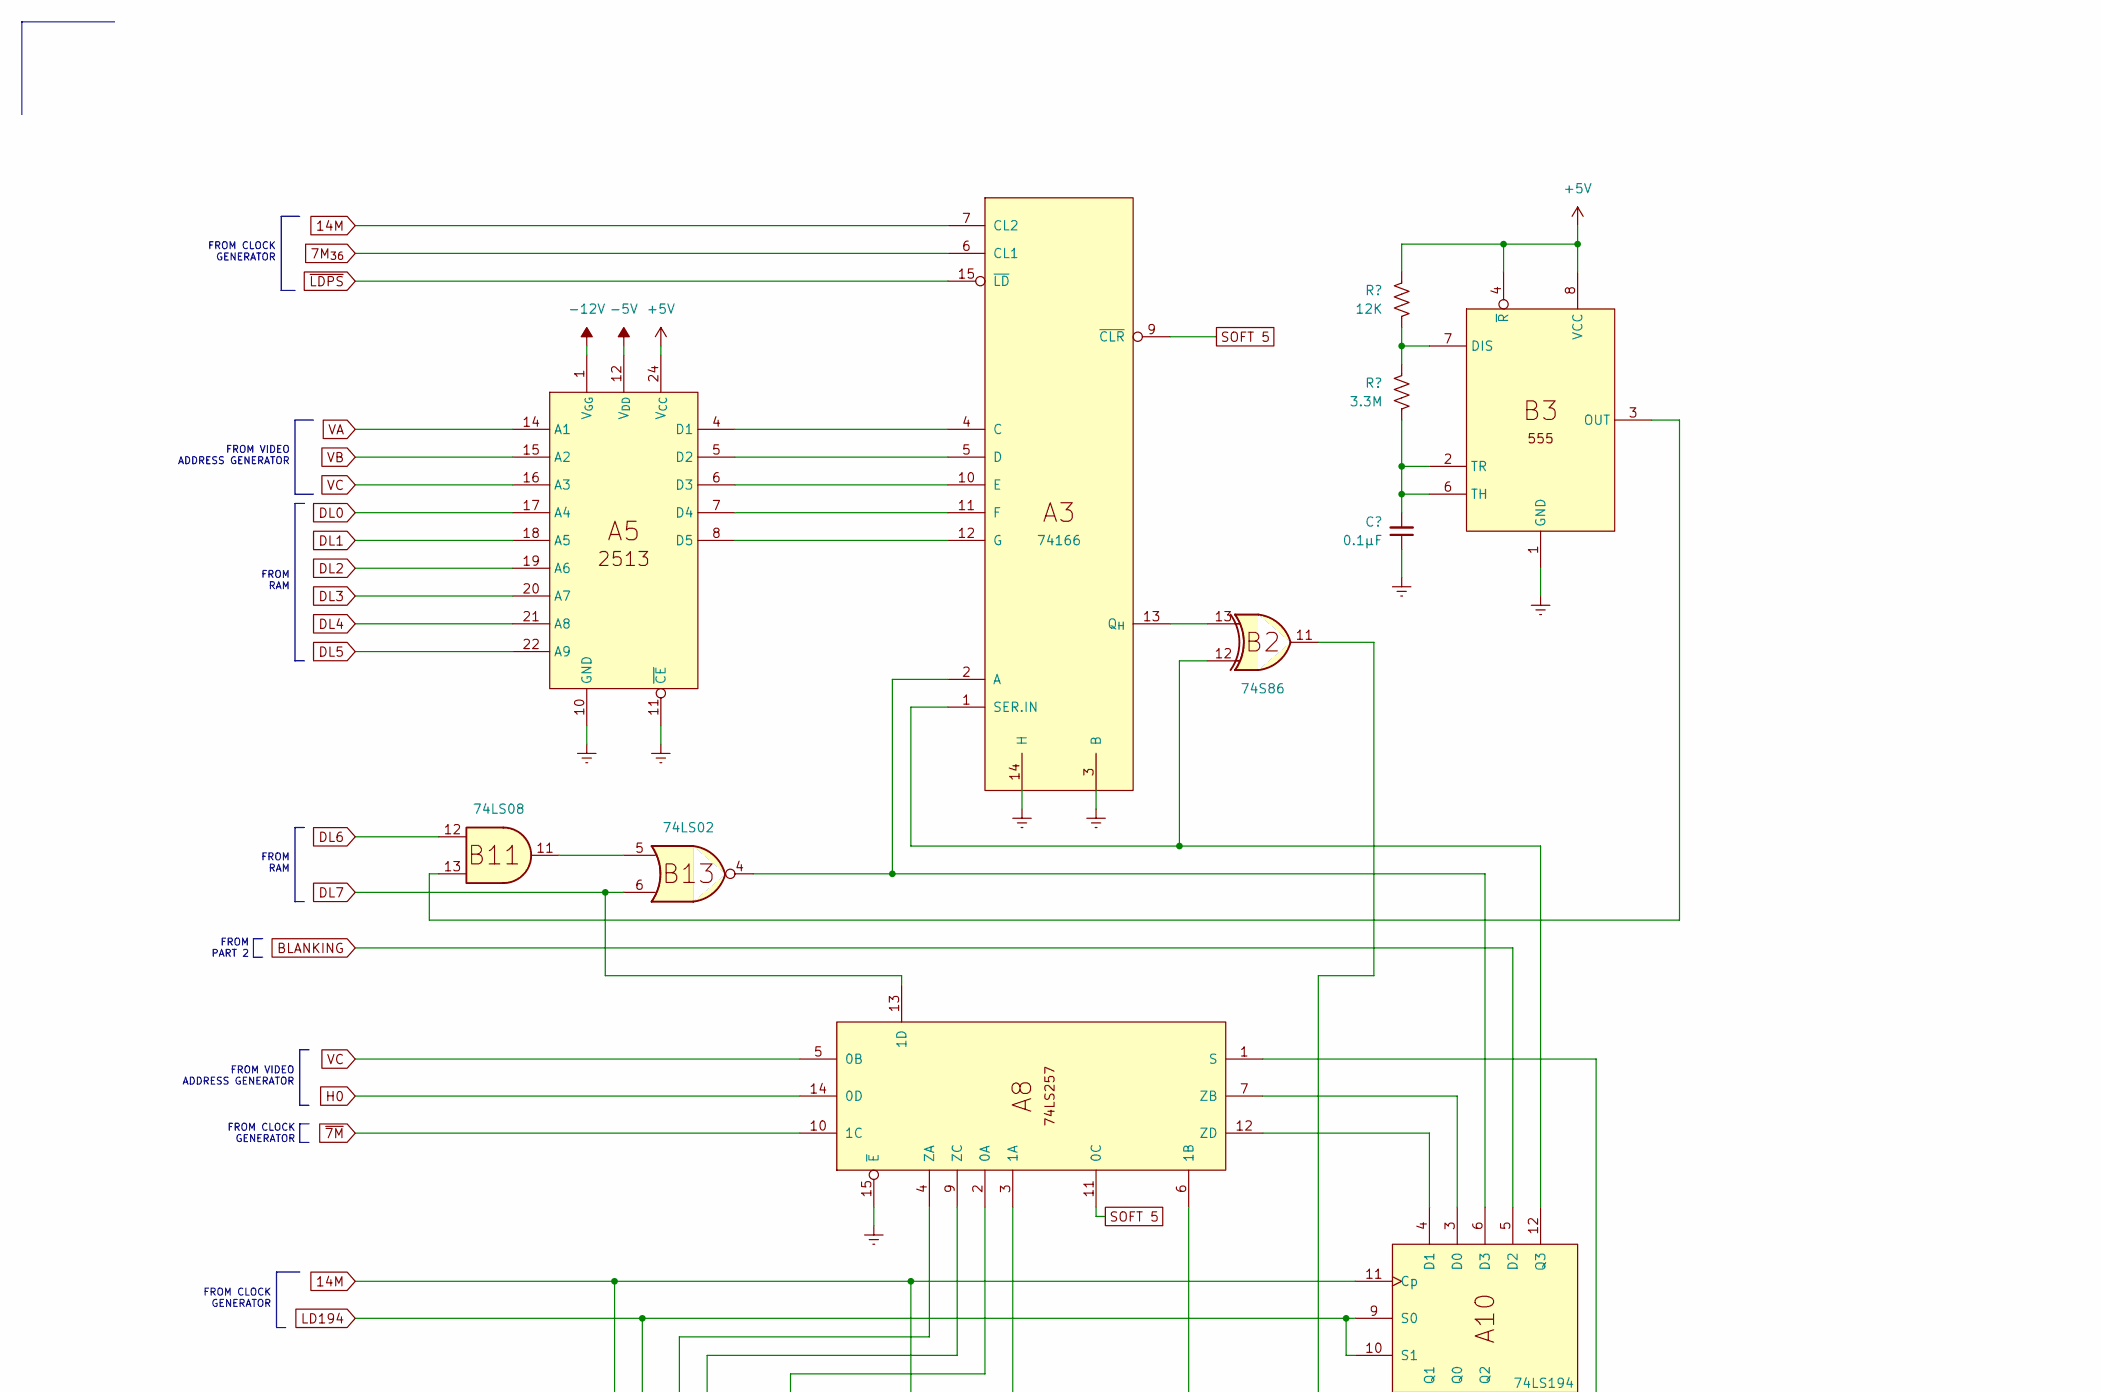
[picture p69: schematic Apple II - Video Generator Pt 1 of 2 (Rev 1).kicad_sch, part in row 1, column 1]

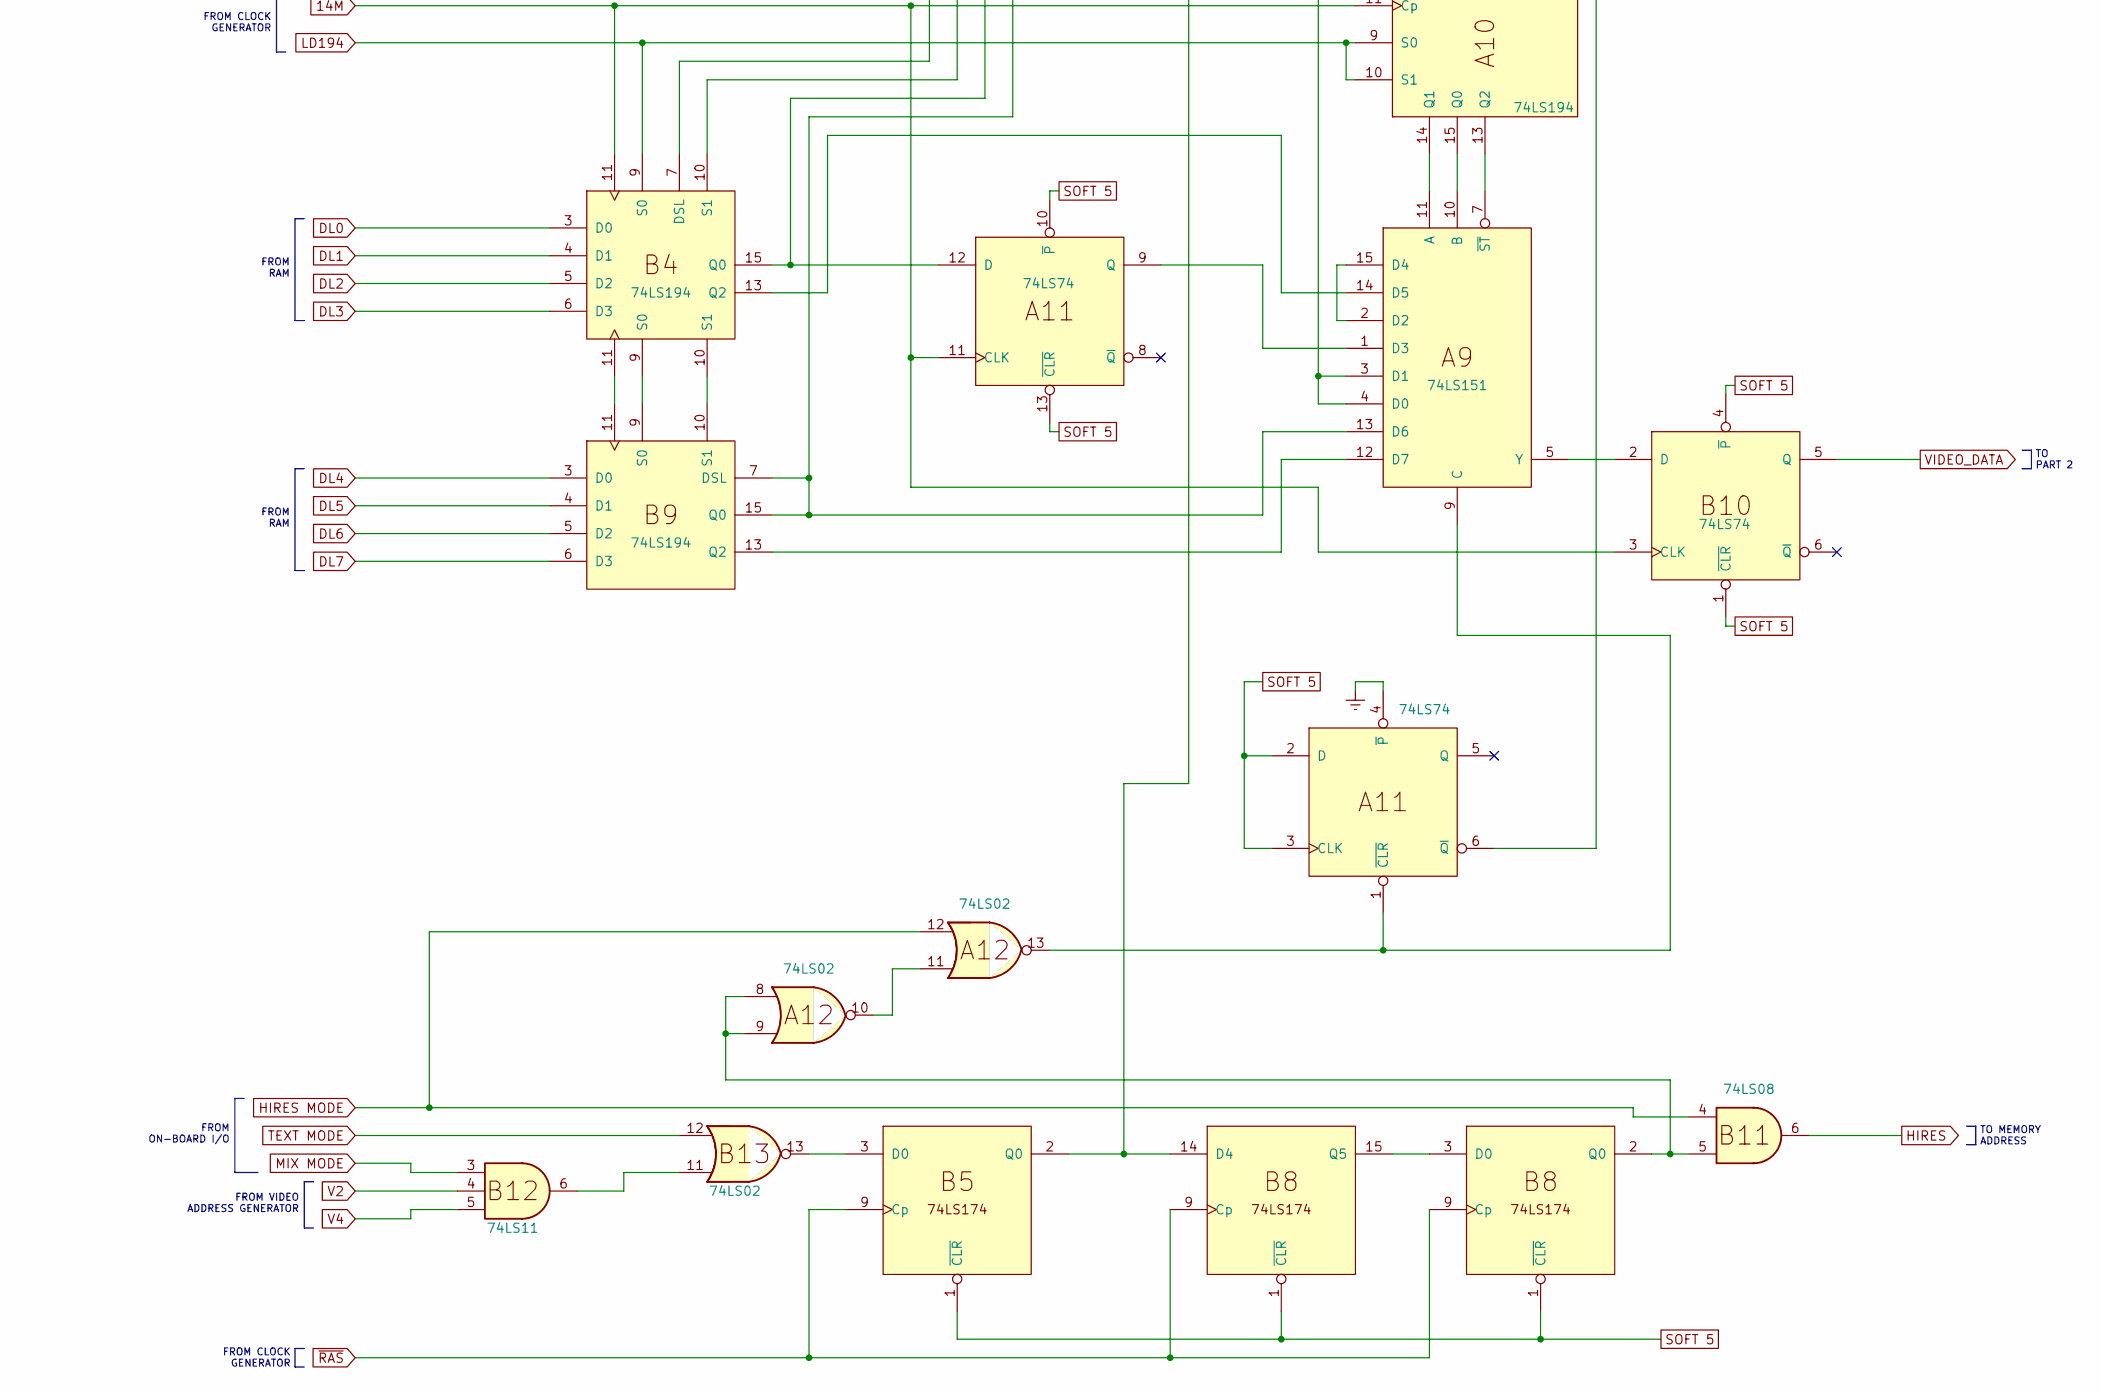
[picture p70: schematic Apple II - Video Generator Pt 1 of 2 (Rev 1).kicad_sch, part in row 2, column 1]

Parts:
A11: 74LS74
A12: 74LS02
B11: 74LS08
a11: 74LS74

Connections:
14M: a11.11 (CLK)
HIRES: B11.6
HIRES MODE: A12.12, B11.4
unnamed: A11.1 (~CLR), A12.13
unnamed: A12.8, A12.9, B11.5
unnamed: A12.10, A12.11
SOFT 5: A11.2 (D), A11.3 (CLK), a11.10 (~P), a11.13 (~CLR)

Notes on the sheet:
FROM RAM
FROM VIDEO ADDRESS GENERATOR
FROM CLOCK GENERATOR
FROM PART 2
TO MEMORY ADDRESS
FROM ON-BOARD I/O
TO PART 2
