omega9380/Retro-Schematics/Apple/Apple II/Apple II - Video Generator Pt 1 of 2 (Rev 7,RFI).kicad_sch

## KiCad design Apple/Apple II/Apple II - Video Generator Pt 1 of 2 (Rev 7,RFI).kicad_sch (2022-12-21)

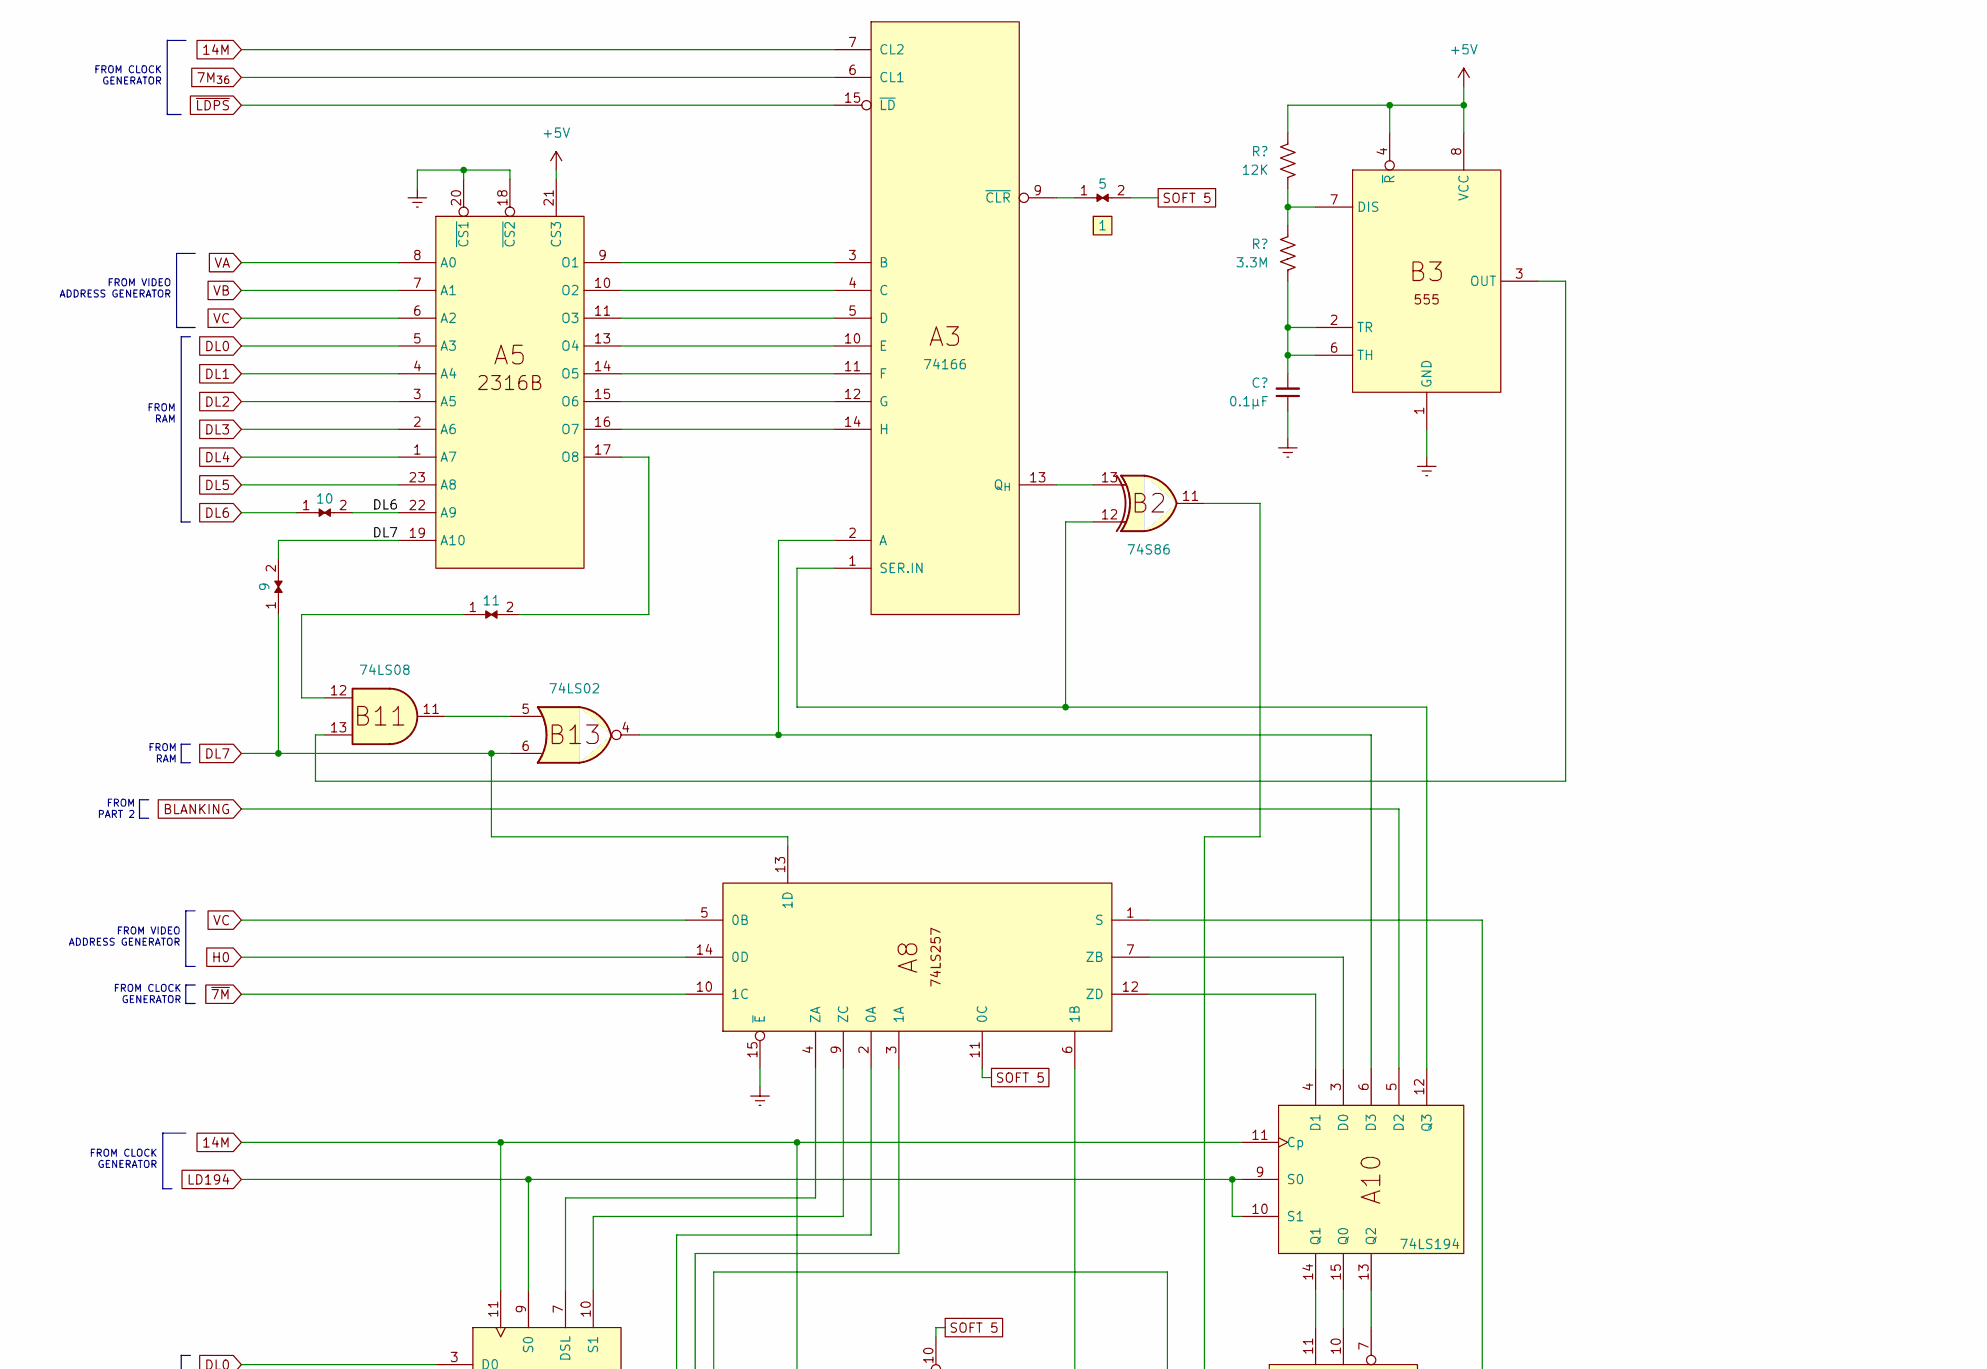
[picture p71: schematic Apple II - Video Generator Pt 1 of 2 (Rev 7,RFI).kicad_sch, part in row 1, column 1]

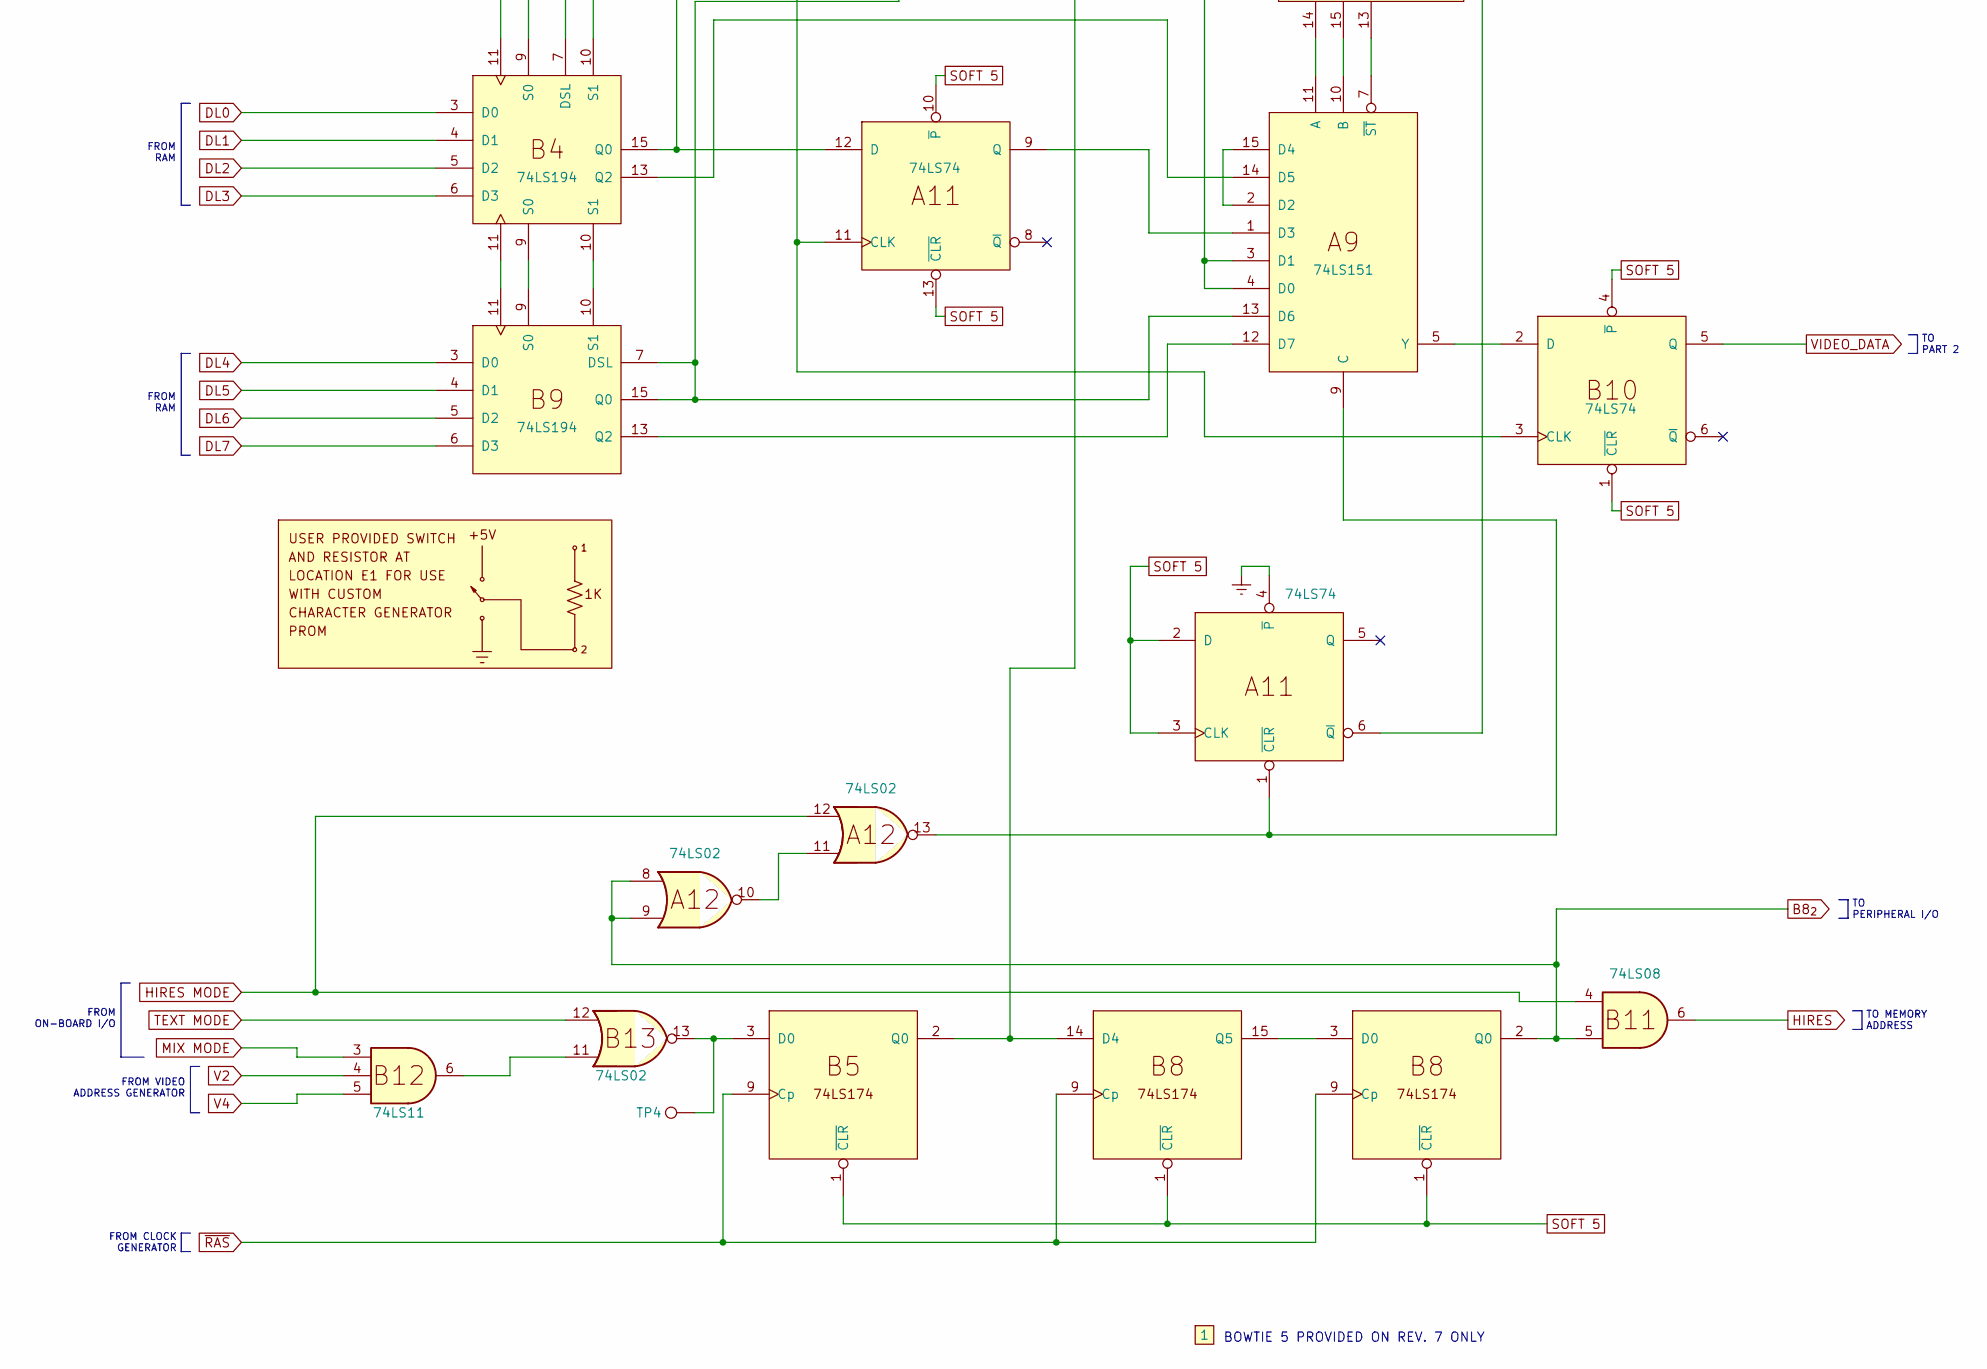
[picture p72: schematic Apple II - Video Generator Pt 1 of 2 (Rev 7,RFI).kicad_sch, part in row 2, column 1]

Parts:
B11: 74LS08
JP5: 5
JP9: 9
JP10: 10
JP11: 11
N1: 1
TP4: TestPoint

Connections:
B8_{2}: B11.5
DL6: JP10.1 (A), JP10.2 (B)
DL7: JP9.1 (A), JP9.2 (B)
HIRES: B11.6
HIRES MODE: B11.4
SOFT 5: JP5.2 (B)

Notes on the sheet:
FROM ON-BOARD I/O
FROM VIDEO ADDRESS GENERATOR
FROM RAM
TO PERIPHERAL I/O
BOWTIE 5 PROVIDED ON REV. 7 ONLY
TO PART 2
TO MEMORY ADDRESS
FROM CLOCK GENERATOR
FROM PART 2
