omega9380/Retro-Schematics/Apple/Apple II/Apple II - Video Generator Pt 2 of 2 (Rev 7).kicad_sch

## KiCad design Apple/Apple II/Apple II - Video Generator Pt 2 of 2 (Rev 7).kicad_sch (2022-07-17)

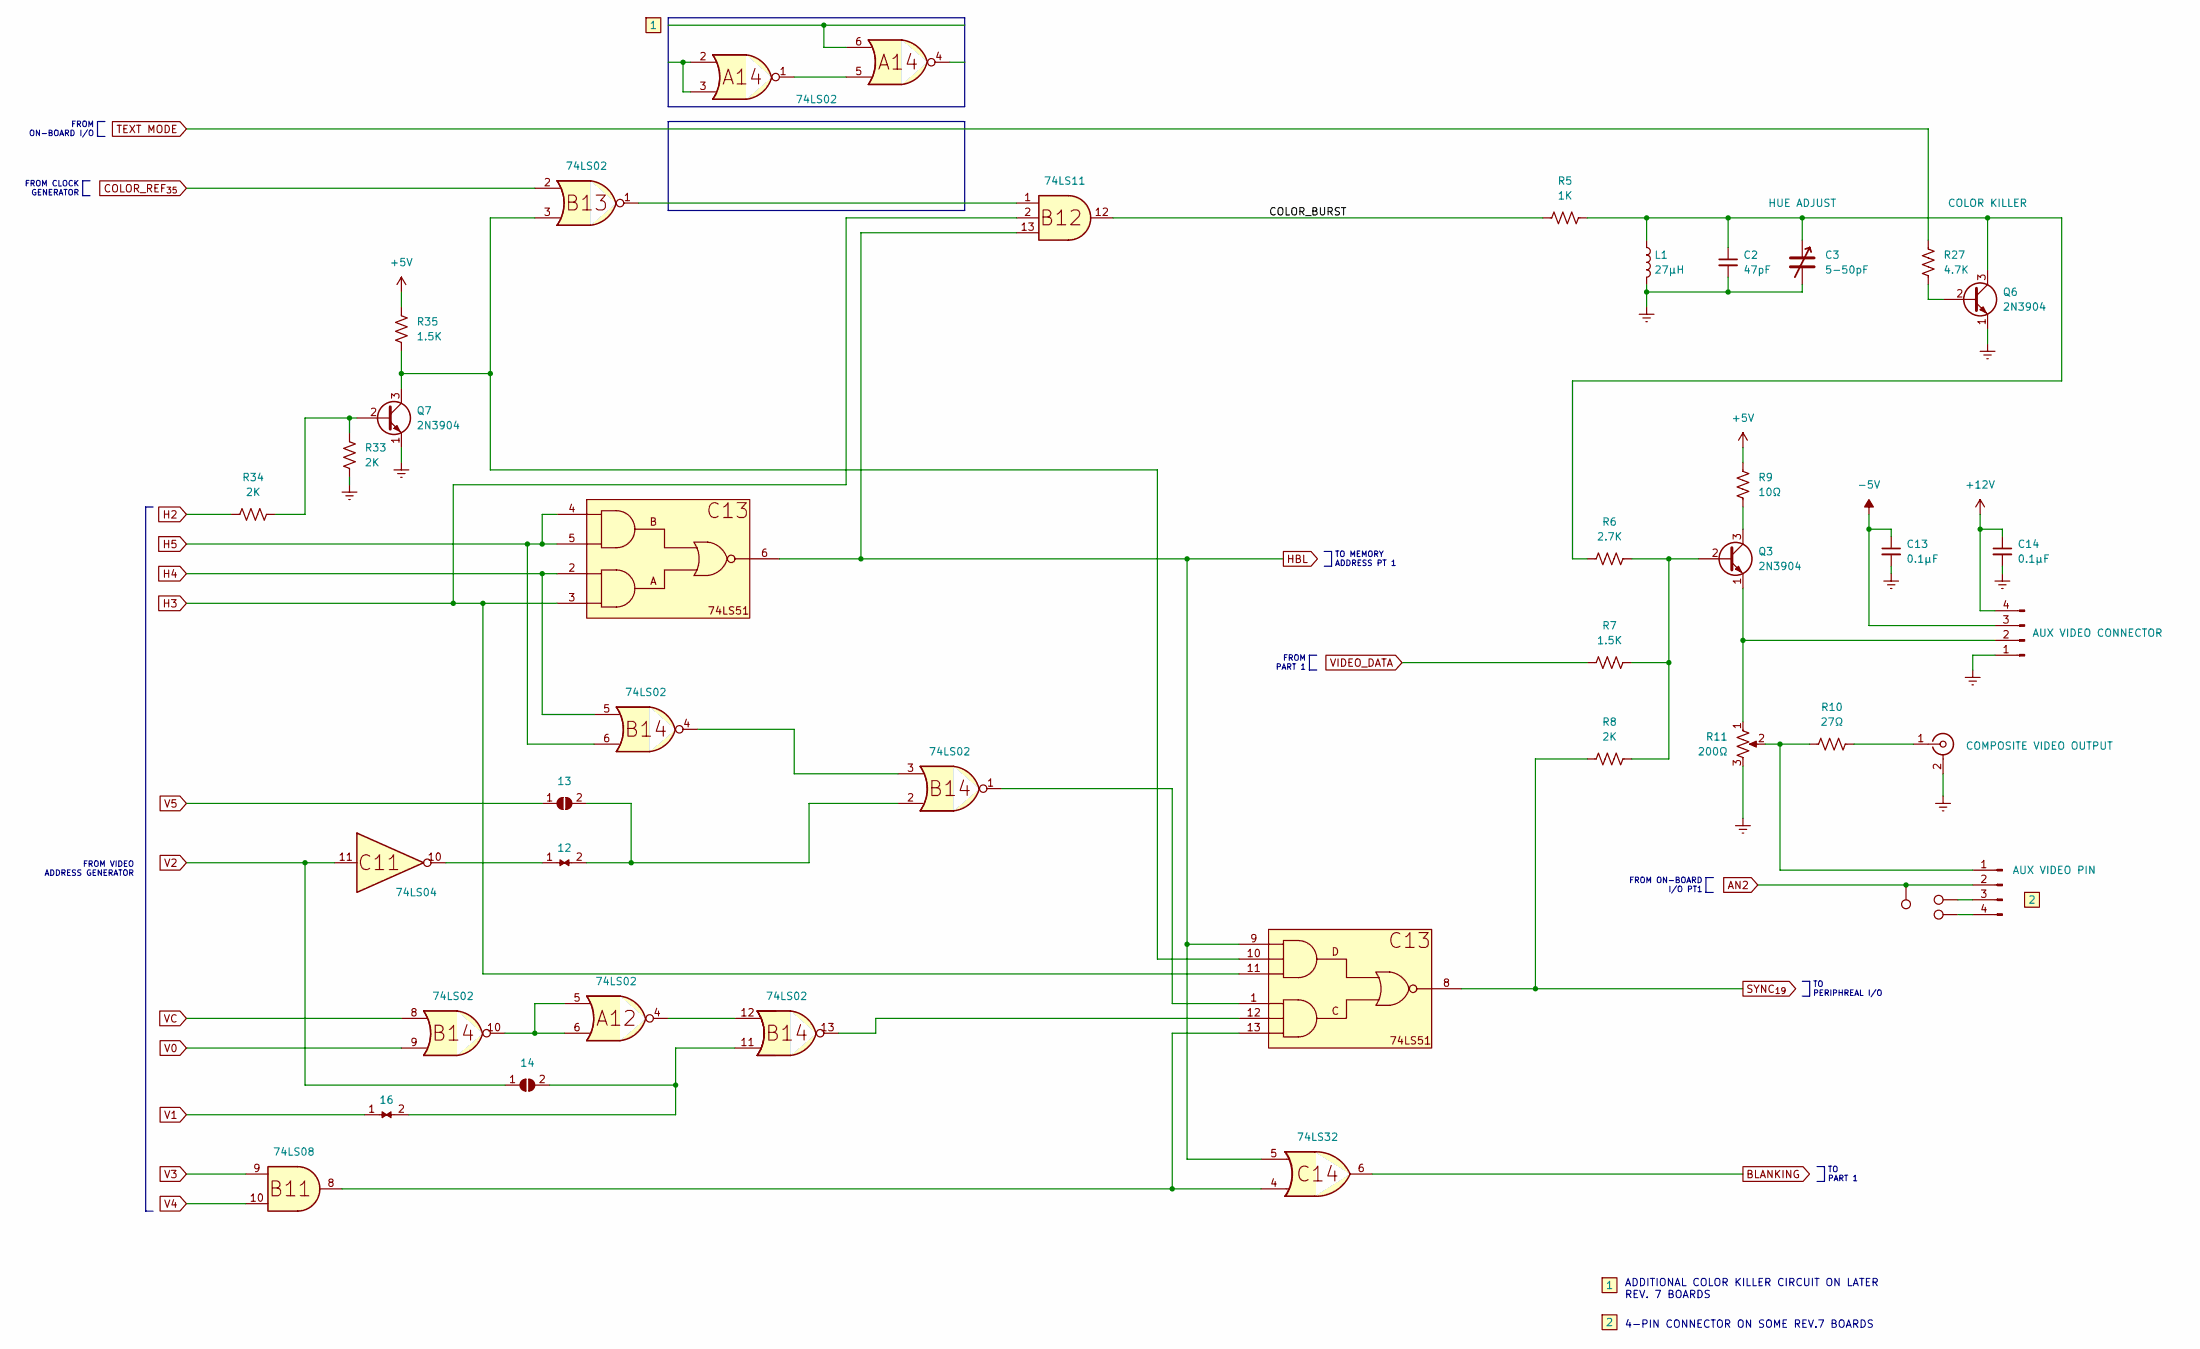
[picture p73: schematic Apple II - Video Generator Pt 2 of 2 (Rev 7).kicad_sch]

Parts:
A14: 74LS02
C2: 47pF
C3: 5-50pF
C13, C14: 0.1µF
L1: 27µH
N1: 1
N2: 2
Q3, Q6, Q7: 2N3904; TO-92_Inline
R5: 1K
R6: 2.7K
R7, R35: 1.5K
R8, R33, R34: 2K
R9: 10Ω
R10: 27Ω
R11: 200Ω
R27: 4.7K

Connections:
COLOR_BURST: R5.1
H2: R34.1
unnamed: A14.1, A14.5
unnamed: A14.2, A14.3
unnamed: C2.1, C3.1, L1.1, Q6.3 (C), R5.2, R6.1
unnamed: C2.2, C3.2, L1.2
unnamed: Q3.1 (E), R11.1
unnamed: Q3.2 (B), R6.2, R7.2, R8.2
unnamed: Q3.3 (C), R9.1
unnamed: Q6.2 (B), R27.2
unnamed: Q7.2 (B), R33.2, R34.2
unnamed: Q7.3 (C), R35.1
unnamed: R10.1, R11.2
SYNC_{19}: R8.1
TEXT MODE: R27.1
VIDEO_DATA: R7.1

Notes on the sheet:
4-PIN CONNECTOR ON SOME REV.7 BOARDS
FROM ON-BOARD I/O
FROM PART 1
FROM VIDEO ADDRESS GENERATOR
TO MEMORY ADDRESS PT 1
TO PERIPHREAL I/O
ADDITIONAL COLOR KILLER CIRCUIT ON LATER REV. 7 BOARDS
FROM CLOCK GENERATOR
FROM ON-BOARD I/O PT1
TO PART 1
