omega9380/Retro-Schematics/Apple/Apple II/Apple II - Video Generator Pt 2 of 2 (Rev RFI).kicad_sch

## KiCad design Apple/Apple II/Apple II - Video Generator Pt 2 of 2 (Rev RFI).kicad_sch (2022-07-17)

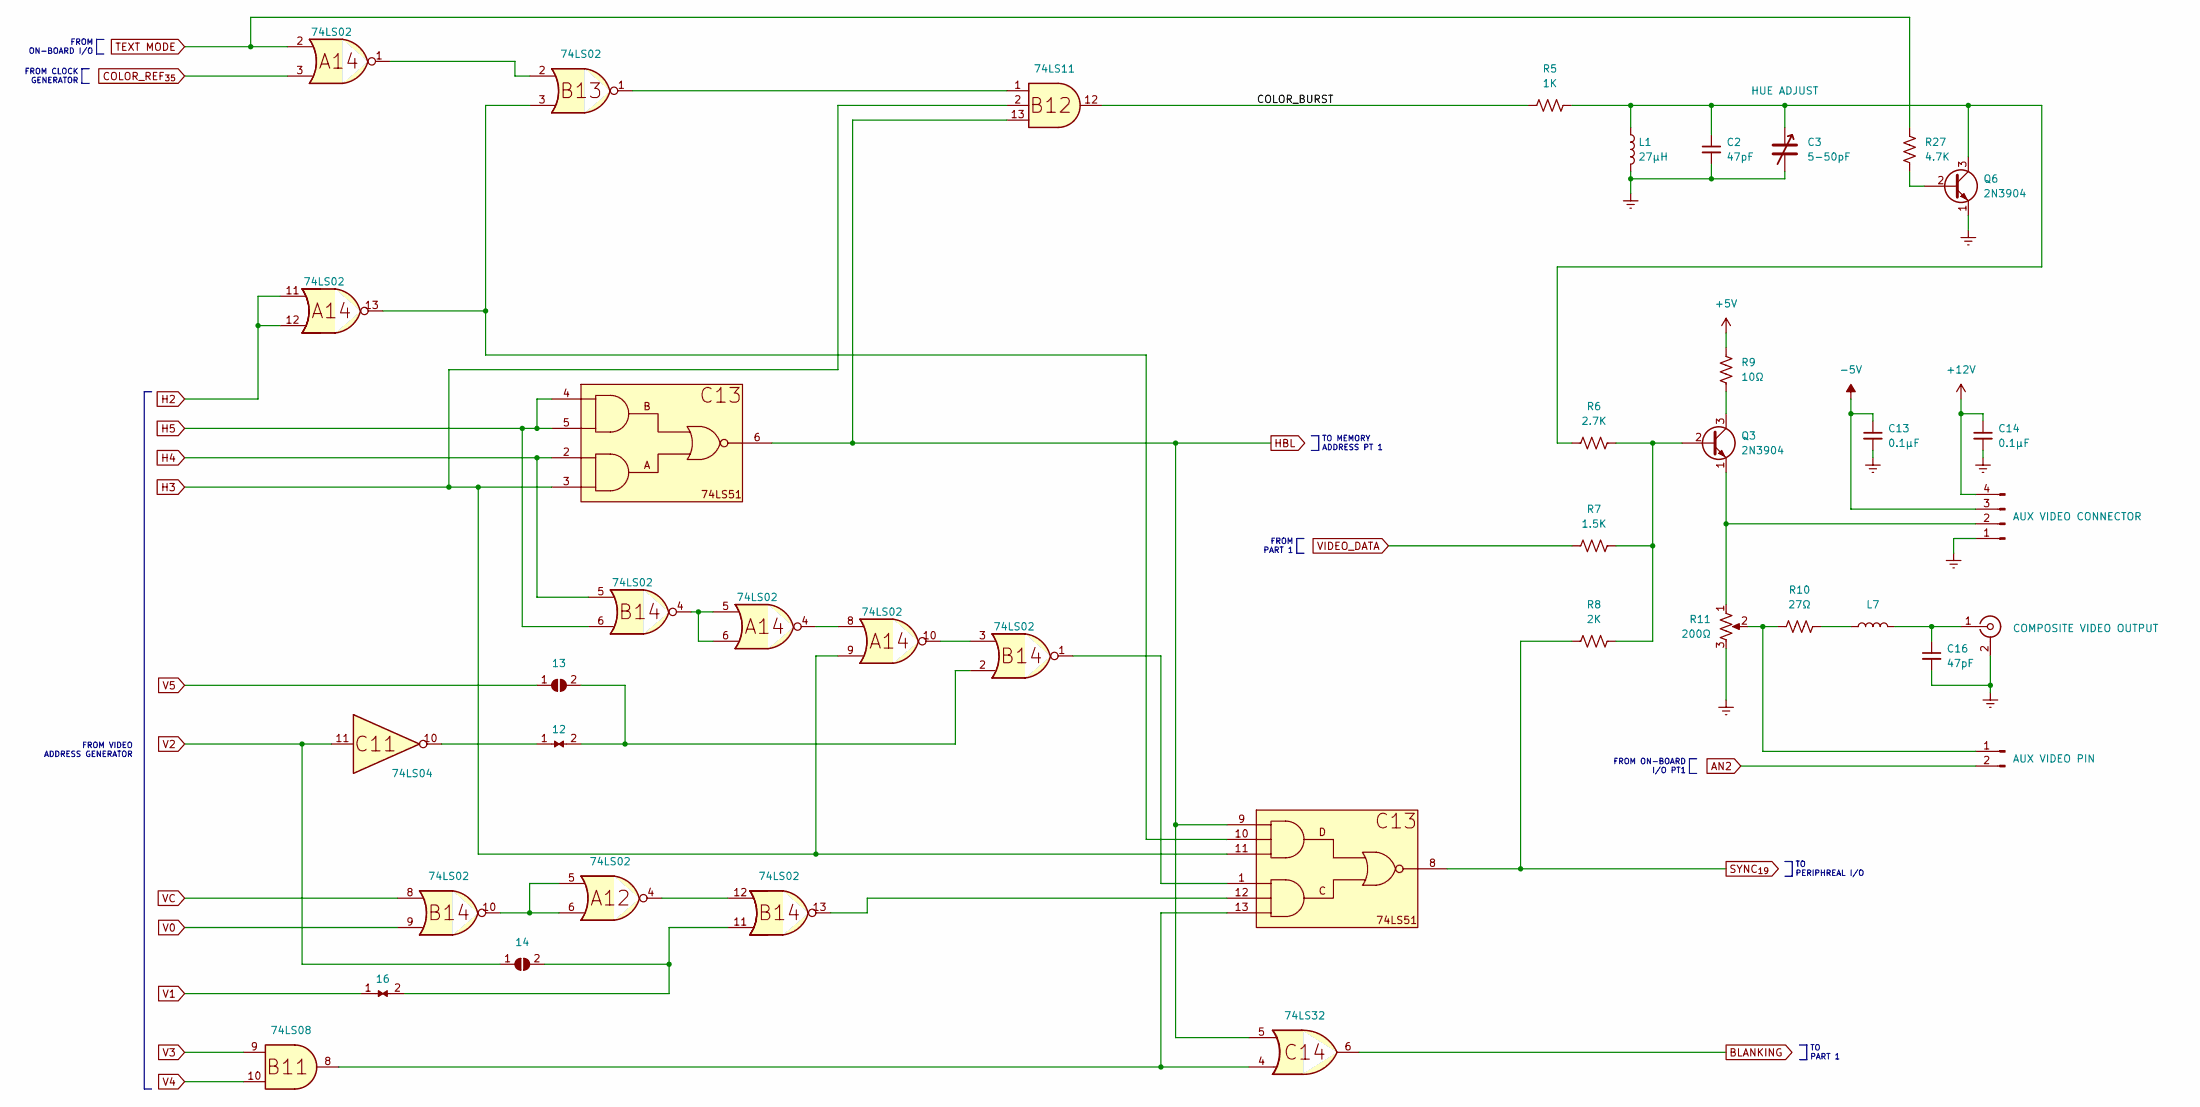
[picture p74: schematic Apple II - Video Generator Pt 2 of 2 (Rev RFI).kicad_sch]

Parts:
A14: 74LS02
C2, C16: 47pF
C3: 5-50pF
C13, C14: 0.1µF
J250: AUX VIDEO PIN
L1, L7: 27µH
Q3, Q6: 2N3904; TO-92_Inline
R5: 1K
R6: 2.7K
R7: 1.5K
R8: 2K
R9: 10Ω
R10: 27Ω
R11: 200Ω
R27: 4.7K

Connections:
AN2: J250.2
COLOR_BURST: R5.1
H3: A14.9
unnamed: A14.4, A14.8
unnamed: A14.5, A14.6
unnamed: C2.1, C3.1, L1.1, Q6.3 (C), R5.2, R6.1
unnamed: C2.2, C3.2, L1.2
unnamed: C16.1, L7.2
unnamed: J250.1, R10.1, R11.2
unnamed: L7.1, R10.2
unnamed: Q3.1 (E), R11.1
unnamed: Q3.2 (B), R6.2, R7.2, R8.2
unnamed: Q3.3 (C), R9.1
unnamed: Q6.2 (B), R27.2
SYNC_{19}: R8.1
TEXT MODE: R27.1
VIDEO_DATA: R7.1

Notes on the sheet:
TO PERIPHREAL I/O
FROM PART 1
FROM VIDEO ADDRESS GENERATOR
FROM ON-BOARD I/O PT1
TO PART 1
TO MEMORY ADDRESS PT 1
FROM ON-BOARD I/O
FROM CLOCK GENERATOR
