omega9380/Retro-Schematics/Commodore/Commodore 64/Commodore 64.kicad_sch

## KiCad design Commodore/Commodore 64/Commodore 64.kicad_sch (2022-07-05)

Schematic: Commodore 64.kicad_sch

Parts:
C2, C3, C4, C5, C6, C7, C9, C12, C16, C18, C22, C25, C26, C27, C28, C29, C30, C31, C32, C33, C39, C40, C41, C42, C43, C44, C45, C47, C49, C50, C51, C52, C53, C54, C56, C60, C68, C74, C82, C84, C96, C101, C105: .1
C8, C13, C14, C15, C17, C24, C34, C62, C94, C108: 10 25V
C10, C11: 470pF
C23: 360pF
C36: 20pF 50V
C37: 1000 pF
C38: 51pF
C48, C93: 1800pF
C70, C107: NOTE 2
C83: 82pF 50V ±5%
C85: .47
C86: NOTE 8
C203, C205: 220pF
C204: 150pF
CN1: KEYBOARD
CN2: USER PORT
CN3: CASSETTE
CN4: SERIAL BUS
CN5: AUDIO/VIDEO (8PIN FEMALE DIN)
CN6: CARTRIDGE/EXPANSION (44PIN FEMALE)
CN8: CONTROL PORT 2
CN9: CONTROL PORT 1
CR2: 1.5V IN755
CR100, CR101, CR102, CR103: D_Small
E1: JUMPER_SELECT
FB1, FB2, FB4, FB5, FB10, FB11, FB12, FB13, FB14, FB15, FB16, FB17, FB18, FB22, FB29, FB87, FB88, FB89: FerriteBead_Small
J99: RF_OUT
Q1, Q2, Q7, Q8: 2SC1815; TO-92_Inline
Q3: TP29B/2SD880; TO-92_Inline
R2, R51: 1.5K
R3, R7: 10K
R4, R6, R16, R28, R29, R30, R36, R38: 1K
R17: 2.7K
R19: 15K
R26, R52, R53: NOTE 2
R27: 500
R31: 180Ω
R33, R34: 47K
R35: 470K
R41, R50: 1M
R42: 82Ω
R45: 3.3K
R101: NOTE 8
RF1: RF_MODULATOR
RP1, RP2: 33Ω
RP3, RP4: 3.3K
U1: 6526_CIA_U1; DIP-40_W15.24mm_LongPads
U2: 6526_CIA_U2; DIP-40_W15.24mm_LongPads
U3: 2364_BASIC_ROM_U3; DIP-24_W7.62mm_LongPads
U4: 2364_KERNAL_ROM_U4; DIP-24_W7.62mm_LongPads
U5: 2332_CHAR_ROM_U5; DIP-24_W7.62mm_LongPads
U6: 2114-30L_U6; DIP-18_W7.62mm_LongPads
U7: 6510_MPU_U7; DIP-40_W15.24mm_LongPads
U8: 7406
U12,U24,U11,U23,U10,U22,U9,U21: 4146_U9..U12,U21..U24
U13: 74LS257_U13
U14: 74LS258_U14
U15: 74LS139_U15
U16: 4066_U16; DIP-14_W7.62mm_LongPads
U17: 872S100_PLA_U17; DIP-28_W15.24mm_LongPads
U18: 6581_SID_U18; DIP-28_W15.24mm_LongPads
U19: 6567_U19; DIP-40_W15.24mm_LongPads
U20: LM556_U20
U25: 74LS257_U25
U26: 74LS373_U26
U27: 74LS08
U28: 4066; DIP-14_W7.62mm_LongPads
U29: 74LS74_U29
U30: 74LS193_U30
U31: 74LS629N
U32: MC4044_U32
Y1: NOTE 2

Connections:
A0: CN6.Y (A0), U1.38 (RS0), U2.38 (RS0), U3.8 (A0), U4.8 (A0), U5.8 (A0), U6.5 (A0), U7.7 (A0), U18.9 (A0), U25.13 (B_{3}), U26.6 (Q0)
A1: CN6.X (A1), U1.37 (RS1), U2.37 (RS1), U3.7 (A1), U4.7 (A1), U5.7 (A1), U6.6 (A1), U7.8 (A1), U18.10 (A1), U25.10 (B_{2}), U26.12 (Q1)
A2: CN6.W (A2), U1.36 (RS2), U2.36 (RS2), U3.6 (A2), U4.6 (A2), U5.6 (A2), U6.7 (A2), U7.9 (A2), U18.11 (A2), U25.6 (B_{1}), U26.9 (Q2)
A3: CN6.V (A3), U1.35 (RS3), U2.35 (RS3), U3.5 (A3), U4.5 (A3), U5.5 (A3), U6.4 (A3), U7.10 (A3), U18.12 (A3), U25.3 (B_{0}), U26.15 (Q3)
A4: CN6.U (A4), U3.4 (A4), U4.4 (A4), U5.4 (A4), U6.3 (A4), U7.11 (A4), U13.13 (B_{3}), U18.13 (A4), U26.16 (Q4)
A5: CN6.T (A5), U3.3 (A5), U4.3 (A5), U5.3 (A5), U6.2 (A5), U7.12 (A5), U13.6 (B_{1}), U26.19 (Q5)
A6: CN6.S (A6), U3.2 (A6), U4.2 (A6), U5.2 (A6), U6.1 (A6), U7.13 (A6), U13.3 (B_{0}), U26.5 (Q6)
A7: CN6.R (A7), U3.1 (A7), U4.1 (A7), U5.1 (A7), U6.17 (A7), U7.14 (A7), U13.10 (B_{2}), U26.2 (Q7)
A8: CN6.P (A8), U3.23 (A8), U4.23 (A8), U5.23 (A8), U6.16 (A8), U7.15 (A8), U15.14 (A0), U19.32 (A8), U25.14 (A_{3})
A9: CN6.N (A9), U3.22 (A9), U4.22 (A9), U5.22 (A9), U6.15 (A9), U7.16 (A9), U15.13 (A1), U19.33 (A9), U25.11 (A_{2})
A10: CN6.M (A10), U3.19 (A10), U4.19 (A10), U5.19 (A10), U7.17 (A10), U15.2 (A0), U19.34 (A10), U25.5 (A_{1})
A11: CN6.L (A11), U3.18 (A11), U4.18 (A11), U5.18 (A11), U7.18 (A11), U15.3 (A1), U19.23 (A11), U25.2 (A_{0})
A12: CN6.K (A12), RP4.8, U3.21 (A12), U4.21 (A12), U7.19 (A12), U13.14 (A_{3}), U17.27 (I8)
A13: CN6.J (A13), RP4.6, U7.20 (A13), U13.5 (A_{1}), U17.2 (I7)
A14: CN6.H (A14), RP4.5, U7.22 (A14), U13.2 (A_{0}), U17.3 (I6)
A15: CN6.F (A15), RP4.4, U7.23 (A15), U13.11 (A_{2}), U17.4 (I5)
ATN: CN2.9 (ATN), CN4.3 (ATN), FB87.1, FB87.2, R28.2, U8.12
ATN_OUT: U2.5 (PA3), U8.13
BA: CN6.12 (BA), U17.26 (I9), U19.12 (BA), U27.9
BTN_{A}/LP: CN1.8 (ROW_{4}), CN9.6 (BTN_{A}/LP), U1.14 (PB4), U19.9 (LP)
BTN_{B}: CN1.16 (COL_{4}), CN8.6 (BTN_{B}), U1.6 (PA4)
CAEC: U7.5 (AEC), U27.6
CASS MOTOR: CN3.3 (MOTOR), CN3.C (MOTOR), FB2.1, R4.1, U7.24 (P5)
CASS RD: CN3.4 (RD), CN3.D (RD), CN4.1 (~SRQIN), RP3.4, U1.24 (~FLAG)
CASS SENSE: CN3.6 (SENSE), CN3.F (SENSE), U7.25 (P4)
CASS WRT: CN3.5 (WRT), CN3.E (WRT), FB1.1, FB1.2, U7.26 (P3)
CLK: CN4.4 (CLK), CR102.2 (A), CR103.1 (K), FB89.1, FB89.2, R30.2, U2.8 (PA6), U8.10
CLK_OUT: U2.6 (PA4), U8.11
CNT1: CN2.4 (CNT1), RP3.5, U1.40 (CNT)
CNT2: CN2.6 (CNT2), RP3.7, U2.40 (CNT)
COL_{0}: CN1.13 (COL_{0}), CN8.1 (JOY_{B}0), U1.2 (PA0)
COL_{1}: CN1.19 (COL_{1}), CN8.2 (JOY_{B}1), U1.3 (PA1)
COL_{2}: CN1.18 (COL_{2}), CN8.3 (JOY_{B}2), U1.4 (PA2)
COL_{3}: CN1.17 (COL_{3}), CN8.4 (JOY_{B}3), U1.5 (PA3)
COL_{5}: CN1.15 (COL_{5}), U1.7 (PA5)
COL_{6}: CN1.14 (COL_{6}), U1.8 (PA6), U28.6 (E_{2}), U28.12 (E_{3})
COL_{7}: CN1.20 (COL_{7}), U1.9 (PA7), U28.5 (E_{1}), U28.13 (E_{0})
D0: CN6.21 (D0), U1.33 (DB0), U2.33 (DB0), U3.9 (D0), U4.9 (D0), U5.9 (D0), U7.37 (D0), U12,U24,U11,U23,U10,U22,U9,U21.2 (D_{I}), U12,U24,U11,U23,U10,U22,U9,U21.14 (D_{O}), U16.11 (Y_{3}), U18.15 (D0), U19.7 (D0)
D1: CN6.20 (D1), U1.32 (DB1), U2.32 (DB1), U3.10 (D1), U4.10 (D1), U5.10 (D1), U7.36 (D1), U12,U24,U11,U23,U10,U22,U9,U21.2 (D_{I}), U12,U24,U11,U23,U10,U22,U9,U21.14 (D_{O}), U16.8 (Y_{2}), U18.16 (D1), U19.6 (D1)
D2: CN6.19 (D2), U1.31 (DB2), U2.31 (DB2), U3.11 (D2), U4.11 (D2), U5.11 (D2), U7.35 (D2), U12,U24,U11,U23,U10,U22,U9,U21.2 (D_{I}), U12,U24,U11,U23,U10,U22,U9,U21.14 (D_{O}), U16.4 (Y_{1}), U18.17 (D2), U19.5 (D2)
D3: CN6.18 (D3), U1.30 (DB3), U2.30 (DB3), U3.13 (D3), U4.13 (D3), U5.13 (D3), U7.34 (D3), U12,U24,U11,U23,U10,U22,U9,U21.2 (D_{I}), U12,U24,U11,U23,U10,U22,U9,U21.14 (D_{O}), U16.1 (Y_{0}), U18.18 (D3), U19.4 (D3)
D4: CN6.17 (D4), U1.29 (DB4), U2.29 (DB4), U3.14 (D4), U4.14 (D4), U5.14 (D4), U7.33 (D4), U12,U24,U11,U23,U10,U22,U9,U21.2 (D_{I}), U12,U24,U11,U23,U10,U22,U9,U21.14 (D_{O}), U18.19 (D4), U19.3 (D4)
D5: CN6.16 (D5), U1.28 (DB5), U2.28 (DB5), U3.15 (D5), U4.15 (D5), U5.15 (D5), U7.32 (D5), U12,U24,U11,U23,U10,U22,U9,U21.2 (D_{I}), U12,U24,U11,U23,U10,U22,U9,U21.14 (D_{O}), U18.20 (D5), U19.2 (D5)
D6: CN6.15 (D6), U1.27 (DB6), U2.27 (DB6), U3.16 (D6), U4.16 (D6), U5.16 (D6), U7.31 (D6), U12,U24,U11,U23,U10,U22,U9,U21.2 (D_{I}), U12,U24,U11,U23,U10,U22,U9,U21.14 (D_{O}), U18.21 (D6), U19.1 (D6)
D7: CN6.14 (D7), U1.26 (DB7), U2.26 (DB7), U3.17 (D7), U4.17 (D7), U5.17 (D7), U7.30 (D7), U12,U24,U11,U23,U10,U22,U9,U21.2 (D_{I}), U12,U24,U11,U23,U10,U22,U9,U21.14 (D_{O}), U18.22 (D7), U19.39 (D7)
DATA: CN4.5 (DATA), CR100.2 (A), CR101.1 (K), FB88.1, FB88.2, R29.2, U2.9 (PA7), U8.2
DATA_OUT: U2.7 (PA5), U8.1
DOT_CLOCK: C36.2, CN6.6 (DOT_CLOCK), FB17.2, U19.22 (ɸ_{IN})
GR/~W: U6.10 (~WE), U17.13 (F4)
JOY_{A}0: CN1.12 (ROW_{0}), CN9.1 (JOY_{A}0), U1.10 (PB0)
JOY_{A}1: CN1.11 (ROW_{1}), CN9.2 (JOY_{A}1), U1.11 (PB1)
JOY_{A}2: CN1.10 (ROW_{2}), CN9.3 (JOY_{A}2), U1.12 (PB2)
JOY_{A}3: CN1.5 (ROW_{3}), CN9.4 (JOY_{A}3), U1.13 (PB3)
unnamed: C2.2, U1.20 (VCC)
unnamed: C3.2, U2.20 (VCC)
unnamed: C4.1, C5.1, C6.1, U3.11 (D2), U4.11 (D2), U5.11 (D2)
unnamed: C4.2, U3.24 (VCC)
unnamed: C5.2, U4.24 (VCC)
unnamed: C6.2, U5.21 (CS_{2}), U5.24 (VCC)
unnamed: C7.2, U6.18 (VCC)
unnamed: C8.1, C9.2, U7.6 (VCC)
unnamed: C8.2, C9.1
unnamed: C10.1, U18.2 (CAP_{1B})
unnamed: C10.2, U18.1 (CAP_{1A})
unnamed: C11.1, U18.4 (CAP_{2B})
unnamed: C11.2, U18.3 (CAP_{2A})
unnamed: C12.1, U18.26 (EXT_{IN})
unnamed: C12.2, CN5.5 (AUD_IN)
unnamed: C13.1, C205.2, Q8.1 (E), R38.1
unnamed: C13.2, CN5.3 (AUD_OUT), RF1.4 (AUDIO)
unnamed: C14.1, C25.2, C26.2, C27.2, C28.2, C40.2, C41.2, C42.2, C43.2, U12,U24,U11,U23,U10,U22,U9,U21.8 (VCC)
unnamed: C14.2, C25.1, C26.1, C27.1, C28.1, C40.1, C41.1, C42.1, C43.1
unnamed: C15.1, C16.2, RF1.1 (+B)
unnamed: C15.2, C16.1
unnamed: C17.1, CN6.1 (GND), CN6.22 (GND), CN6.A (GND), CN6.Z (GND)
unnamed: C17.2, CN6.2 (+5V), CN6.3 (+5V), RP4.1
unnamed: C18.1, CR2.1 (K), Q1.3 (B), Q2.2 (C), R2.2
unnamed: C18.2, Q1.2 (C), Q3.2 (C), R2.1
unnamed: C22.1, R33.1, R41.1, RP3.1, U8.14, U20.4 (RST_{1})
unnamed: C22.2, U8.7
unnamed: C23.1, R33.2, U20.1 (DIS_{1}), U20.2 (THR_{1})
unnamed: C24.1, R34.2, U20.12 (THR_{2}), U20.13 (DIS_{2})
unnamed: C29.1, U13.16 (VCC)
unnamed: C30.1, U14.8 (GND)
unnamed: C30.2, U14.16 (VCC)
unnamed: C31.1, U15.16 (VCC)
unnamed: C32.1, U16.7 (GND)
unnamed: C32.2, U16.14 (VDD)
unnamed: C33.1, U17.28 (VCC)
unnamed: C33.2, U17.14 (GND), U17.19 (~OE)
unnamed: C34.1, C49.2, FB10.2
unnamed: C34.2, C49.1, C50.1
unnamed: C37.2, Q8.3 (B), R7.2
unnamed: C38.2, R35.1, U20.6 (TRIG_{1})
unnamed: C39.2, U20.10 (RST_{2}), U20.14 (VCC)
unnamed: C44.1, U25.16 (VCC)
unnamed: C45.1, U12,U24,U11,U23,U10,U22,U9,U21.16 (VSS), U26.10 (GND)
unnamed: C45.2, U26.20 (VCC)
unnamed: C47.1, U28.14 (VDD)
unnamed: C47.2, U28.7 (GND)
unnamed: C48.1, C93.2
unnamed: C50.2, FB10.1, U18.25 (VCC)
unnamed: C51.1, C52.1, C62.2
unnamed: C51.2, FB11.1, U18.28 (VDD)
unnamed: C52.2, C62.1, FB11.2, Q8.2 (C)
unnamed: C53.1, C54.1, C94.1
unnamed: C53.2, C94.2, FB12.1
unnamed: C54.2, FB12.2, U19.13 (VDD)
unnamed: C56.1, U32.7
unnamed: C56.2, U32.14
unnamed: C68.2, R26.1, U31.16 (VCC)
unnamed: C70.1, U31.13 (CX2_{2})
unnamed: C70.2, Y1.3
unnamed: C74.2, U30.15 (A), U30.16 (VCC)
unnamed: C82.2, U29.14 (VCC)
unnamed: C83.2, U30.11 (~LOAD), U30.12 (~CO)
unnamed: C84.2, Q7.2 (C), R16.1
unnamed: C85.1, R17.1
unnamed: C85.2, Q7.3 (B), R19.2
unnamed: C86.1, U31.5 (CX2_{1})
unnamed: C86.2, R101.2, U31.4 (CX1_{1})
unnamed: C96.1, CN2.1 (GND), CN2.12 (GND), CN2.A (GND), CN2.N (GND)
unnamed: C96.2, CN2.2 (+5V)
unnamed: C60.1, C101.1
unnamed: C60.2, C101.2, FB22.1, U19.40 (VCC)
unnamed: C105.2, R50.2, U20.8 (TRIG_{2})
unnamed: C107.1, R26.2, U31.15 (VCC)
unnamed: C108.1, R27.2, U31.1 (FC_{2})
unnamed: C108.2, R52.2
unnamed: C37.1, C205.1, R6.2, R38.2
unnamed: CN3.1 (GND), CN3.A (GND)
unnamed: CN3.2 (+5V), CN3.B (+5V)
unnamed: CN5.1 (LUM), RF1.6 (SYNC+LUM_{OUT})
unnamed: CN5.4 (COMP_VID), RF1.5 (COMP_{OUT})
unnamed: CN5.6 (COLOR), RF1.7 (COLOR_{OUT})
unnamed: CN8.7 (+5V), CN9.7 (+5V), FB18.2
unnamed: CR2.2 (A), Q2.1 (E), R3.2
unnamed: CR100.1 (K), CR102.1 (K), R28.1, R29.1, R30.1
unnamed: CR101.2 (A), CR103.2 (A)
unnamed: E1.1 (A), RF1.8 (ICS)
unnamed: E1., U29.4 (~PRE_{1}), U30.1 (B), U30.10 (C)
unnamed: FB2.2, Q3.1 (E)
unnamed: FB13.1, R6.1, U18.27 (AUD_{OUT})
unnamed: FB13.2, R7.1
unnamed: FB14.1, U19.14 (COLOR)
unnamed: FB14.2, RF1.3 (COLOR_{IN})
unnamed: FB15.1, U19.15 (SYNC/LUM)
unnamed: FB15.2, RF1.2 (SYNC+LUM_{IN})
unnamed: FB16.1, U31.10 (Y_{2})
unnamed: FB17.1, U31.7 (Y_{1})
unnamed: FB29.1, U19.17 (ɸ0_{OUT})
unnamed: J99.1 (In), RF1.9 (RF_OUT)
unnamed: Q1.1 (E), Q3.3 (B)
unnamed: Q2.3 (B), R3.1, R4.2
unnamed: Q7.1 (E), U32.9
unnamed: R16.2, R17.2, U31.2 (FC_{1}), U32.8
unnamed: R19.1, U32.5 (VCC), U32.10
unnamed: R27.1, R52.1
unnamed: R27.3, R53.2
unnamed: R45.2, RP4.1
unnamed: R51.1, RP4.1
unnamed: RP1.1, U13.4 (Y_{0})
unnamed: RP1.2, U12,U24,U11,U23,U10,U22,U9,U21.13 (MA6)
unnamed: RP1.3, U13.12 (Y_{3})
unnamed: RP1.4, U12,U24,U11,U23,U10,U22,U9,U21.11 (MA4)
unnamed: RP1.5, U13.7 (Y_{1})
unnamed: RP1.6, U12,U24,U11,U23,U10,U22,U9,U21.10 (MA5)
unnamed: RP1.7, U13.9 (Y_{2})
unnamed: RP1.8, U12,U24,U11,U23,U10,U22,U9,U21.9 (MA7)
unnamed: RP2.1, U25.4 (Y_{0})
unnamed: RP2.2, U12,U24,U11,U23,U10,U22,U9,U21.12 (MA3)
unnamed: RP2.3, U25.12 (Y_{3})
unnamed: RP2.4, U12,U24,U11,U23,U10,U22,U9,U21.5 (MA0)
unnamed: RP2.5, U25.7 (Y_{1})
unnamed: RP2.6, U12,U24,U11,U23,U10,U22,U9,U21.6 (MA2)
unnamed: RP2.7, U25.9 (Y_{2})
unnamed: RP2.8, U12,U24,U11,U23,U10,U22,U9,U21.7 (MA1)
unnamed: U1.19 (TOD), U2.19 (TOD)
unnamed: U12,U24,U11,U23,U10,U22,U9,U21.3 (~WE), U18.7 (R/~W), U19.11 (R/~W)
unnamed: U12,U24,U11,U23,U10,U22,U9,U21.5 (MA0), U19.24 (A0/A8), U26.7 (D0)
unnamed: U12,U24,U11,U23,U10,U22,U9,U21.6 (MA2), U19.26 (A2/A10), U26.8 (D2)
unnamed: U12,U24,U11,U23,U10,U22,U9,U21.7 (MA1), U19.25 (A1/A9), U26.13 (D1)
unnamed: U12,U24,U11,U23,U10,U22,U9,U21.9 (MA7), U14.7 (~Y_{1}), U26.3 (D7)
unnamed: U12,U24,U11,U23,U10,U22,U9,U21.12 (MA3), U19.27 (A3/A11), U26.14 (D3)
unnamed: U12,U24,U11,U23,U10,U22,U9,U21.13 (MA6), U14.4 (~Y_{0}), U26.4 (D6)
unnamed: U14.6 (B_{1}), U14.9 (~Y_{3})
unnamed: U14.3 (B_{0}), U14.12 (~Y_{2})
unnamed: U6.11 (D3), U16.2 (Z_{0}), U19.35 (D11)
unnamed: U6.12 (D2), U16.3 (Z_{1}), U19.36 (D10)
unnamed: U6.13 (D1), U16.9 (Z_{2}), U19.37 (D9)
unnamed: U6.14 (D0), U16.10 (Z_{3}), U19.38 (D8)
unnamed: U8.5, U20.5 (OUT_{1})
unnamed: U8.9, U20.9 (OUT_{2})
unnamed: U6.8 (~CS), U27.11
unnamed: U29.1 (~R_{1}), U29.2 (D_{1}), U29.3 (C_{1}), U29.7 (GND)
unnamed: U29.5 (Q_{1}), U30.9 (D)
unnamed: U29.9 (Q_{2}), U32.1
unnamed: U29.10 (~PRE_{2}), U29.13 (~R_{2})
unnamed: U29.11 (C_{2}), U30.6 (QC)
unnamed: U29.8 (~Q_{2}), U29.12 (D_{2})
unnamed: U30.8 (GND), U30.14 (CLR)
unnamed: U31.3 (RNG_{1}), U31.6 (EN_{1})
unnamed: U31.8 (GND), U31.9 (GND), U31.11 (EN_{2}), U31.14 (RNG_{2})
unnamed: U31.12 (CX2_{2}), Y1.1
unnamed: U32.2, U32.11
unnamed: U32.4, U32.13
PA2: CN2.M (PA2), U2.4 (PA2)
PB0: CN2.C (PB0), U2.10 (PB0)
PB1: CN2.D (PB1), U2.11 (PB1)
PB2: CN2.E (PB2), U2.12 (PB2)
PB3: CN2.F (PB3), U2.13 (PB3)
PB4: CN2.H (PB4), U2.14 (PB4)
PB5: CN2.J (PB5), U2.15 (PB5)
PB6: CN2.K (PB6), U2.16 (PB6)
PB7: CN2.L (PB7), U2.17 (PB7)
POT_{A}X: CN9.9 (POT_{A}X), U28.8 (Y_{2})
POT_{A}Y: CN9.5 (POT_{A}Y), U28.11 (Y_{3})
POT_{B}X: CN8.9 (POT_{B}X), U28.1 (Y_{0})
POT_{B}Y: CN8.5 (POT_{B}Y), U28.4 (Y_{1})
POT_{X}: C48.2, U18.23 (POT_{X}), U28.2 (Z_{0}), U28.9 (Z_{2})
POT_{Y}: C93.1, U18.24 (POT_{Y}), U28.3 (Z_{1}), U28.10 (Z_{3})
RDY: U7.2 (RDY), U27.8
ROW_{5}: CN1.7 (ROW_{5}), U1.15 (PB5)
ROW_{6}: CN1.6 (ROW_{6}), U1.16 (PB6)
ROW_{7}: CN1.9 (ROW_{7}), U1.17 (PB7)
R/~W: CN6.5 (R/~W), R51.2, U1.22 (R/~W), U2.22 (R/~W), U7.38 (R/~W), U17.24 (I11)
SP1: CN2.5 (SP1), RP3.6, U1.39 (SP)
SP2: CN2.7 (SP2), RP3.8, U2.39 (SP)
VA6: U14.13 (B_{2}), U14.14 (A_{2}), U19.30 (A6)
VA7: U14.10 (B_{3}), U14.11 (A_{3}), U19.31 (A7)
VA12: U12,U24,U11,U23,U10,U22,U9,U21.11 (MA4), U17.20 (I15), U19.28 (A4/A12), U26.17 (D4)
VA13: U12,U24,U11,U23,U10,U22,U9,U21.10 (MA5), U17.21 (I14), U19.29 (A5/A13), U26.18 (D5)
~AEC: R31.2, U8.3, U8.4, U13.15 (~OE), U14.15 (~OE), U16.5 (E_{1}), U16.6 (E_{2}), U16.12 (E_{3}), U16.13 (E_{0}), U17.25 (I10), U19.16 (AEC), U25.15 (~OE), U26.1 (OE), U27.5, U27.12
~BASIC: U3.20 (~CS), U17.17 (F1)
~CASRAM: C204.2, R42.1, R42.2, U12,U24,U11,U23,U10,U22,U9,U21.15 (~CAS), U17.18 (F0)
~CAS: C203.2, U13.1 (~SELA), U14.1 (~SELA), U17.9 (I0), U19.19 (~CAS), U25.1 (~SELA)
~CHAREN: RP4.2, U7.27 (P2), U17.6 (I3)
~CHAROM: U5.20 (~CS_{1}), U17.15 (F3)
~CIA1: U1.23 (~CS), U15.12 (O0)
~CIA2: U2.23 (~CS), U15.11 (O1)
~CLAS: U15.7 (O3), U15.15 (E)
~COLOR: U15.6 (O2), U27.13
~{DMA: CN6.13 (~DMA), RP4.10, U27.4, U27.10
~EXROM: CN6.9 (~EXROM), RP4.9, U17.23 (I12)
~FLAG2: CN2.B (~FLAG2), RP3.2, U2.24 (~FLAG)
~GAME: CN6.8 (~GAME), RP4.7, U17.22 (I13)
~HIRAM: RP4.3, U7.28 (P1), U17.7 (I2)
~IRQ: CN6.4 (~IRQ), RP4.3, U1.21 (~IRQ), U7.3 (~IRQ), U19.8 (~IRQ)
~I/O_{1}: CN6.7 (~I/O_{1}), U15.10 (O2)
~I/O_{2}: CN6.10 (~I/O_{2}), U15.9 (O3)
~I/O: U15.1 (E), U17.12 (F5)
~KERNAL: U4.20 (~CS), U17.16 (F2)
~LORAM: R45.1, U7.29 (P0), U17.8 (I1)
~NMI: CN6.D (~NMI), RP3.3, U2.21 (~IRQ), U7.4 (~NMI), U8.6
~PC2: CN2.8 (~PC2), U2.18 (~PC)
~RAS: U12,U24,U11,U23,U10,U22,U9,U21.4 (~RAS), U19.18 (~RAS), U26.11 (STB)
~RESET: CN2.3 (~RESET), CN4.6 (~RESET), CN6.C (~RESET), FB4.1, FB4.2, R36.2, U1.34 (~RES), U2.34 (~RES), U7.40 (~RES), U8.8, U18.5 (~RES)
~RESTORE: C38.1, CN1.3 (~RESTORE), R41.2
~ROMH: CN6.11 (~ROML), CN6.B (~ROMH), U17.10 (F7), U17.11 (F6)
~SID: U15.5 (O1), U18.8 (~CS)
~VA14: U2.2 (PA0), U14.2 (A_{0}), U17.5 (I4)
~VA15: U2.3 (PA1), U14.5 (A_{1})
~VIC: U15.4 (O0), U19.10 (~CS)
ɸ0: FB29.2, U7.1 (ɸ0), U32.3
ɸ2: CN6.E (ɸ2), FB5.1, FB5.2, U1.25 (ɸ2), U2.25 (ɸ2), U7.39 (ɸ2), U18.6 (ɸ2)
ɸCOLOR: FB16.2, U19.21 (ɸCOLOR), U30.5 (CNT_{UP})

Notes on the sheet:
(8000-9FFF)
CAN
RP3 3.3K
(8.18MHz - NTSC) (7.88MHz - PAL)
JUMPER SELECT
(1.02MHz - NTSC) (0.98MHz - PAL)
RP4 3.3K
SHEET 1
(24-PIN MALE EDGE)
(A000-BFFF OR E000-FFFF)
RP1 33Ω
(14.31818MHz - NTSC) (17.734472MHz - PAL)
(6-PIN FEMALE DIN)
U32 - MC4044
(DF00-DFFF:DISK)
(20-PIN MALE)
(DE00-DEFF:Z80 ON)
(MALE DB9)
UNREG
SEE NOTE 5
(6-PIN MALE EDGE)
RP2 33Ω
(14.31818 MHz - NTSC) (17.734472 MHz - PAL)
