omega9380/Retro-Schematics/Commodore/Commodore 64/Commodore 64 - Schematic 251138 for PCB Assy 250407/Commodore 64 - RF Modulator for Schematic 2251138.kicad_sch

## KiCad design Commodore/Commodore 64/Commodore 64 - Schematic 251138 for PCB Assy 250407/Commodore 64 - RF Modulator for Schematic 2251138.kicad_sch (2022-07-06)

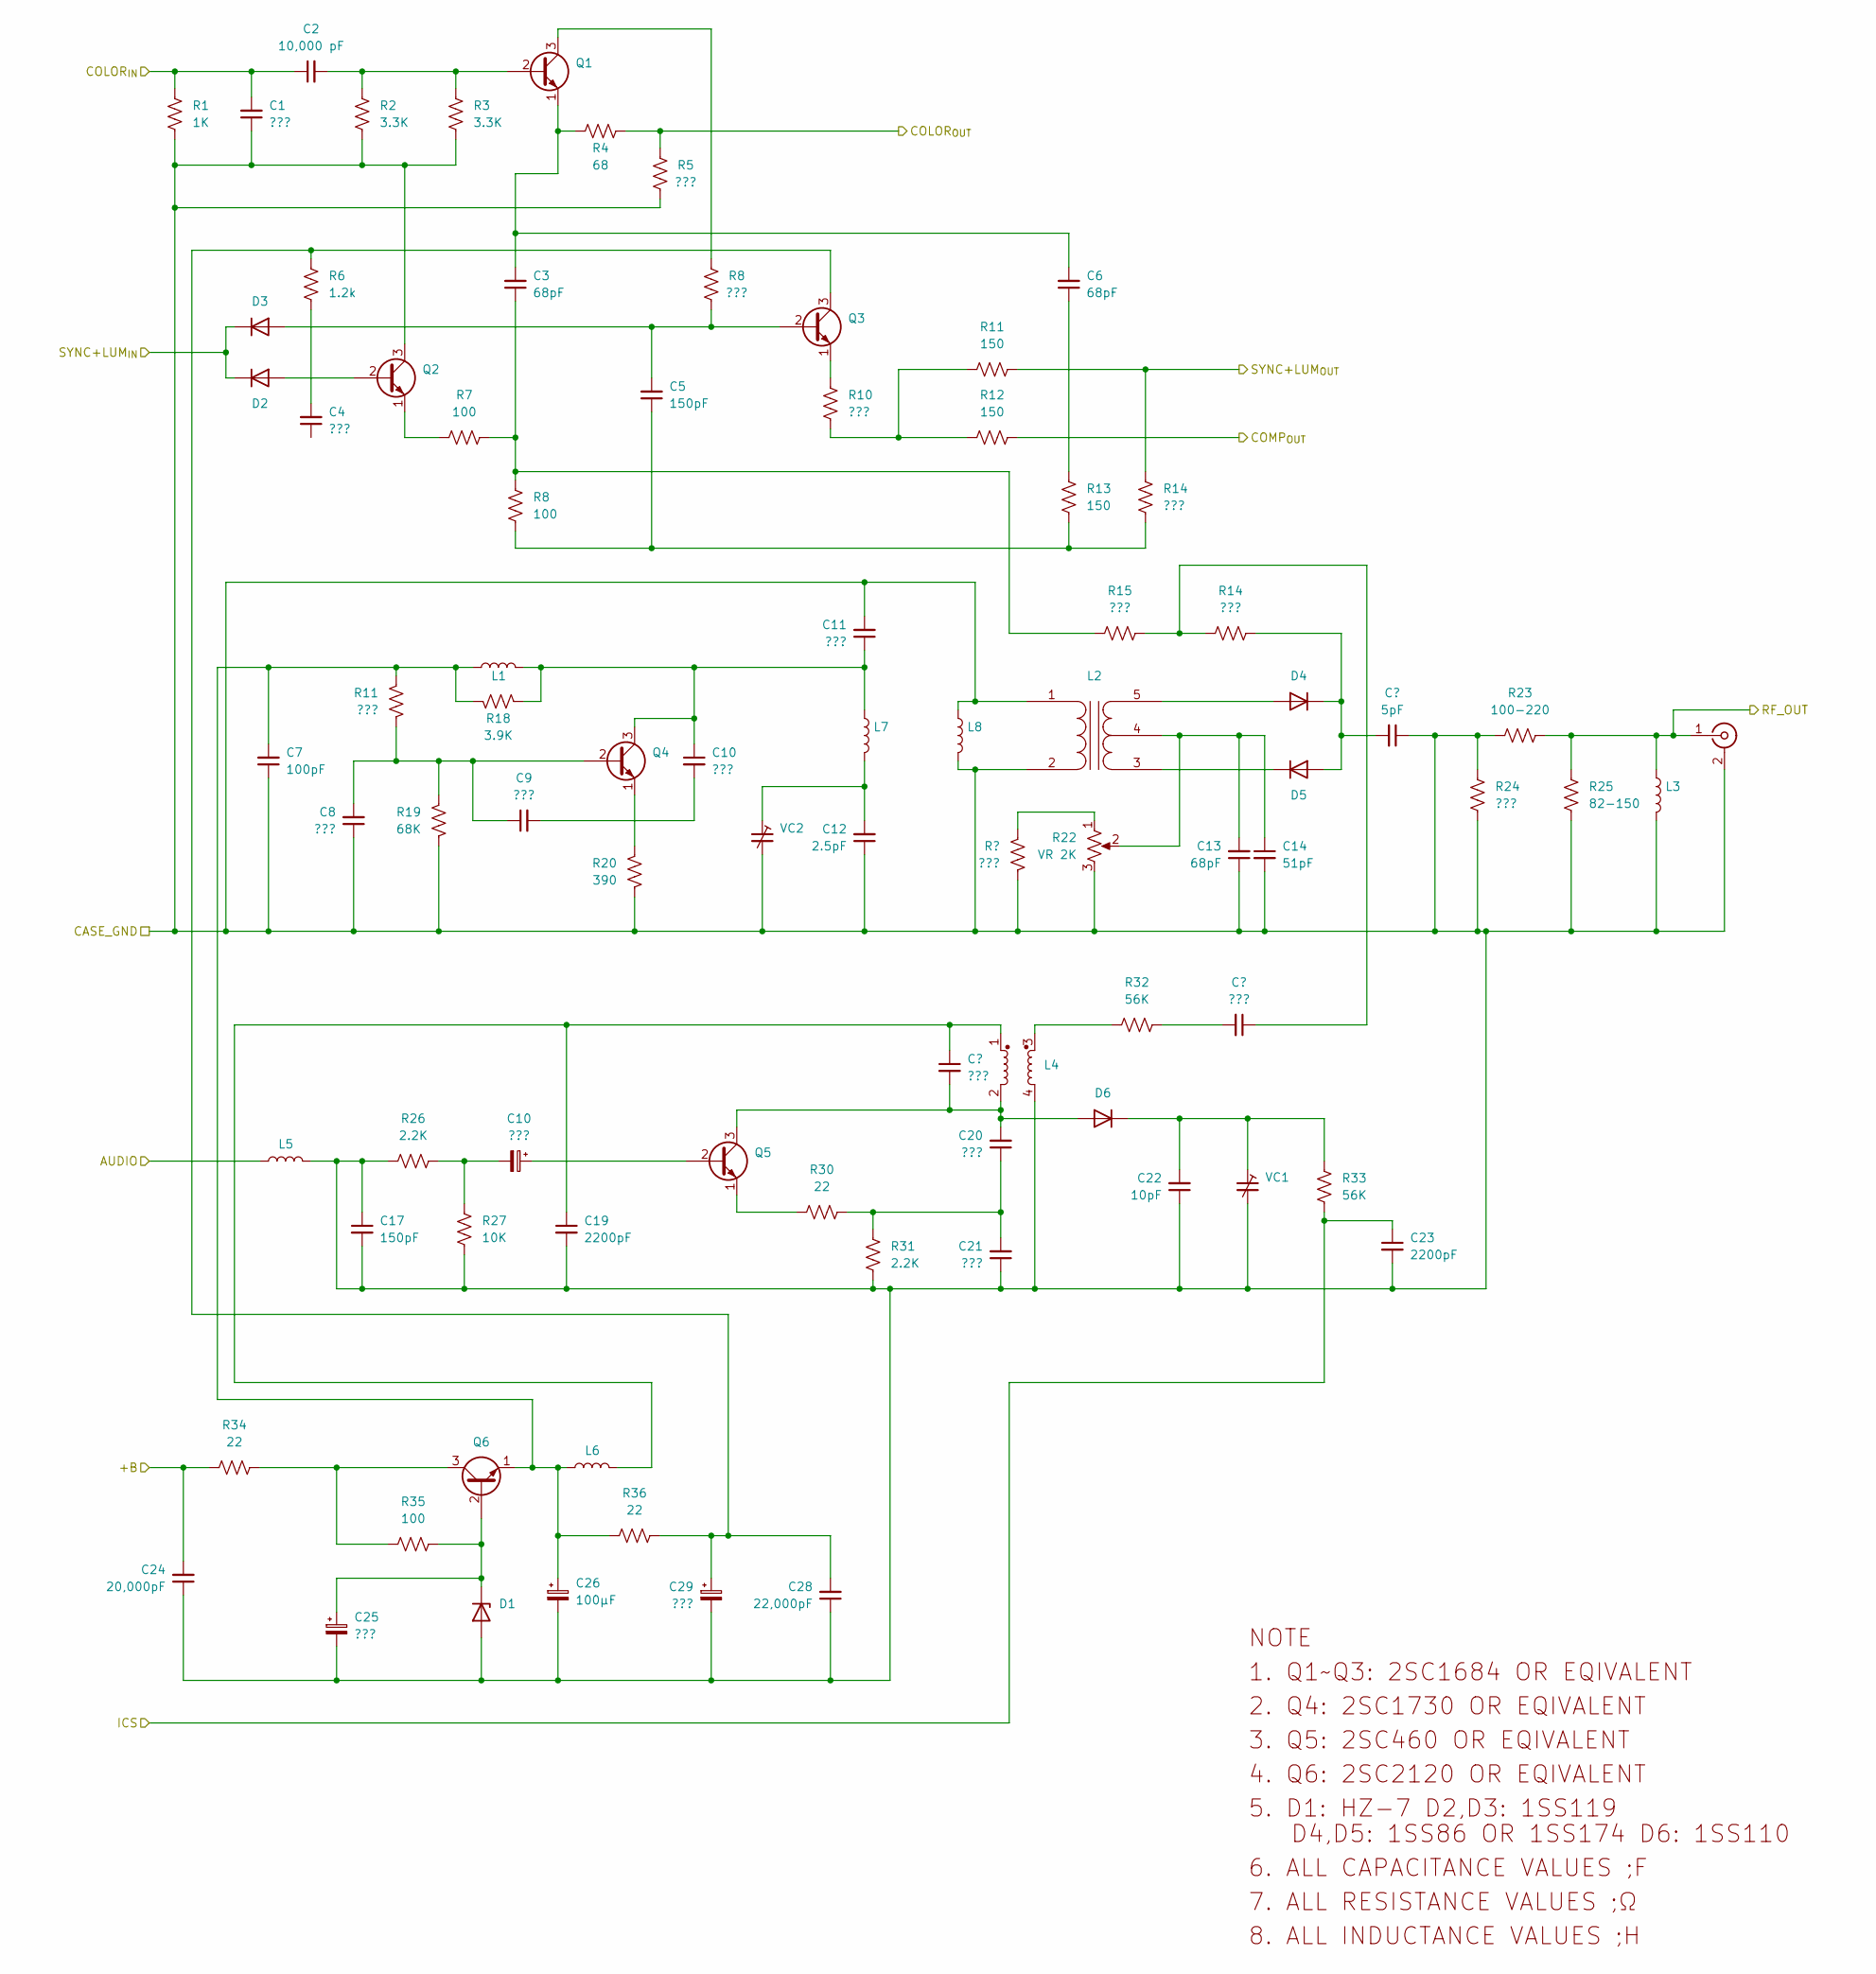
[picture p75: schematic Commodore 64 - RF Modulator for Schematic 2251138.kicad_sch]

Parts:
C1, C4, C8, C9, C10, C11, C20, C21, C25, C29: ???
C2: 10,000 pF
C3, C6, C13: 68pF
C5, C17: 150pF
C7: 100pF
C12: 2.5pF
C14: 51pF
C19, C23: 2200pF
C22: 10pF
C24: 20,000pF
C26: 100µF
C28: 22,000pF
D1: D_Zener
D2, D3, D4, D5, D6: D
L1, L3, L5, L6, L7, L8: L
L2: Transformer_1P_SS
L4: L_Coupled
Q1, Q2, Q3, Q4, Q5, Q6: TO-39-3
R1: 1K
R2, R3: 3.3K
R4: 68
R5, R8, R10, R11, R14, R15, R24: ???
R6: 1.2k
R7, R35: 100
R12, R13: 150
R18: 3.9K
R19: 68K
R20: 390
R22: VR 2K
R23: 100-220
R25: 82-150
R26, R31: 2.2K
R27: 10K
R30, R34, R36: 22
R32, R33: 56K
VC1, VC2: C_Trim_Small

Connections:
+B: C24.2, R34.2
AUDIO: L5.1
CASE_GND: C1.1, C7.1, C8.1, C11.2, C12.1, C13.1, C14.2, C17.1, C17.2, C19.2, C21.1, C22.1, C23.2, C24.1, C25.2, C26.2, C28.1, C29.2, D1.2 (A), L2.1 (AA), L2.2 (AB), L3.2, L4.4, L5.2, L8.1, L8.2, Q2.3 (C), R1.2, R2.2, R3.2, R5.1, R19.1, R20.1, R22.3, R23.2, R24.1, R24.2, R25.2, R26.1, R27.1, R31.1, VC1.2, VC2.2
COLOR_{IN}: C1.2, C2.1, R1.1
COLOR_{OUT}: R4.2, R5.2
COMP_{OUT}: R12.1
ICS: C23.1, R33.2
unnamed: C2.2, Q1.2 (B), R2.1, R3.1
unnamed: C3.1, R7.2, R8.2, R15.2
unnamed: C3.2, C6.2, Q1.1 (E), R4.1
unnamed: C4.2, R6.2
unnamed: C5.1, R8.1, R13.1, R14.1
unnamed: C5.2, D3.2 (A), Q3.2 (B), R8.1
unnamed: C6.1, R13.2
unnamed: C8.2, C9.1, Q4.2 (B), R11.1, R19.2
unnamed: C10.1, C11.1, L1.2, L7.1, Q4.3 (C), Q5.2 (B), R18.1
unnamed: C9.2, C10.2, R26.2, R27.2
unnamed: C12.2, L7.2, VC2.1
unnamed: C13.2, C14.1, L2.4 (SC), R22.2
unnamed: C19.1, L4.1, L6.2
unnamed: C20.1, C21.2, R30.2, R31.2
unnamed: C20.2, D6.2 (A), L4.2, Q5.3 (C)
unnamed: C22.2, D6.1 (K), R33.1, VC1.1
unnamed: C25.1, D1.1 (K), Q6.2 (B), R35.1
unnamed: C7.2, C26.1, L1.1, L6.1, Q6.1 (E), R11.2, R18.2, R36.2
unnamed: C28.2, C29.1, Q3.3 (C), R6.1, R36.1
unnamed: D2.2 (A), Q2.2 (B)
unnamed: D4.1 (K), D5.2 (A), R14.1
unnamed: D4.2 (A), L2.5 (SB)
unnamed: D5.1 (K), L2.3 (SA)
unnamed: L4.3, R32.2
unnamed: Q1.3 (C), R8.2
unnamed: Q2.1 (E), R7.1
unnamed: Q3.1 (E), R10.2
unnamed: Q4.1 (E), R20.2
unnamed: Q5.1 (E), R30.1
unnamed: Q6.3 (C), R34.1, R35.2
unnamed: R10.1, R11.1, R12.2
unnamed: R14.2, R15.1
RF_OUT: L3.1, R23.1, R25.1
SYNC+LUM_{IN}: D2.1 (K), D3.1 (K)
SYNC+LUM_{OUT}: R11.2, R14.2
