omega9380/Retro-Schematics/Tandy/TRS-80/Tandy TRS-80 Color Computer 1/Tandy TRS-80 Color Computer 1.kicad_sch

## KiCad design Tandy/TRS-80/Tandy TRS-80 Color Computer 1/Tandy TRS-80 Color Computer 1.kicad_sch (2022-07-01)

Schematic: Tandy TRS-80 Color Computer 1.kicad_sch

Parts:
C1, C19: 1µf
C2: 10µF
C3, C8, C12: 100µF
C4: 9-35pf
C5: 100µf
C6: 25µF
C7: 1800µF 35V
C9: 470µF 35V
C10: 10,000µF 16V
C11, C13, C83: 0.001µF
C14, C15: 220µF 16V
C16: 220µF
C17, C18, C23, C27, C28, C29, C31, C32, C33, C34, C35, C39, C44, C45, C46, C47, C48, C49, C50, C61, C62, C63, C64, C65, C66, C67, C68, C69, C70, C71, C72: 1µF
C20, C21, C22: 0.01µF 1.0 KV
C24, C25, C36, C37, C41, C43: 0.1µF
C26, C30, C54, C56, C59, C60, C74, C76, C77, C78, C79, C80, C81, C84: 0.022µF
C40: 0.1µf
C42, C57, C58: 0.01µF
C51: 39pf
C52: 20pF
C53: 56pF
C73, C75: 56pf
C82: 0.0022µF
CR1, CR2, CR3, CR5, CR6: 1N4148; D_DO-35_SOD27_P7.62mm_Horizontal
CR4, CR7: 1N4148
CR8: 1N4002; D_DO-35_SOD27_P7.62mm_Horizontal
CR9, CR10: 1N982
CR11: VM-28
CR12, CR13: 3E1
CR14, CR15: 1N4002
CR16: 1N5228
CR17: 1N4735 6.2V
E1, E2, E3, E4, E5, E6, E7, E8: CC1_Connector
F1: 0.7 AMP
H51: 5060B
H52-54: UNKNOWN_H_SYMBOL_COCO
H53: 6046
K1: R7336-1
KYBD1: KEYBOARD PBC
L2, L3: 3.3µh
P1: CARTRIDGE CONNECTOR
P2: DIN-4
P3, P4: DIN-6
P5: DIN-5
Q1: MPS3904; TO-92_Inline
Q2: 2N6594
Q3: TIP29
Q4: 2N2222; TO-92_Inline
R1, R2, R72: 100K
R3, R4, R5, R6, R7, R31, R32, R44, R64: 4.7K
R8: 18K
R9: 150Ω
R10, R22, R28, R29, R48, R51, R52, R68: 10K
R11: 20K
R12: 40.2K
R13: 80.6K
R14: 162K
R15: 324K
R16, R23: 3.9K
R17, R46, R58, R73, R74: 470Ω
R18: 750Ω
R19: 12K
R20: 360Ω
R21: 500Ω
R24, R43, R47: 1.5K
R25, R26, R30, R40, R57, R60: 1K
R27, R50: 100Ω 1/2W
R33, R71: 220Ω
R34: 8.2K
R35: 6.8K
R36, R37: 56K
R38, R53, R54: 15K
R39: 1.5M
R41: 24K
R42: 75K
R45: 180Ω
R49, R55, R56: 10M
R59: 68Ω 1/2W
R61, R63, R67: 1.2K
R62: 3.3K
R65: 560Ω
R66: 0.33Ω 2W
R69: 820Ω
R75, R76, R77, R78, R79: 33Ω
S1: Reset
S2: POWER SW
S3: CH SELECT
T1: TRANSFORMER
TP1, TP2, TP3, TP4, TP5, TP9, TP10, TP11, TP12: Test_Point
TPX_UNKNOWN: (no value)
U1: MC6809E; DIP-40_W15.24mm_LongPads
U2: MC14050B; DIP-16_W7.62mm_LongPads
U3, U28: MCM68A364; DIP-24_W15.24mm_LongPads
U4, U8: MC6821; DIP-40_W15.24mm_Socket_LongPads
U5: UM1285-8 RF Modulator
U6: 74LS273
U7: MC6847; DIP-40_W15.24mm_LongPads
U9: MC14529B; DIP-16_W7.62mm_LongPads
U10: MC6883; DIP-40_W15.24mm_LongPads
U11: 74LS138
U12: MC1372; DIP-14_W7.62mm_LongPads
U13: 723C; DIP-14_W7.62mm
U14: LM339
U15: 741C
U16: 74LS244
U17: 78M12; TO-220-3_Vertical
U18: 79M12; TO-220-3_Vertical
U19: 79L05; TO-220-3_Vertical
U20, U21, U22, U23, U24, U25, U26, U27: MCM4027A; DIP-16_W7.62mm_LongPads
U29: 74LS02
X1: 14.31818MHz

Connections:
3.58MHz: C53.2, R17.2, U7.33 (CLK), U12.2 (OSC)
A0: U4.36 (RS0), U8.36 (RS0)
A1: U4.35 (RS1), U8.35 (RS1)
A7: P1.26, U1.15 (A7), U3.1 (A7), U10.24 (A7)
A8: P1.27, U1.16 (A8), U3.23 (A8), U10.4 (A8)
A9: P1.28, U1.17 (A9), U3.22 (A9), U10.3 (A9)
A10: P1.29, U1.18 (A10), U3.19 (A10), U10.2 (A10)
A11: P1.30, U1.19 (A11), U3.18 (A11), U10.1 (A11)
A12: P1.31, U1.20 (A12), U3.21 (A12), U10.39 (A12)
A13: P1.37, U1.21 (A13), U10.38 (A13)
A14: P1.38, U1.22 (A14), U10.37 (A14)
A15: P1.39, U1.23 (A15), U10.36 (A15)
BIAS: C41.1, U7.9 (CHB), U12.6 (COLOR_{REF})
BLACK & WHITE: U7.28 (Y), U12.9 (Y)
CASSDIN: R39.2, R40.1, U4.2 (PA0), U14.13
CASSMOT: R71.2, U4.39 (CA2)
CASSOUT: R42.2, U14.8 (-)
CSN: C2.1, R31.2, R32.1, R33.1, R34.2, U9.13 (Y1)
D0: P1.10, U1.31 (D0), U3.9 (D0), U4.33 (D0), U8.33 (D0), U16.3 (1Y), U20.2 (D), U28.9 (D0)
D1: P1.11, U1.30 (D1), U3.10 (D1), U4.32 (D1), U8.32 (D1), U16.18 (2Y), U21.2 (D), U28.10 (D1)
D2: P1.12, U1.29 (D2), U3.11 (D2), U4.31 (D2), U8.31 (D2), U16.5 (3Y), U22.2 (D), U28.11 (D2)
D3: P1.13, U1.28 (D3), U3.13 (D3), U4.30 (D3), U8.30 (D3), U16.16 (4Y), U23.2 (D), U28.13 (D3)
D4: P1.14, U1.27 (D4), U3.14 (D4), U4.29 (D4), U8.29 (D4), U16.7 (5Y), U24.2 (D), U28.14 (D4)
D5: P1.15, U1.26 (D5), U3.15 (D5), U4.28 (D5), U8.28 (D5), U16.14 (6Y), U25.2 (D), U28.15 (D5)
D6: P1.16, U1.25 (D6), U3.16 (D6), U4.27 (D6), U8.27 (D6), U16.9 (7Y), U26.2 (D), U28.16 (D6)
D7: P1.17, U1.24 (D7), U3.17 (D7), U4.26 (D7), U8.26 (D7), U16.12 (8Y), U27.2 (D), U28.17 (D7)
DA0: U7.22 (DA0), U10.8 (DA0)
E: C75.2, P1.6, R74.2, TP5., U1.34 (EIN), U4.25 (E), U8.25 (E)
H1: R57.1, TPX_UNKNOWN.1, U4.22 (CS0), U4.24 (CS1), U9.1 (ST_{X})
HI: U8.22 (CS0), U8.24 (CS1)
JOYIN: R30.2, R49.2, U8.9 (PA7), U14.14
LSW: KYBD1.2, L3.1, U8.3 (PA1)
MA0: P1.19, R75.10, U1.8 (A0), U3.8 (A0), U10.16 (A0), U20.5 (A0), U21.5 (A0), U22.5 (A0), U23.5 (A0), U24.5 (A0), U25.5 (A0), U26.5 (A0), U27.5 (A0)
MA1: P1.20, R76.1, U1.9 (A1), U3.7 (A1), U10.17 (A1), U20.7 (A1), U21.7 (A1), U22.7 (A1), U23.7 (A1), U24.7 (A1), U25.7 (A1), U26.7 (A1), U27.7 (A1)
MA2: P1.21, R75.8, U1.10 (A2), U3.6 (A2), U10.18 (A2), U20.6 (A2), U21.6 (A2), U22.6 (A2), U23.6 (A2), U24.6 (A2), U25.6 (A2), U26.6 (A2), U27.6 (A2)
MA3: P1.22, R77.1, U1.11 (A3), U3.5 (A3), U10.19 (A3), U20.12 (A3), U21.12 (A3), U22.12 (A3), U23.12 (A3), U24.12 (A3), U25.12 (A3), U26.12 (A3), U27.12 (A3)
MA4: P1.23, R75.6, U1.12 (A4), U3.4 (A4), U10.21 (A4), U20.11 (A4), U21.11 (A4), U22.11 (A4), U23.11 (A4), U24.11 (A4), U25.11 (A4), U26.11 (A4), U27.11 (A4)
MA5: P1.24, R75.2, U1.13 (A5), U3.3 (A5), U10.22 (A5), U20.10 (A5), U21.10 (A5), U22.10 (A5), U23.10 (A5), U24.10 (A5), U25.10 (A5), U26.10 (A5), U27.10 (A5)
MA6: P1.25, R75.4, U1.14 (A6), U3.2 (A3), U10.23 (A6), U20.13 (A6), U21.13 (A6), U22.13 (A6), U23.13 (A6), U24.13 (A6), U25.13 (A6), U26.13 (A6), U27.13 (A6)
MD0: U6.18 (8D), U16.17 (1A), U20.14 (Q)
MD1: U6.17 (7D), U16.2 (2A), U21.14 (Q)
MD2: U6.14 (5D), U16.15 (3A), U22.14 (Q)
MD3: U6.13 (3D), U16.4 (4A), U23.14 (Q)
MD4: U6.8 (4D), U16.13 (5A), U24.14 (Q)
MD5: U6.7 (6D), U16.6 (6A), U25.14 (Q)
MD6: U6.4 (2D), U16.11 (7A), U26.14 (Q)
MD7: U6.3 (1D), U16.8 (8A), U27.14 (Q)
unnamed: C1.1, C40.1, S1.1 (A)
unnamed: C2.2, C81.2, P5.4
unnamed: C3.2, U10.40 (VCC)
unnamed: C4.1, U10.5 (OSC_{IN}), X1.2
unnamed: C4.2, C51.1, X1.3
unnamed: C5.1, U1.7 (VCC)
unnamed: C7.2, CR11., CR14.1 (K), U17.
unnamed: C10.1, Q2.2 (E), R59.2, S2.
unnamed: C11.1, U13.13 (FC)
unnamed: C11.2, R63.2, U13.4 (-)
unnamed: C12.1, C25.1, CR16.2 (A), Q1.3 (C), R16.2, R69.2
unnamed: C12.2, C24.1, C25.2, R69.1
unnamed: C13.1, C76.2
unnamed: C13.2, C76.1
unnamed: C7.1, C14.1, C36.1, U17.
unnamed: C14.2, C36.2, CR14.2 (A), R58.1, TP9., U13.11 (VC), U17.
unnamed: C15.1, C17.1, C37.1, U18.
unnamed: C15.2, C37.2, CR15.1 (K), TP10., U18.
unnamed: C16.1, CR17.1 (K), R63.1, R66.2, TP12., U13.3 (CS)
unnamed: C16.2, CR17.2 (A)
unnamed: C9.2, C17.2, CR11., CR15.2 (A), R67.2, U18.
unnamed: C18.1, C36.1, U19.
unnamed: C18.2, R67.1, U19.
unnamed: C19.1, R58.2, U13.12 (V+)
unnamed: C19.2, U13.7 (V-)
unnamed: C20.1, C22.2, E6., T1.
unnamed: C20.2, C21.1, E4., E5., E8., T1.
unnamed: C21.2, C22.1, F1.2, T1.
unnamed: C8.1, C23.1, C29.1, C31.1, C32.1, C33.1, C35.1, C39.1, C45.1, C46.1, C47.1, C48.1, C49.1, C61.1, C62.1, C63.1, C64.1, C65.1, C66.1, C67.1, C68.1, C69.1, C70.1, C71.1, C72.1, U20.16 (VSS), U21.16 (VSS), U22.16 (VSS), U23.16 (VSS), U24.16 (VSS), U25.16 (VSS), U26.16 (VSS), U27.16 (VSS)
unnamed: C23.2, C29.2, C33.2, C47.2, C63.2, C66.2, C69.2, C72.2, U20.1 (VBB), U21.1 (VBB), U22.1 (VBB), U23.1 (VBB), U24.1 (VBB), U25.1 (VBB), U26.1 (VBB), U27.1 (VBB)
unnamed: C24.2, CR16.1 (K), R45.2
unnamed: C26.1, C27.1, C28.1, C30.1, C34.1, C44.1, C50.1, C59.1, C60.1, C74.1, C83.1, C84.1
unnamed: C26.2, C27.2, C28.2, C30.2, C34.2, C44.2, C50.2, C59.2, C60.2, C74.2, C83.2, C84.2
unnamed: C31.2, C35.2, C45.2, C48.2, C61.2, C64.2, C67.2, C70.2, U20.9 (VCC), U21.9 (VCC), U22.9 (VCC), U23.9 (VCC), U24.9 (VCC), U25.9 (VCC), U26.9 (VCC), U27.9 (VCC)
unnamed: C8.2, C32.2, C39.2, C46.2, C49.2, C62.2, C65.2, C68.2, C71.2, U20.8 (VDD), U21.8 (VDD), U22.8 (VDD), U23.8 (VDD), U24.8 (VDD), U25.8 (VDD), U26.8 (VDD), U27.8 (VDD)
unnamed: C36.2, TP11., U19.
unnamed: C40.2, CR1.1 (K), CR2.1 (K), CR3.2 (A), R1.1, S1.2 (B)
unnamed: C42.1, R18.1
unnamed: C42.2, U12.8 (C_{MOD})
unnamed: C6.1, C43.1, U12.11 (VCC)
unnamed: C6.2, C43.2
unnamed: C51.2, R43.2, X1.1
unnamed: C52.2, R10.1, R11.1, R12.1, R13.1, R14.1, R15.1, R72.2, U9.14 (Y0)
unnamed: C54.1, C56.1, C57.1, C58.1, C78.1, C79.1, P3.3, P3.6, P4.3, P4.6
unnamed: C54.2, P3.5, P4.2, P4.5, R50.1, U9.5 (X3)
unnamed: C56.2, P4.1, U9.4 (X2)
unnamed: C57.2, L3.2, P4.4
unnamed: C58.2, L2.2, P3.4
unnamed: C73.1, C75.1
unnamed: C78.2, P3.1, U9.2 (X0)
unnamed: C79.2, P3.2, U9.3 (X1)
unnamed: C80.1, CR9.2 (A), K1., P5.3
unnamed: C80.2, CR10.2 (A), K1., P5.1
unnamed: C81.1, C82.1, P5.2, R32.2, R41.1
unnamed: C82.2, P5.5, R41.2, R42.1
unnamed: CR3.1 (K), R1.2
unnamed: CR4.1 (K), R34.1, R35.2
unnamed: CR4.2 (A), R33.2, R38.1
unnamed: CR5.1 (K), R28.2, U14.6 (-)
unnamed: CR5.2 (A), P2.1
unnamed: CR6.1 (K), R29.2, U14.4 (-)
unnamed: CR6.2 (A), P2.2
unnamed: CR7.1 (K), K1.
unnamed: CR7.2 (A), K1.
unnamed: CR8.1 (K), U12.14 (RFTANK_{2})
unnamed: CR8.2 (A), R20.1, U12.13 (RFTANK_{1})
unnamed: CR9.1 (K), CR10.1 (K)
unnamed: CR11., S2.
unnamed: CR12.1 (K), CR13.1 (K), E3.
unnamed: CR12.2 (A), T1.
unnamed: CR13.2 (A), T1.
unnamed: E1., S2., T1.
unnamed: E2., S2., T1.
unnamed: E3., S2.
unnamed: E7., F1.1
unnamed: K1., Q4.3 (C)
unnamed: KYBD1.4, U8.4 (PA2)
unnamed: KYBD1.5, U8.5 (PA3)
unnamed: KYBD1.6, U8.6 (PA4)
unnamed: KYBD1.7, U8.7 (PA5)
unnamed: KYBD1.8, U8.8 (PA6)
unnamed: KYBD1.9, U8.10 (PB0)
unnamed: KYBD1.10, U8.11 (PB1)
unnamed: KYBD1.11, U8.12 (PB2)
unnamed: KYBD1.12, U8.13 (PB3)
unnamed: KYBD1.13, U8.14 (PB4)
unnamed: KYBD1.14, U8.15 (PB5)
unnamed: KYBD1.15, U8.16 (PB6)
unnamed: KYBD1.16, U8.17 (PB7)
unnamed: P1.33, P1.34
unnamed: P2.4, R27.1
unnamed: Q1.1 (E), R46.1, R47.1, U5.1 (VIDEO)
unnamed: Q1.2 (B), R8.1, R19.1
unnamed: Q2.1 (B), Q3.3 (C), R59.1
unnamed: Q2.3 (C), Q3.2 (E), R66.1
unnamed: Q3.1 (B), R65.1, U13.10 (VO)
unnamed: Q4.2 (B), R71.1
unnamed: R3.2, R4.2, R5.2, R6.2
unnamed: R10.2, U2.10 (OUT_{A})
unnamed: R11.2, U2.6 (OUT_{A})
unnamed: R12.2, U2.12 (OUT_{A})
unnamed: R13.2, U2.4 (OUT_{A})
unnamed: R14.2, U2.15 (OUT_{A})
unnamed: R15.2, U2.2 (OUT_{A})
unnamed: R16.1, R19.2, U12.12 (RF_MOD)
unnamed: R18.2, U12.10 (C)
unnamed: R21.1, R47.2
unnamed: R9.2, R21.2
unnamed: R8.2, R21.3, R46.2
unnamed: R22.1, U4.11 (PB1)
unnamed: R22.2, U5.3 (AUDIO), U9.10 (Y)
unnamed: R23.1, R24.2, U15.2 (-)
unnamed: R25.2, R55.1, U4.40 (CA1), U14.1
unnamed: R27.2, U15.6
unnamed: R35.1, R36.1, U14.10 (-)
unnamed: R36.2, R37.2, R40.2
unnamed: R37.1, R38.2, R39.1, U14.11 (+)
unnamed: R43.1, U10.6 (OSC_{OUT})
unnamed: R44.1, U6.1 (~CL)
unnamed: R45.1, U5.2 (VCC)
unnamed: R48.1, R49.1, U14.9 (+)
unnamed: R48.2, U9.9 (Z)
unnamed: R51.2, R53.1, R55.2, U14.7 (+)
unnamed: R52.2, R54.1, R56.2, U14.5 (+)
unnamed: R60.1, R61.1
unnamed: R60.2, U13.5 (+)
unnamed: R60.3, R62.1
unnamed: R61.2, U13.6 (VREF)
unnamed: R64.1, R65.2, U13.2 (CL)
unnamed: R73.2, U10.13 (Q)
unnamed: R74.1, U10.14 (E), U29.9
unnamed: R75.1, U10.33 (MA5)
unnamed: R75.3, TPX_UNKNOWN.1
unnamed: R75.5, U10.32 (MA4)
unnamed: R75.7, U10.30 (MA2)
unnamed: R75.9, U10.28 (MA0)
unnamed: R76.2, U10.29 (MA1)
unnamed: R77.2, U10.31 (MA3)
unnamed: R78.2, U10.11 (~CAS)
unnamed: R79.2, U10.10 (~WE)
unnamed: S3.1 (A), U5.4 (CH_SEL)
unnamed: S3.2 (B), U5. (GND)
unnamed: TPX_UNKNOWN.1, U10.34 (MA6)
unnamed: U2.3 (IN_{A}), U4.4 (PA2)
unnamed: U2.5 (IN_{A}), U4.6 (PA4)
unnamed: U2.7 (IN_{A}), U4.8 (PA6)
unnamed: U2.9 (IN_{A}), U4.9 (PA7)
unnamed: U2.11 (IN_{A}), U4.7 (PA5)
unnamed: U2.14 (IN_{A}), U4.5 (PA3)
unnamed: U4.13 (PB3), U7.39 (CSS)
unnamed: U4.14 (PB4), U7.30 (GM0), U7.31 (~INT/EXT)
unnamed: U4.15 (PB5), U7.29 (GM1)
unnamed: U4.16 (PB6), U7.27 (GM2)
unnamed: U4.17 (PB7), U7.35 (~A/G)
unnamed: U6.2 (1Q), U7.34 (~A/S), U7.40 (DD7)
unnamed: U6.5 (2Q), U7.2 (DD6), U7.32 (INV)
unnamed: U6.6 (3Q), U7.8 (DD5)
unnamed: U6.9 (4Q), U7.7 (DD4)
unnamed: U6.12 (5Q), U7.6 (DD3)
unnamed: U6.15 (6Q), U7.5 (DD2)
unnamed: U6.16 (7Q), U7.4 (DD1)
unnamed: U6.19 (8Q), U7.3 (DD0)
unnamed: U10.25 (S2), U11.3 (C), U29.8
unnamed: U10.26 (S1), U11.2 (B)
unnamed: U10.27 (S0), U11.1 (A)
unnamed: U11.4 (G2A), U29.10
unnamed: U11.5 (G2B), U11.8 (GND)
unnamed: U3.20 (~E), U11.13 (Y2)
unnamed: U11.14 (Y1), U28.20 (~E)
unnamed: U7.10 (ɸB), U12.5 (COLOR_{B})
unnamed: U7.11 (ɸA), U12.7 (COLOR_{A})
unnamed: U2.8 (GND), U14.12 (V-)
unnamed: U29.2, U29.3, U29.5, U29.6, U29.11, U29.12
PIA0: U8.23 (~CS2)
Q: C73.2, P1.7, R73.1, U1.35 (QIN)
RAMSZ: TPX_UNKNOWN.1, U4.12 (PB2)
RS232IN: R26.2, R56.1, U4.10 (PB0), U14.2
RS232OUT: U4.3 (PA1), U15.3 (+)
RSW: KYBD1.1, L2.1, U8.2 (PA0)
R/~W: P1.18, TP1., U1.32 (R/~W), U4.21 (R/~W), U8.21 (R/~W), U10.15 (R/~W)
SEL1: U8.39 (CA2), U9.6 (A)
SEL2: U8.19 (CB2), U9.7 (B)
SND: P1.35, U9.12 (Y2)
SNDEN: U4.19 (CB2), U9.15 (ST_{Y})
VDG CLK: CR2.2 (A), R17.1, TP5., U10.7 (VCLK)
~CART: P1.8, R68.1, U4.18 (CB1)
~CAS: R78.1, U20.15 (~CAS), U21.15 (~CAS), U22.15 (~CAS), U23.15 (~CAS), U24.15 (~CAS), U25.15 (~CAS), U26.15 (~CAS), U27.15 (~CAS)
~CTS: P1.32, U11.12 (Y3)
~FIRQ: R5.1, U1.4 (~FIRQ), U4.37 (~IRQB), U4.38 (~IRQA)
~FS: U7.12 (~MS), U7.37 (~FS), U8.18 (CB1)
~HALT: P1.3, R3.1, U1.40 (~HALT)
~HS: U7.38 (~HS), U8.40 (CA1), U10.9 (~HS)
~IRQ: R6.1, U1.3 (~IRQ), U8.37 (~IRQB), U8.38 (~IRQA)
~MRD: U11.15 (Y0), U16.1 (1~G), U16.19 (2~G)
~NMI: P1.4, R4.1, U1.2 (~NMI)
~PIA0: U11.11 (Y4)
~PIA1: U4.23 (~CS2), U11.10 (Y5)
~RAS: U6.11 (CK), U10.12 (~RAS0), U20.4 (~RAS), U21.4 (~RAS), U22.4 (~RAS), U23.4 (~RAS), U24.4 (~RAS), U25.4 (~RAS), U26.4 (~RAS), U27.4 (~RAS)
~RESET: C1.2, CR1.2 (A), P1.5, R2.1, TP2., U1.37 (~RESET), U4.34 (~RESET), U8.34 (~RESET)
~SCS: P1.36, U11.9 (Y6)
~SLENB: P1.40, R7.1, U11.6 (G1)
~WE: R79.1, U20.3 (~WE), U21.3 (~WE), U22.3 (~WE), U23.3 (~WE), U24.3 (~WE), U25.3 (~WE), U26.3 (~WE), U27.3 (~WE)

Notes on the sheet:
NOTE FROM OMEGA9380 On the original schematic, it looks like L2 connects to nothing. LSW connects to L3 and there is a reference on Sheet 3 to RSW. I am assuming that there was supposed to be a reference to RSW connected to L2.
COLOR BURST - PORTCH ADJUST PG. 32
LIMITING -ABOVE +6.2V
SAM SYNC
100µA
2N6-594
100MA
ROM EXPANSION (8K)
INPUTS: CA1, CB1 OUTPUTS: CA2, CB2
HANDWRITTEN NOTE: signals are logoing (sic)
H52
+5V REG
VERTICAL SYNC
-5V REGULATOR
NOTE FROM OMEGA9380: I don't know what this is supposed to show. I think it means that pin 35 on the SAM goes straight to ground on the 16K model but passes thru a resistor (R75) for the 4K model. This is how it is shown on the schematic.
POWER SUPPLY
CASSETTE
SHEET 2
HANDWRITTEN NOTES: 1/2 of sound chip (sound selects => joystick selects)
HANDWRITTEN NOTES: 6 Mlte(?) bandwidth/TV Channel Sound - FM Everything else is Arl(?) in TV - black & white Color - phase modulated TV has no sidebands
VIDEO SELECTS
5072B & 5071B
BASIC ROM (8K)
H54
SHEET 1
GROUNDED CASE
SINGLE BIT SOUND
ON OLD SETS USED TO ADJUST +5V
BRIDGE RECTIFIER ~20V
SPARE GATES
+12V
16K
HANDWRITTEN NOTE: Write to mem is directly off data lines Refresh during horizontal sync
1.35 AMPS
PIA
SHEET 3
NOTE 1: THIS SECTION MAY ALSO APPEAR WITH R73 THRU R77 REPLACED WITH FERRITE BEADS
10MS (SAM CHIP)
RIGHT JOYSTICK
HANDWRITTEN NOTES: (about 7mV/step) 0.25 - 4.7V in 64 steps
HANDWRITTEN NOTE: 5V relays are weak
COLOR VDG
NOTE FROM OMEGA9380: Again, shown just as it is on the original schematic.
CARTRIDGE
TRANSFORMER ASSEMBLY
PORT A
16K RAM BIAS
-12V REGULATOR
+12V REGULATOR
DATA LATCH
FILTER CAPS
RS232 LEVEL CONVERTERS
D/A (SOUND, JOYSTICK)
5%, 1% +5 REG NOT EXCHANGEABLE
400MA
PORT B
LEFT JOYSTICK
